PumaFPV/PMK/Documentation/FPC-Contact-layout.png

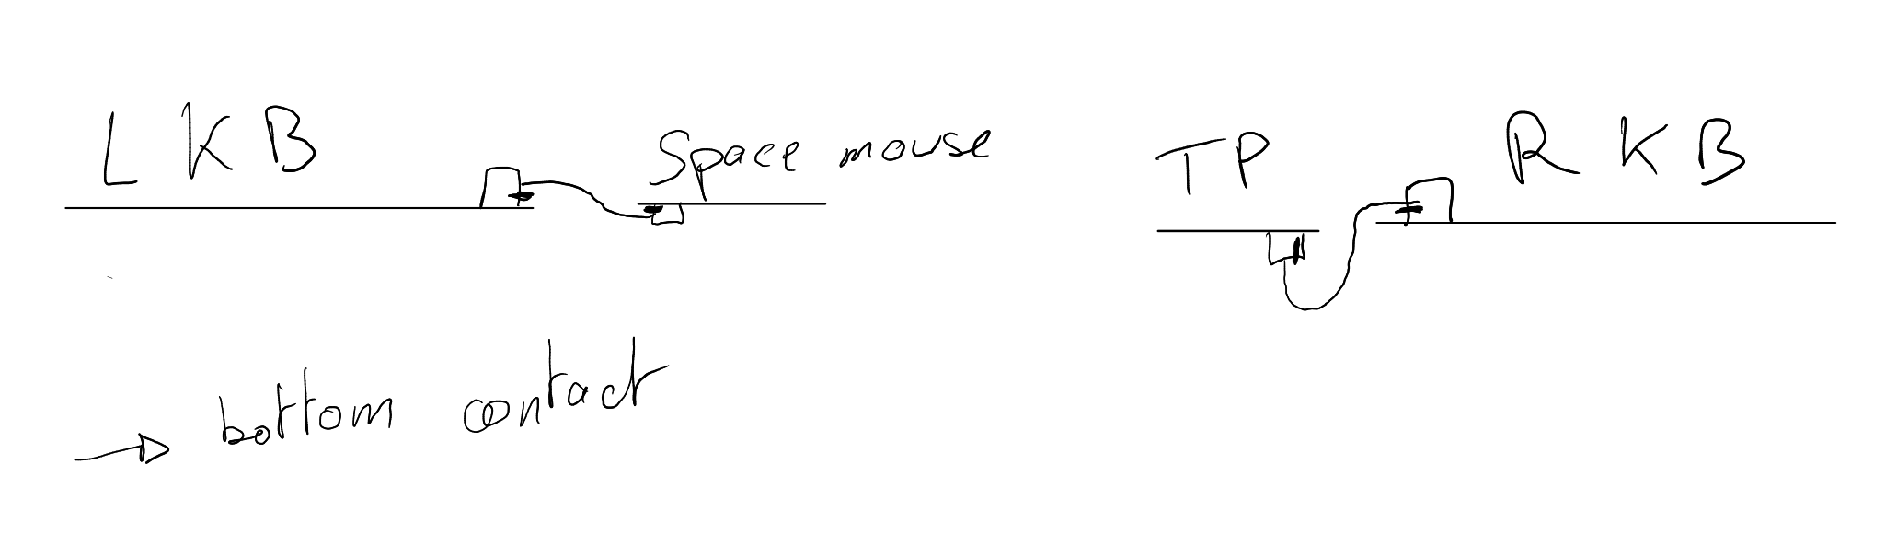
Documentation/FPC-Contact-layout.png
