PumaFPV/PMK/Documentation/Marketing/rightKB_nobg.png

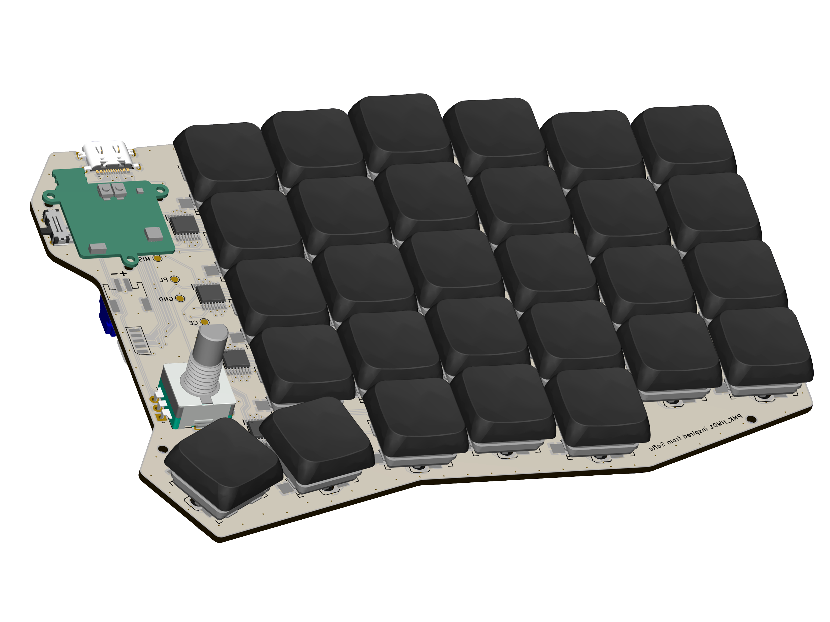
Documentation/Marketing/rightKB_nobg.png
