PumaFPV/PMK/Software/pmk_configurator/TopView.png

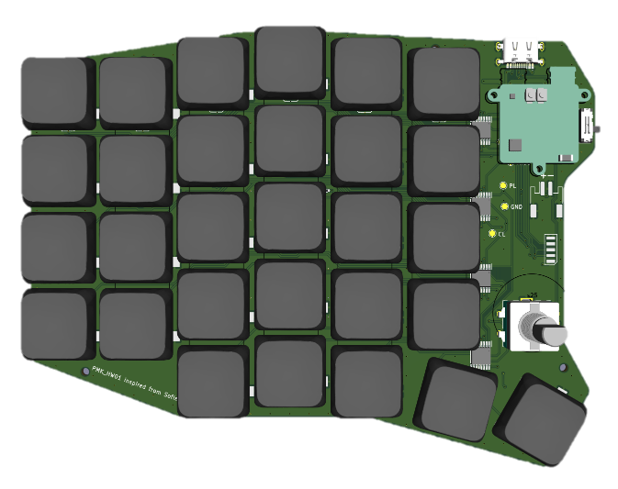
Software/pmk_configurator/TopView.png
