PumaFPV/PMK/Software/pmk_configurator/TopViewWithCasingNoBG.png

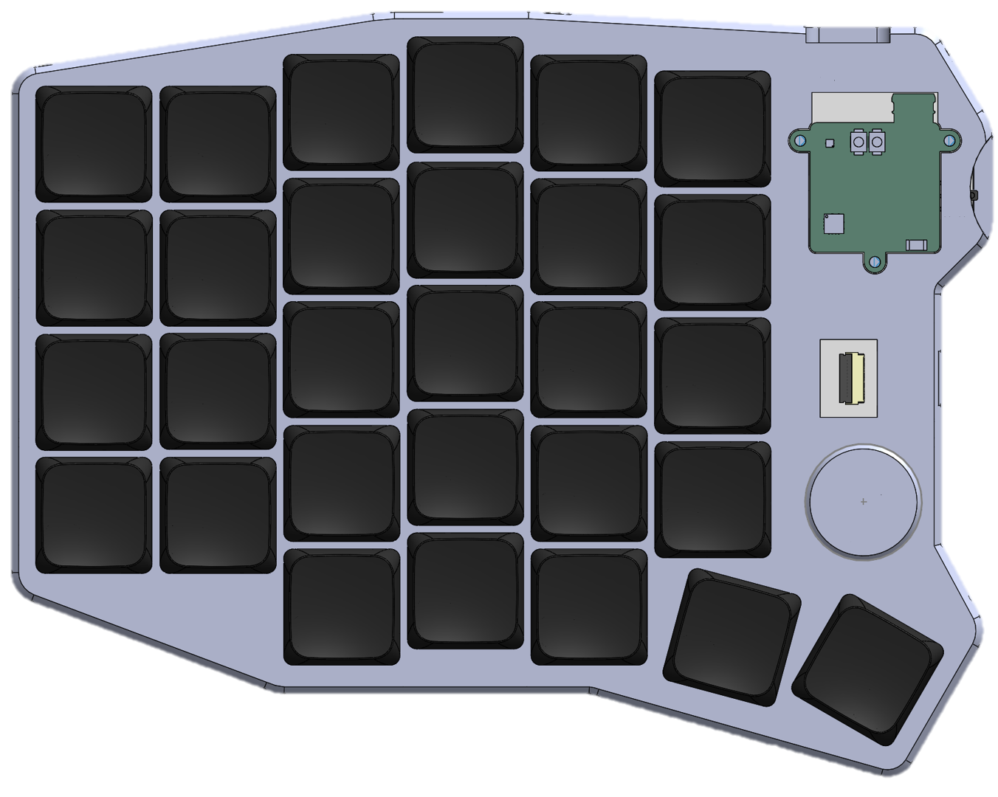
Software/pmk_configurator/TopViewWithCasingNoBG.png
