PumaFPV/PMK/Software/Ticket documentation/Debounce/key_debounce1.png

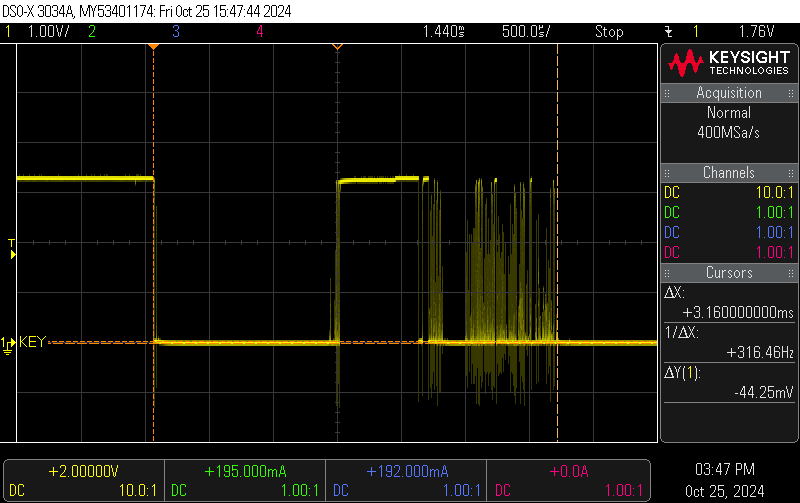
Software/Ticket documentation/Debounce/key_debounce1.png
