PumaFPV/PMK/Software/Ticket documentation/Debounce/key_debounce2.png

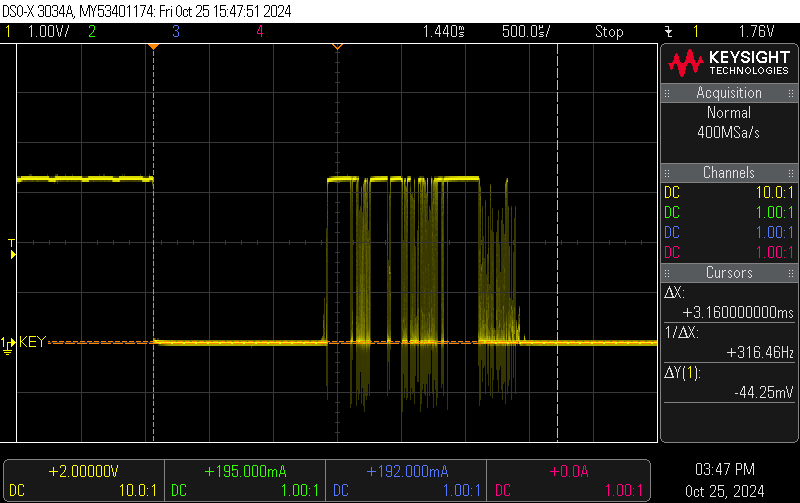
Software/Ticket documentation/Debounce/key_debounce2.png
