PumaFPV/PMK/Software/Ticket documentation/Debounce/key_debounce4.png

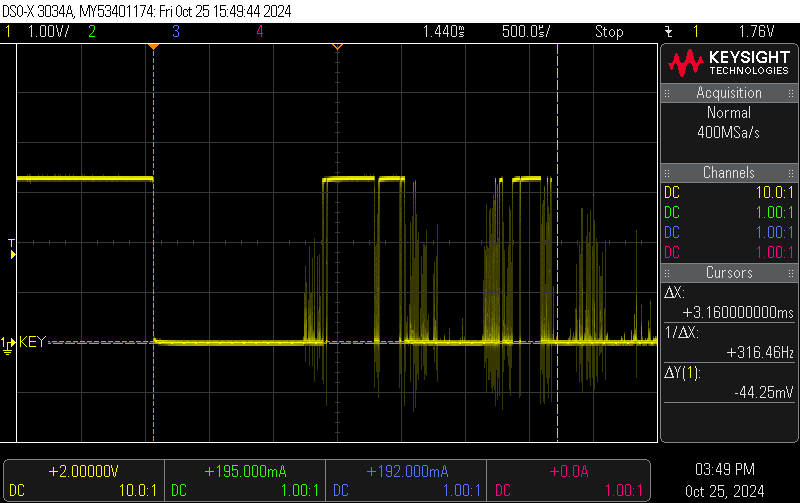
Software/Ticket documentation/Debounce/key_debounce4.png
