PumaFPV/PMK/Software/Ticket documentation/Debounce/key_debounce.png

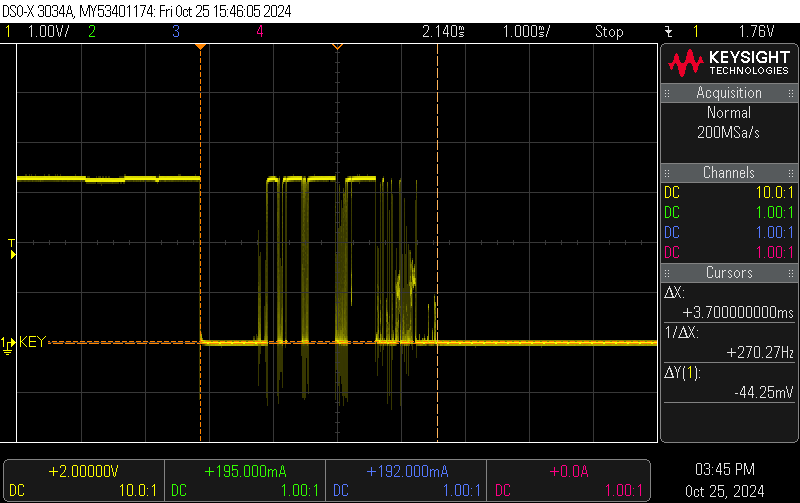
Software/Ticket documentation/Debounce/key_debounce.png
