PumaFPV/PMK/Software/Ticket documentation/Debounce/PU_KEY_AC2.png

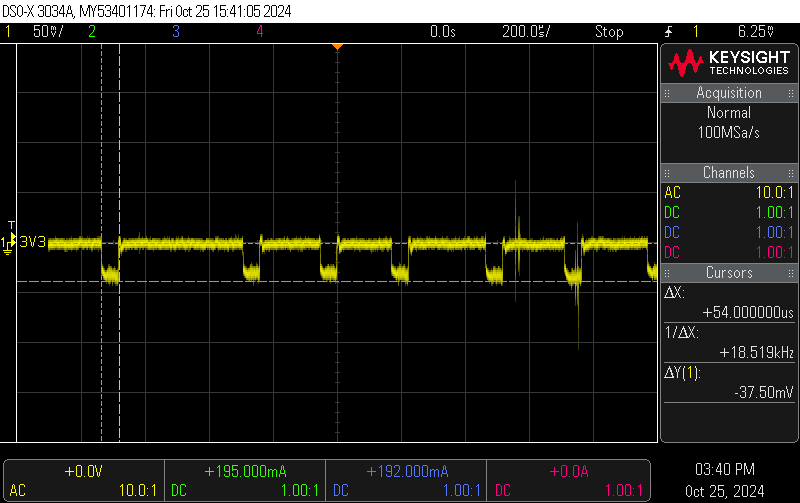
Software/Ticket documentation/Debounce/PU_KEY_AC2.png
