PumaFPV/PMK/Software/Ticket documentation/Debounce/PU_KEY_AC5.png

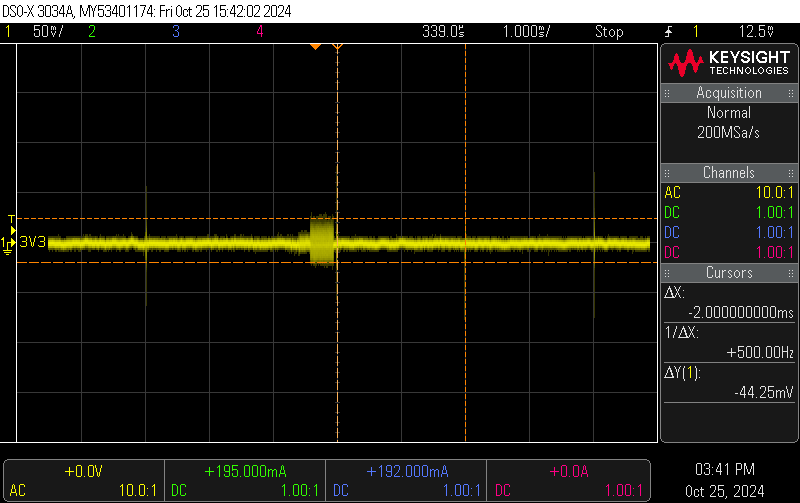
Software/Ticket documentation/Debounce/PU_KEY_AC5.png
