PumaFPV/PMK/Software/Ticket documentation/Debounce/PU_KEY_AC6.png

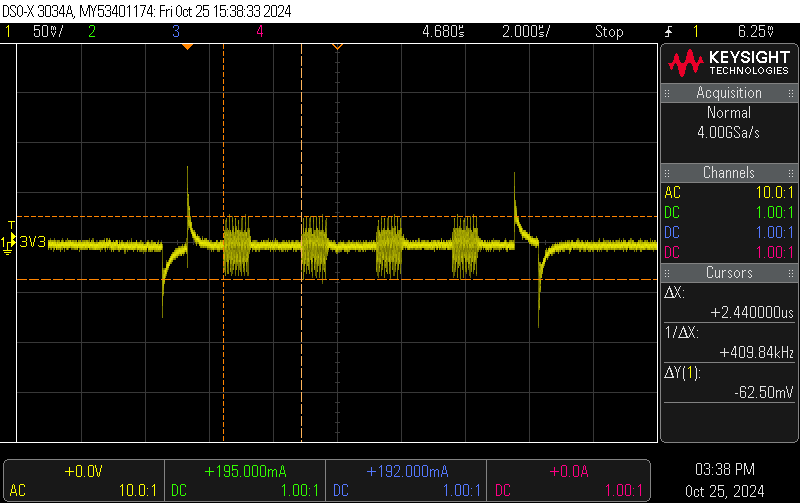
Software/Ticket documentation/Debounce/PU_KEY_AC6.png
