PumaFPV/PMK/Software/Ticket documentation/Debounce/PU_KEY_AC.png

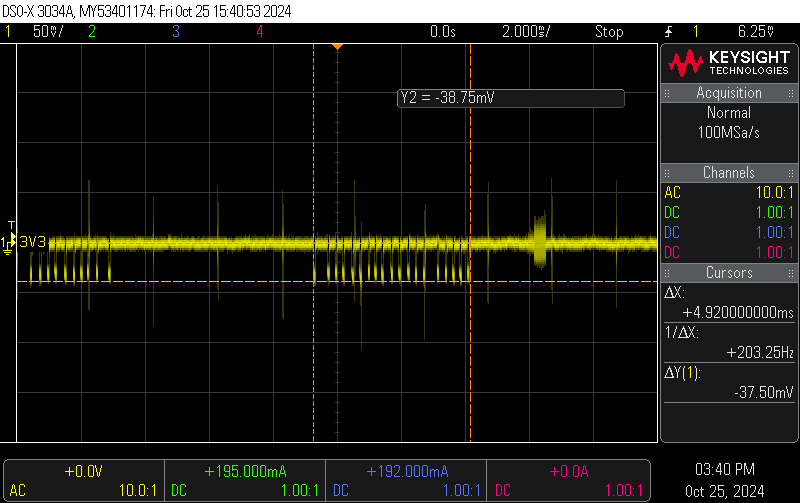
Software/Ticket documentation/Debounce/PU_KEY_AC.png
