PumaFPV/PMK/Mecha/Dongle/PMK_Dongle_00.step

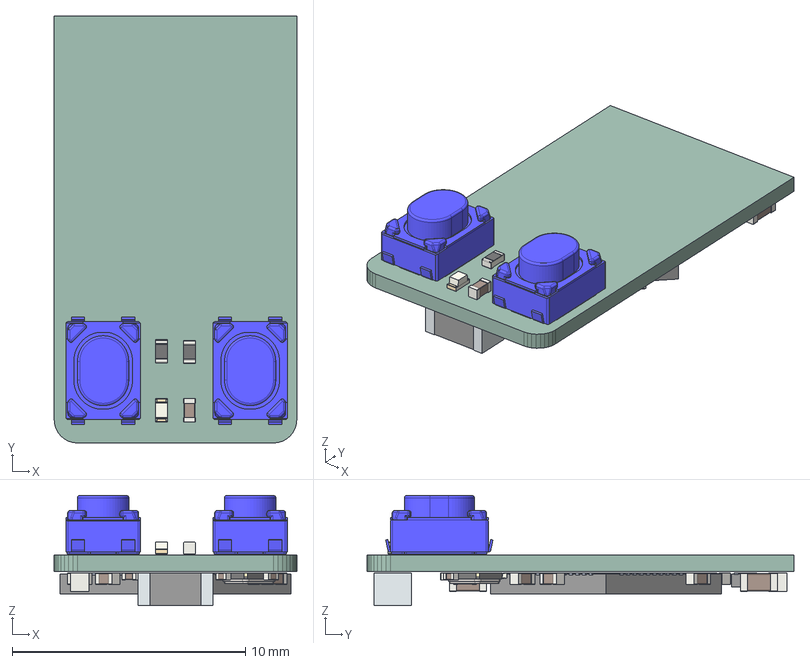
[picture p38: CAD file, 2024-03-06]
Mecha/Dongle/PMK_Dongle_00.step
10.4 x 18.3 x 4.72 mm
PMK_Dongle PCB
