PumaFPV/PMK/Mecha/Keyboard/KeyCap holder/holder^keycap holder.STL

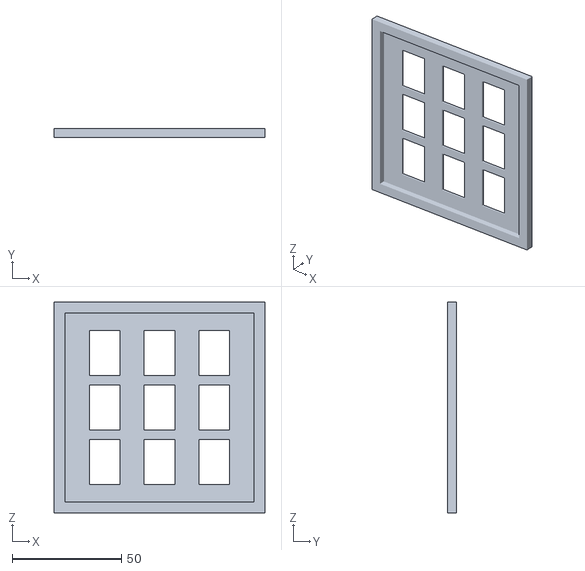
[picture p39: CAD file, 2023-05-14]
Mecha/Keyboard/KeyCap holder/holder^keycap holder.STL
96.7 x 4.00 x 96.7
