PumaFPV/PMK/Mecha/Keyboard/Keycap/MBK_Keycap_-_1.5u.SLDPRT

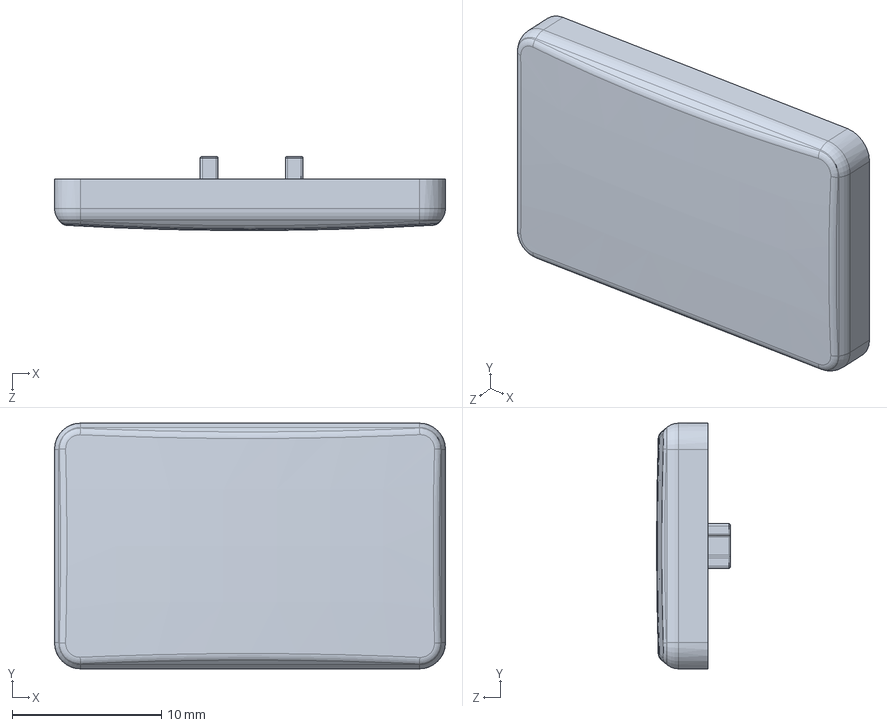
[picture p40: CAD file, 2023-08-28]
Mecha/Keyboard/Keycap/MBK_Keycap_-_1.5u.SLDPRT
26.2 x 16.5 x 4.95 mm
