PumaFPV/PMK/Mecha/Keyboard/PMK_00/PMK_Keyboard.step.STL

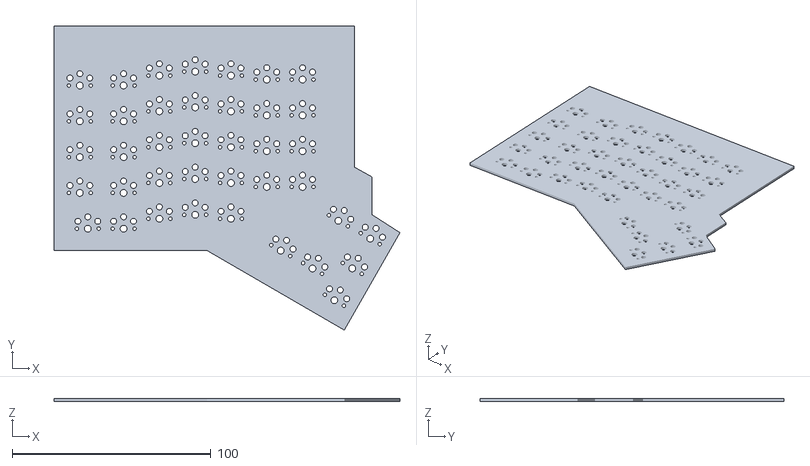
[picture p41: CAD file, 2023-01-25]
Mecha/Keyboard/PMK_00/PMK_Keyboard.step.STL
174.0 x 153.0 x 1.60
