PumaFPV/PMK/Mecha/Keyboard/PMK_01/UpperCasing.SLDPRT

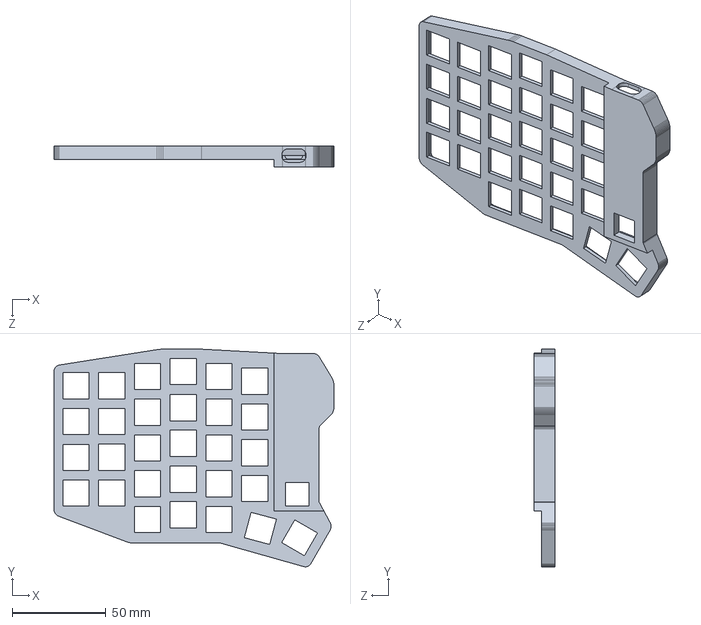
[picture p42: CAD file, 2024-06-07]
Mecha/Keyboard/PMK_01/UpperCasing.SLDPRT
149.2 x 116.0 x 11.0 mm
