PumaFPV/PMK/Mecha/Keyboard/PMK_02/export/right plate TO  BE MIRRORED.STL

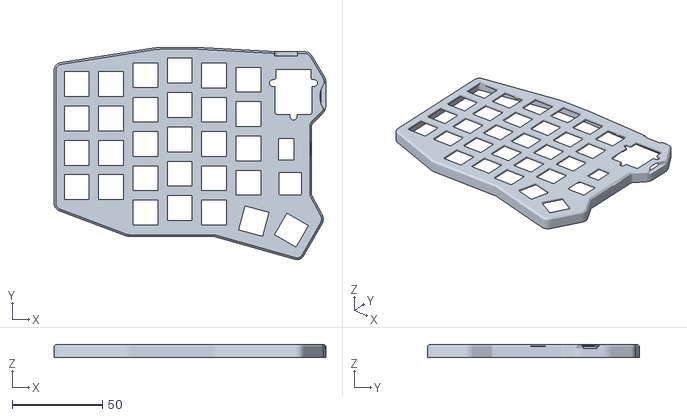
[picture p43: CAD file, 2024-07-18]
Mecha/Keyboard/PMK_02/export/right plate TO BE MIRRORED.STL
150.9 x 117.8 x 7.20
