PumaFPV/PMK/Mecha/Deej/Potar.SLDPRT

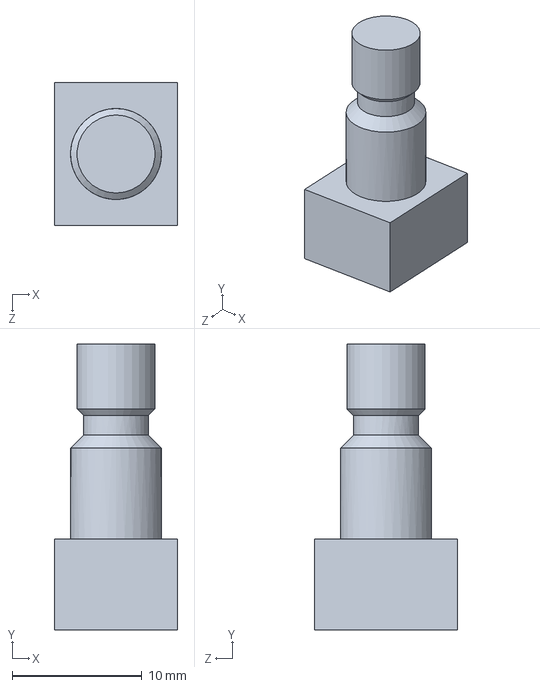
[picture p44: CAD file, 2023-12-10]
Mecha/Deej/Potar.SLDPRT
9.50 x 22.0 x 11.0 mm
