PumaFPV/PMK/Mecha/Keyboard/KeyCap holder/keycap matrice.SLDPRT

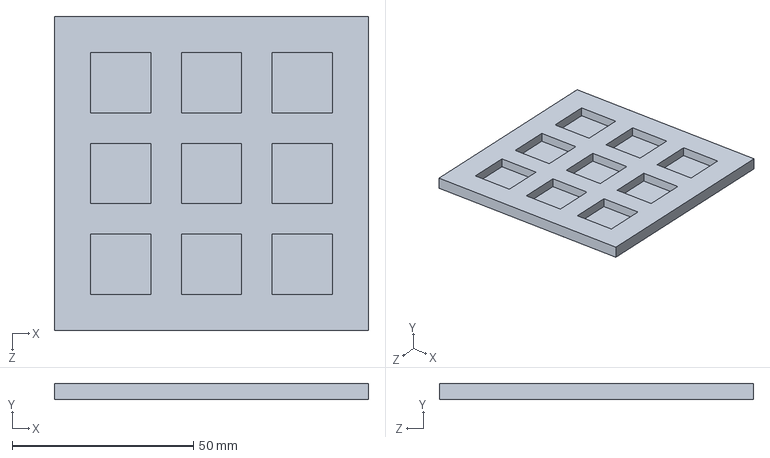
[picture p45: CAD file, 2023-05-14]
Mecha/Keyboard/KeyCap holder/keycap matrice.SLDPRT
86.7 x 4.50 x 86.7 mm
