PumaFPV/PMK/Mecha/Keyboard/Keycap/MBK_Keycap_-_2u.SLDPRT

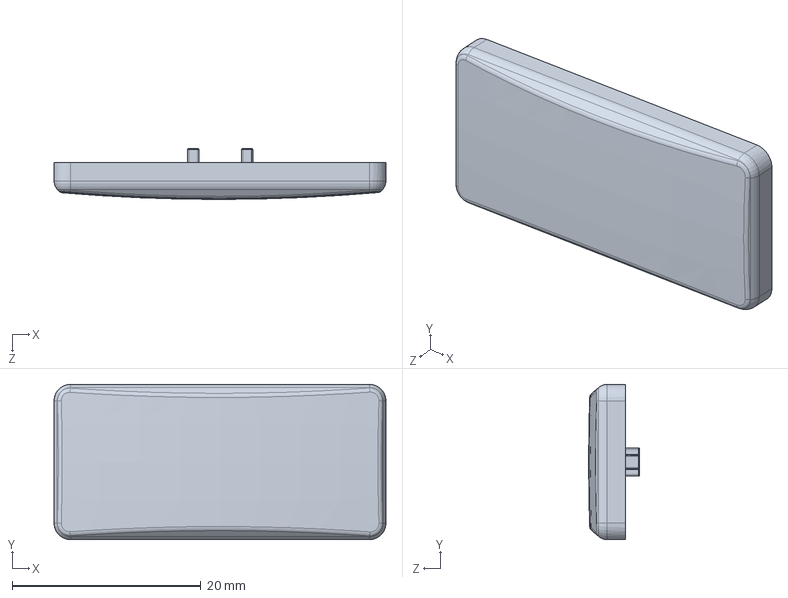
[picture p46: CAD file, 2023-08-28]
Mecha/Keyboard/Keycap/MBK_Keycap_-_2u.SLDPRT
35.2 x 16.5 x 5.39 mm
