PumaFPV/PMK/Mecha/Keyboard/PMK_01/keycap.SLDPRT

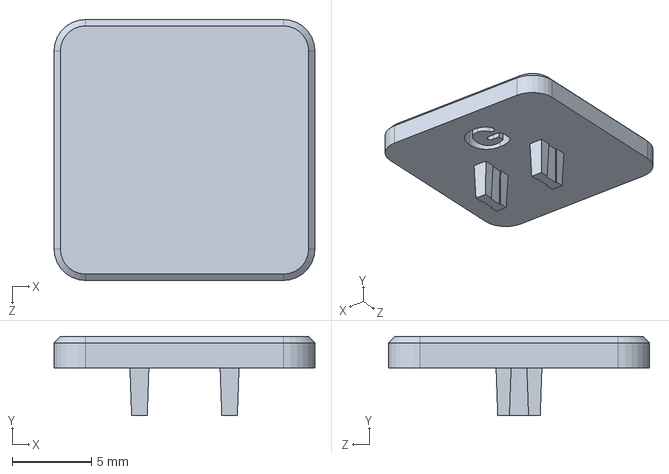
[picture p47: CAD file, 2024-04-26]
Mecha/Keyboard/PMK_01/keycap.SLDPRT
16.5 x 5.00 x 16.5 mm
