PumaFPV/PMK/Mecha/Keyboard/PMK_02/Bottom.SLDPRT

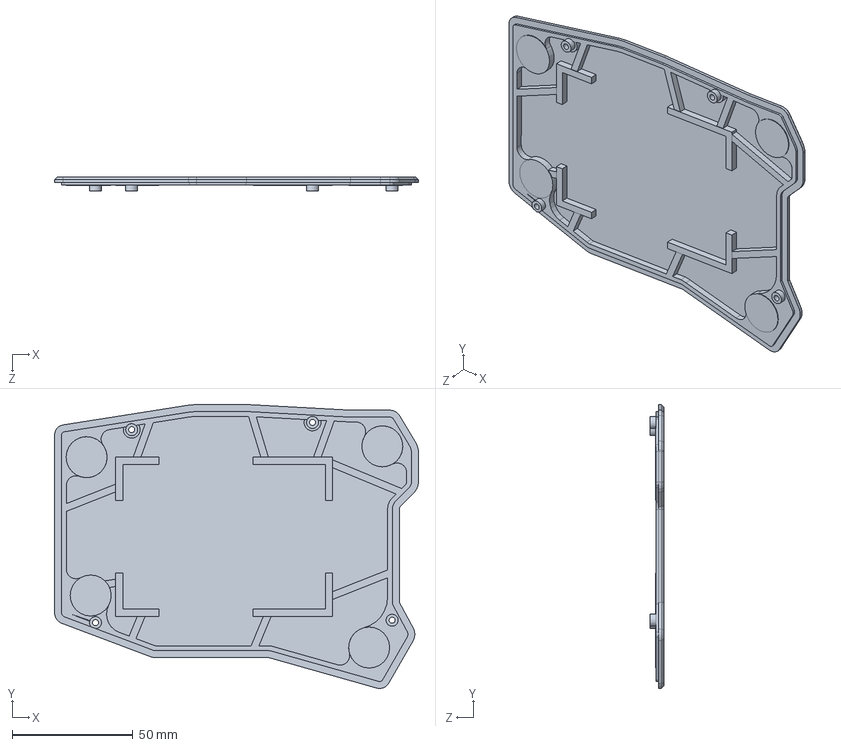
[picture p48: CAD file, 2024-07-18]
Mecha/Keyboard/PMK_02/Bottom.SLDPRT
150.9 x 117.8 x 5.70 mm
