PumaFPV/PMK/Mecha/Deej/Slider.SLDPRT

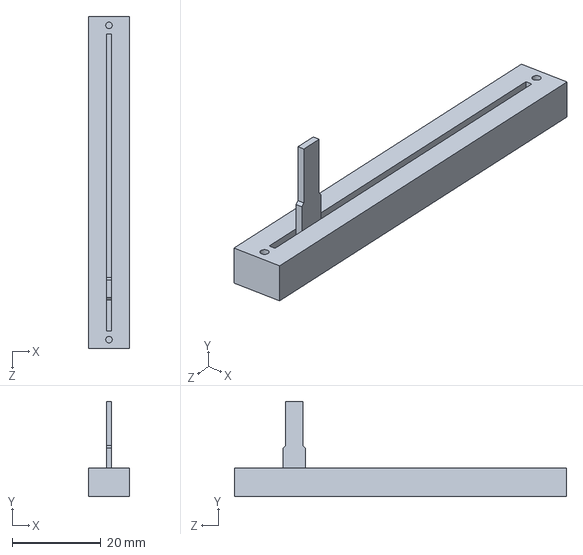
[picture p49: CAD file, 2023-12-10]
Mecha/Deej/Slider.SLDPRT
9.30 x 21.5 x 75.0 mm
