PumaFPV/PMK/Mecha/Dongle/Casing2.2mm.STL

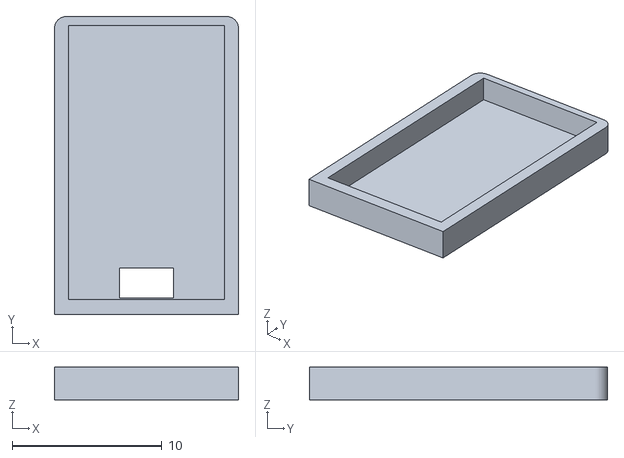
[picture p50: CAD file, 2023-04-30]
Mecha/Dongle/Casing2.2mm.STL
12.3 x 19.9 x 2.20
