PumaFPV/PMK/Mecha/Deej/Mute.SLDPRT

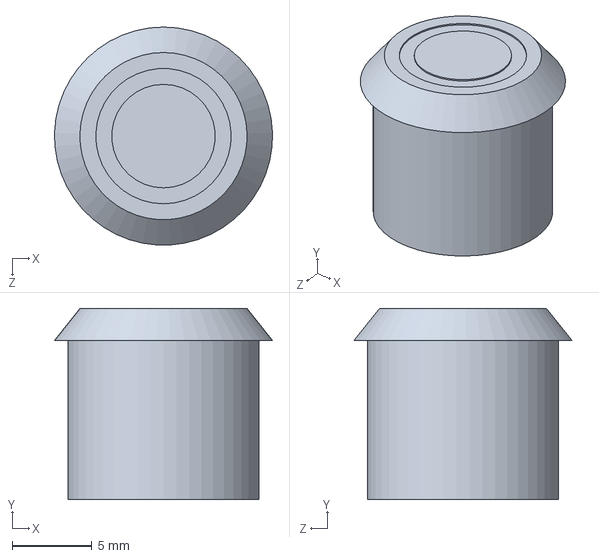
[picture p51: CAD file, 2023-12-10]
Mecha/Deej/Mute.SLDPRT
13.7 x 12.0 x 13.7 mm
