PumaFPV/PMK/Mecha/Deej/Bottom.SLDPRT

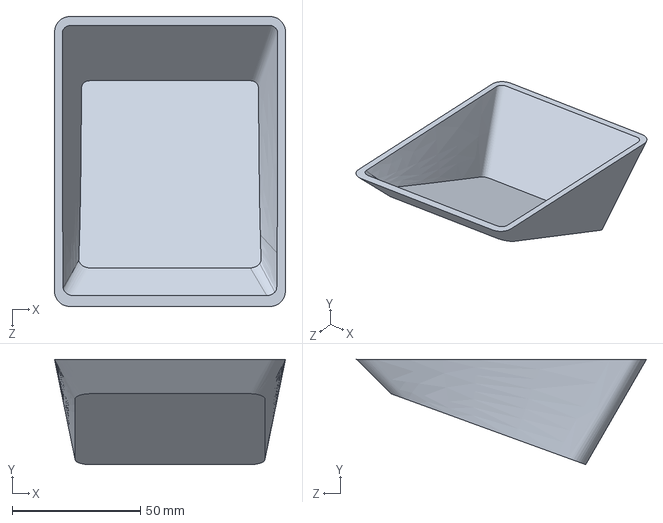
[picture p52: CAD file, 2023-12-10]
Mecha/Deej/Bottom.SLDPRT
90.0 x 41.0 x 113.0 mm
