PumaFPV/PMK/Mecha/Dongle/PMK_Dongle.step

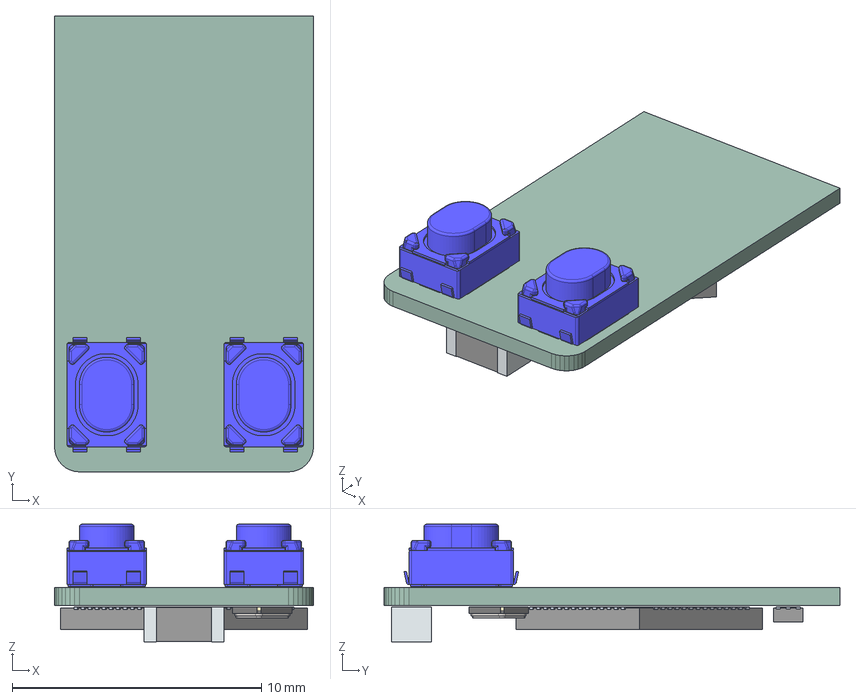
[picture p53: CAD file, 2023-04-29]
Mecha/Dongle/PMK_Dongle.step
10.4 x 18.3 x 4.72 mm
PCB
