PumaFPV/PMK/Mecha/Deej/Top_cover.SLDPRT

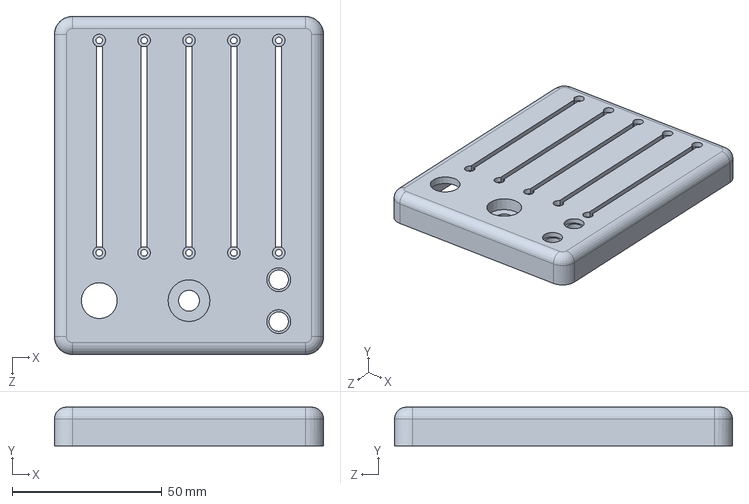
[picture p54: CAD file, 2023-12-10]
Mecha/Deej/Top_cover.SLDPRT
90.0 x 13.0 x 113.0 mm
