PumaFPV/PMK/Mecha/Deej/Top.SLDPRT

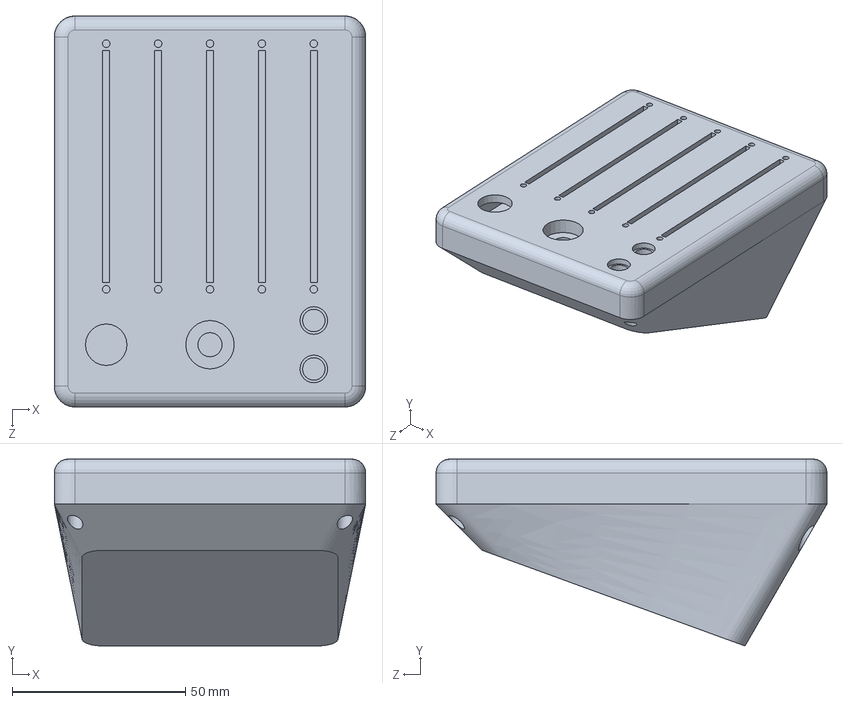
[picture p55: CAD file, 2023-12-10]
Mecha/Deej/Top.SLDPRT
90.0 x 54.0 x 113.0 mm
