PumaFPV/PMK/Mecha/Deej/Switch.SLDPRT

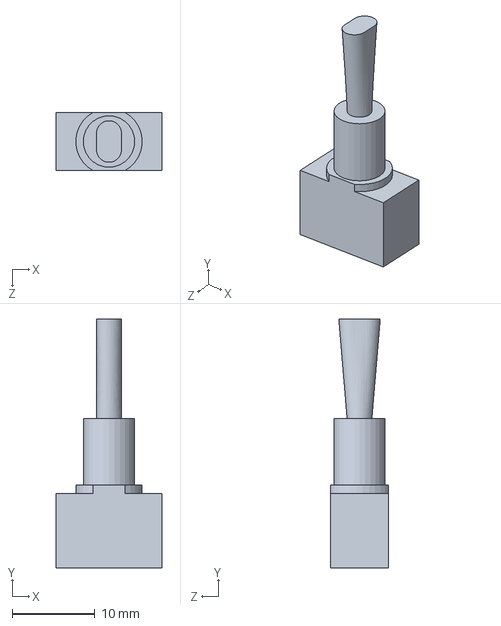
[picture p56: CAD file, 2023-12-10]
Mecha/Deej/Switch.SLDPRT
12.8 x 30.0 x 7.00 mm
