PumaFPV/PMK/Mecha/Deej/Slider top.SLDPRT

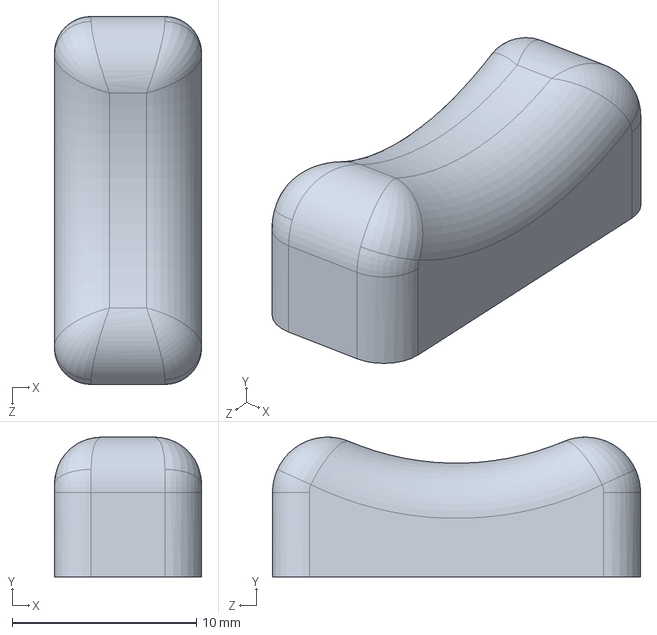
[picture p57: CAD file, 2023-12-10]
Mecha/Deej/Slider top.SLDPRT
8.00 x 7.60 x 20.0 mm
