PumaFPV/PMK/Hardware/PMK_Dongle/PMK_Dongle_HW01/PMK_Dongle_HW01.kicad_pcb

## KiCad design Hardware/PMK_Dongle/PMK_Dongle_HW01/PMK_Dongle_HW01.kicad_pcb (2025-06-30)

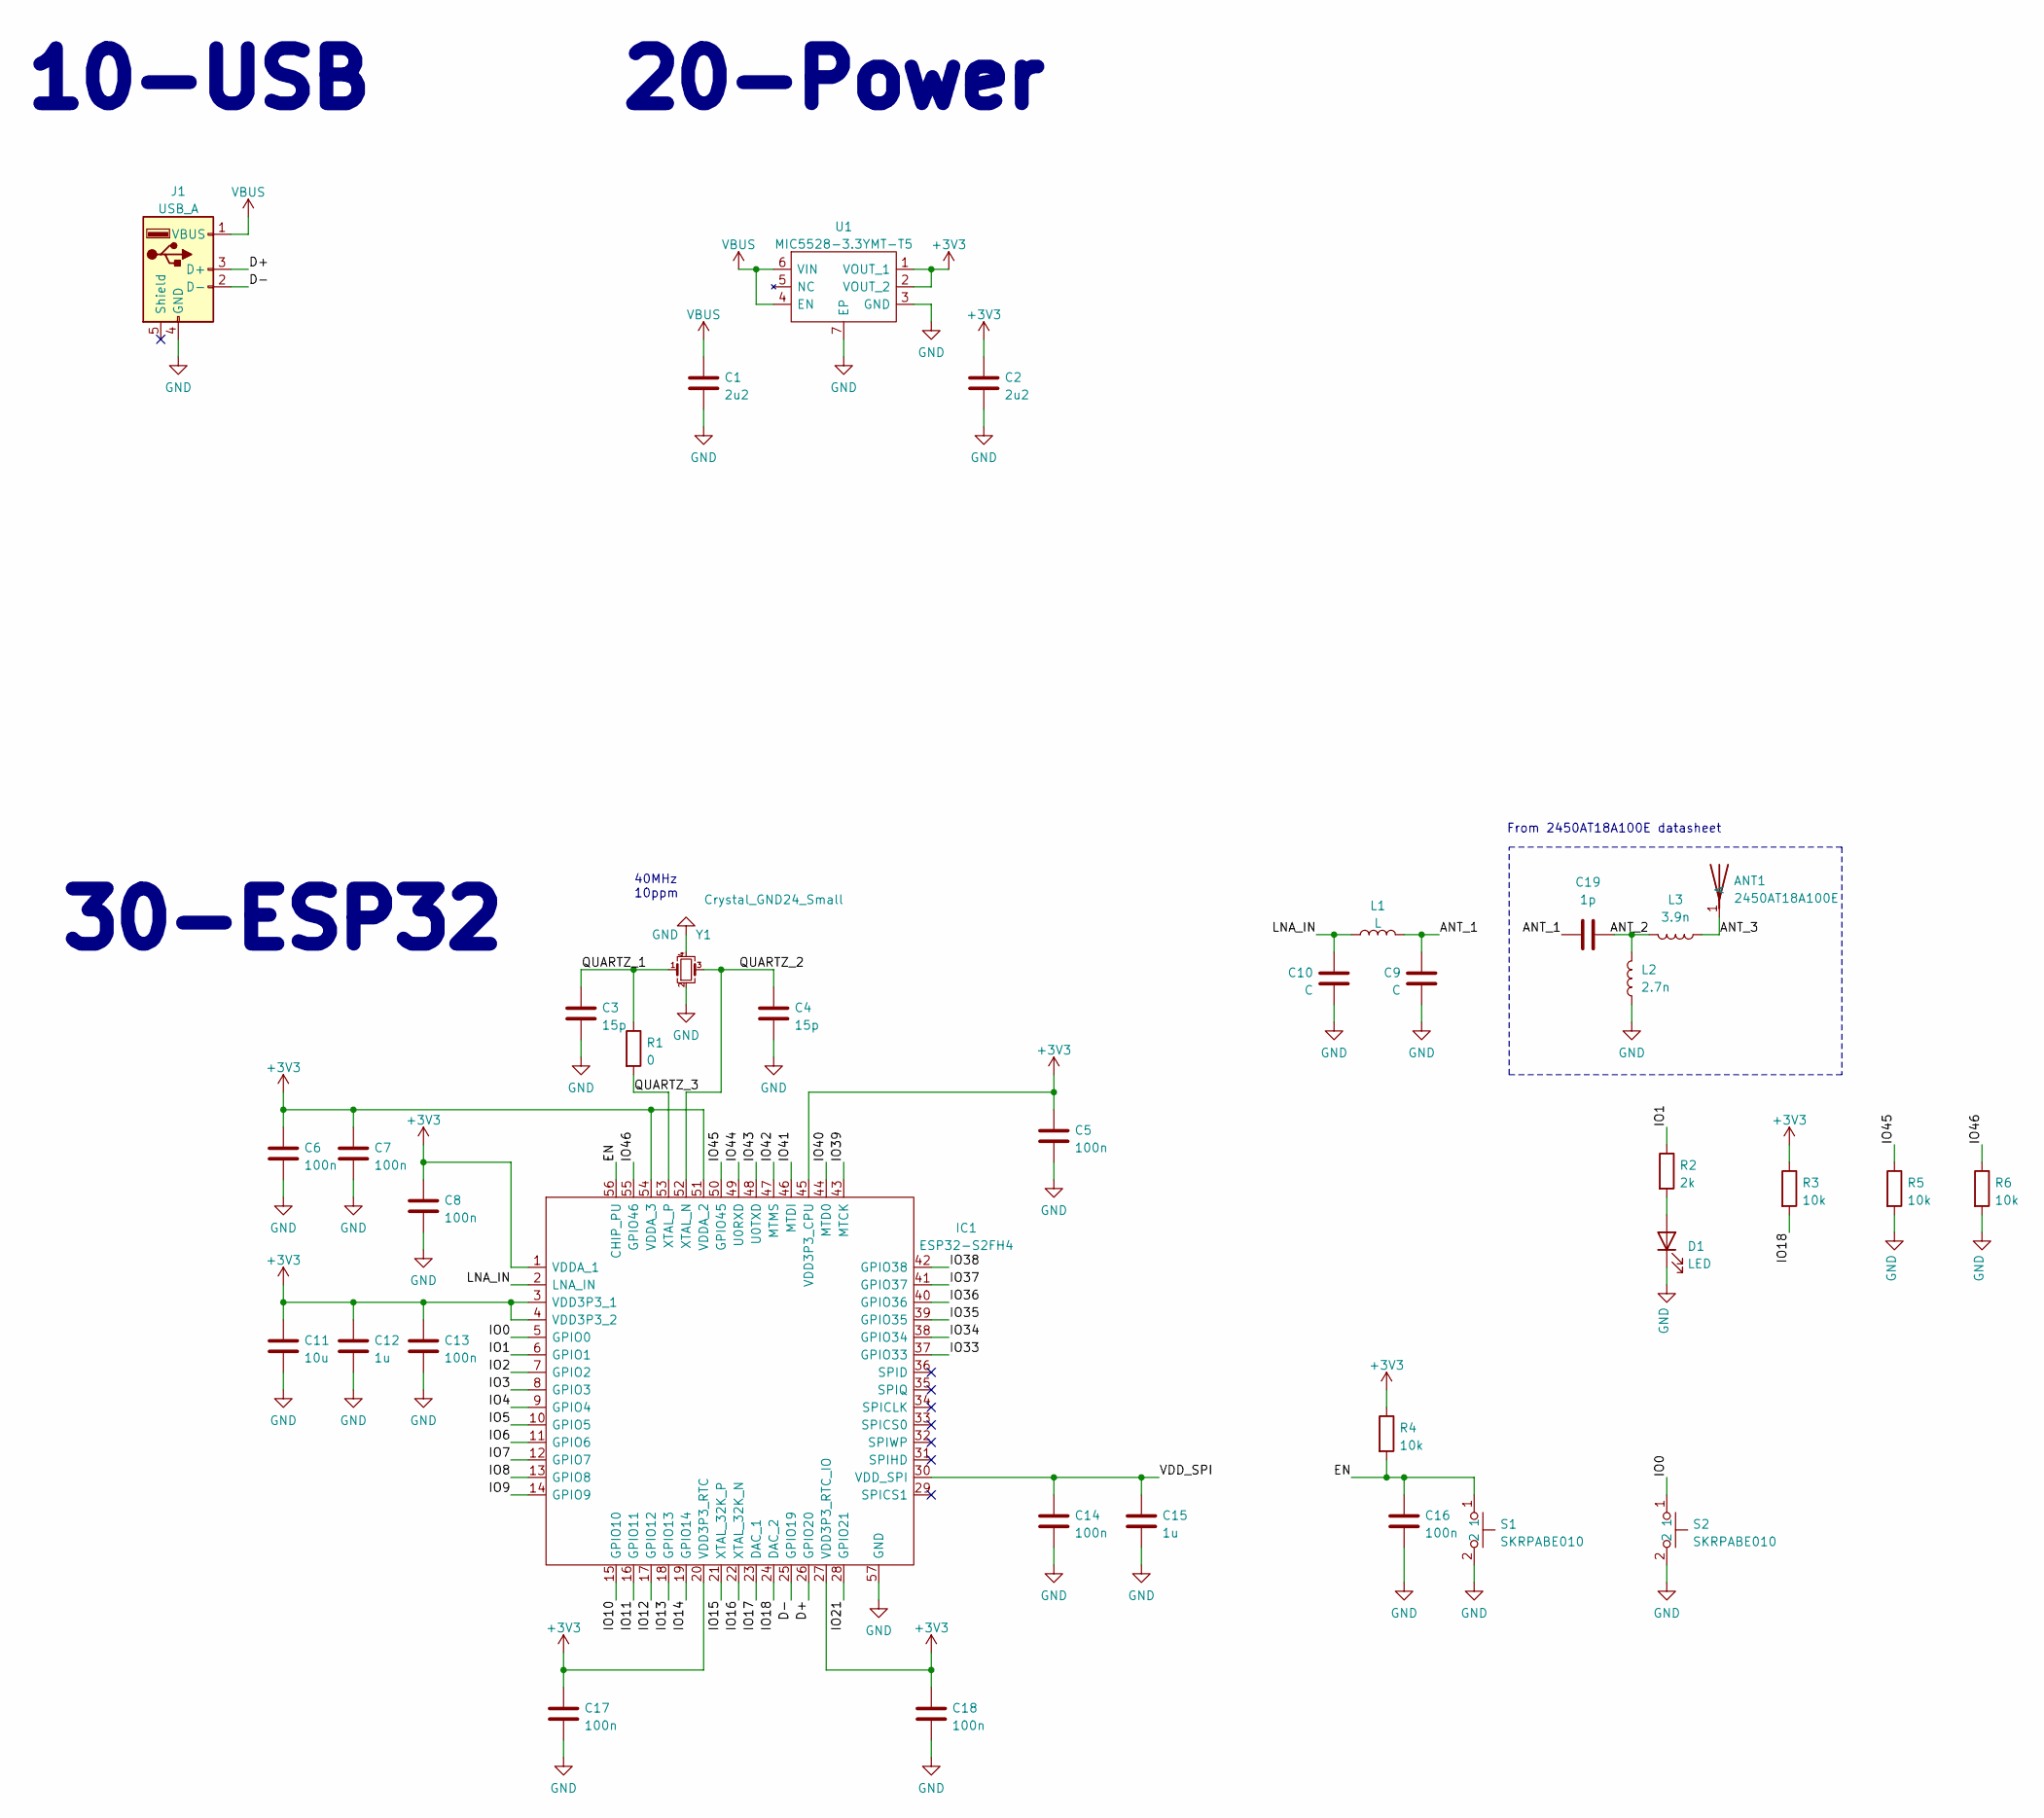
[picture p58: schematic PMK_Dongle_HW01.kicad_sch, PMK_Dongle]

Parts:
ANT1: 2450AT18A100E; ANTC3216X140N; Mouser Part Number 609-2450AT18A100E
C1, C2: 2u2; C_0603_1608Metric
C3, C4: 15p; C_0201_0603Metric
C5, C6, C7, C8, C13, C14, C16, C17, C18: 100n; C_0402_1005Metric
C9, C10: C; C_0201_0603Metric
C11: 10u; C_0603_1608Metric
C12, C15: 1u; C_0402_1005Metric
C19: 1p; C_0402_1005Metric
D1: LED; LED_0402_1005Metric
IC1: ESP32-S2FH4; QFN40P700X700X90-57N-D; Mouser Part Number 356-ESP32-S2FH4
J1: USB_A; USB_PCB
L1: L; L_0201_0603Metric
L2: 2.7n; L_0402_1005Metric
L3: 3.9n; L_0402_1005Metric
R1: 0; R_0201_0603Metric
R2: 2k; R_0402_1005Metric
R3, R4, R5, R6: 10k; R_0201_0603Metric
S1, S2: SKRPABE010; B3U-1000P; Mouser Part Number 688-SKRPAB
U1: MIC5528-3.3YMT-T5; SON40P120X120X60-7N-D; Mouser Part Number 998-MIC5528-3.3YMTT5
Y1: Crystal_GND24_Small; Crystal_SMD_2016-4Pin_2.0x1.6mm

Connections:
+3V3: C2.1, C5.1, C6.1, C7.1, C8.1, C11.1, C12.1, C13.1, C17.1, C18.1, IC1.1 (VDDA_1), IC1.3 (VDD3P3_1), IC1.4 (VDD3P3_2), IC1.20 (VDD3P3_RTC), IC1.27 (VDD3P3_RTC_IO), IC1.45 (VDD3P3_CPU), IC1.51 (VDDA_2), IC1.54 (VDDA_3), R3.1, R4.1, U1.1 (VOUT_1), U1.2 (VOUT_2)
/ANT_1: C9.1, C19.2, L1.1
/ANT_2: C19.1, L2.1, L3.1
/ANT_3: ANT1.1 (A), L3.2
/D+: IC1.26 (GPIO20), J1.3 (D+)
/D-: IC1.25 (GPIO19), J1.2 (D-)
/EN: C16.1, IC1.56 (CHIP_PU), R4.2, S1.1
/IO0: IC1.5 (GPIO0), S2.1
/IO1: IC1.6 (GPIO1), R2.1
/IO2: IC1.7 (GPIO2)
/IO3: IC1.8 (GPIO3)
/IO4: IC1.9 (GPIO4)
/IO5: IC1.10 (GPIO5)
/IO6: IC1.11 (GPIO6)
/IO7: IC1.12 (GPIO7)
/IO8: IC1.13 (GPIO8)
/IO9: IC1.14 (GPIO9)
/IO10: IC1.15 (GPIO10)
/IO11: IC1.16 (GPIO11)
/IO12: IC1.17 (GPIO12)
/IO13: IC1.18 (GPIO13)
/IO14: IC1.19 (GPIO14)
/IO15: IC1.21 (XTAL_32K_P)
/IO16: IC1.22 (XTAL_32K_N)
/IO17: IC1.23 (DAC_1)
/IO18: IC1.24 (DAC_2), R3.2
/IO21: IC1.28 (GPIO21)
/IO33: IC1.37 (GPIO33)
/IO34: IC1.38 (GPIO34)
/IO35: IC1.39 (GPIO35)
/IO36: IC1.40 (GPIO36)
/IO37: IC1.41 (GPIO37)
/IO38: IC1.42 (GPIO38)
/IO39: IC1.43 (MTCK)
/IO40: IC1.44 (MTD0)
/IO41: IC1.46 (MTDI)
/IO42: IC1.47 (MTMS)
/IO43: IC1.48 (U0TXD)
/IO44: IC1.49 (U0RXD)
/IO45: IC1.50 (GPIO45), R5.1
/IO46: IC1.55 (GPIO46), R6.1
/LNA_IN: C10.1, IC1.2 (LNA_IN), L1.2
/QUARTZ_1: C3.1, R1.1, Y1.1
/QUARTZ_2: C4.1, IC1.52 (XTAL_N), Y1.3
/QUARTZ_3: IC1.53 (XTAL_P), R1.2
/VDD_SPI: C14.1, C15.1, IC1.30 (VDD_SPI)
GND: C1.2, C2.2, C3.2, C4.2, C5.2, C6.2, C7.2, C8.2, C9.2, C10.2, C11.2, C12.2, C13.2, C14.2, C15.2, C16.2, C17.2, C18.2, D1.1 (K), IC1.57 (GND), J1.4 (GND), L2.2, R5.2, R6.2, S1.2, S2.2, U1.3 (GND), U1.7 (EP), Y1.2, Y1.4
unnamed: D1.2 (A), R2.2
VBUS: C1.1, J1.1 (VBUS), U1.4 (EN), U1.6 (VIN)

Notes on the sheet:
From 2450AT18A100E datasheet
10-USB
30-ESP32
40MHz 10ppm
20-Power

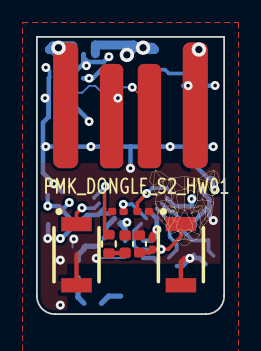
[picture p59: board PMK_Dongle_HW01.kicad_pcb from above]

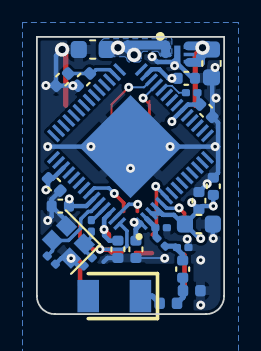
[picture p60: board PMK_Dongle_HW01.kicad_pcb from below]

Board: 4 copper layers, 10.4 x 15.4 mm, 36 parts (27 on the bottom side), 20 nets.
