PumaFPV/PMK/Hardware/PMK_SpaceMouse/PMK_SpaceMouse_01/PMK_SpaceMouse_01.kicad_pcb

## KiCad design Hardware/PMK_SpaceMouse/PMK_SpaceMouse_01/PMK_SpaceMouse_01.kicad_pcb (2025-06-24)

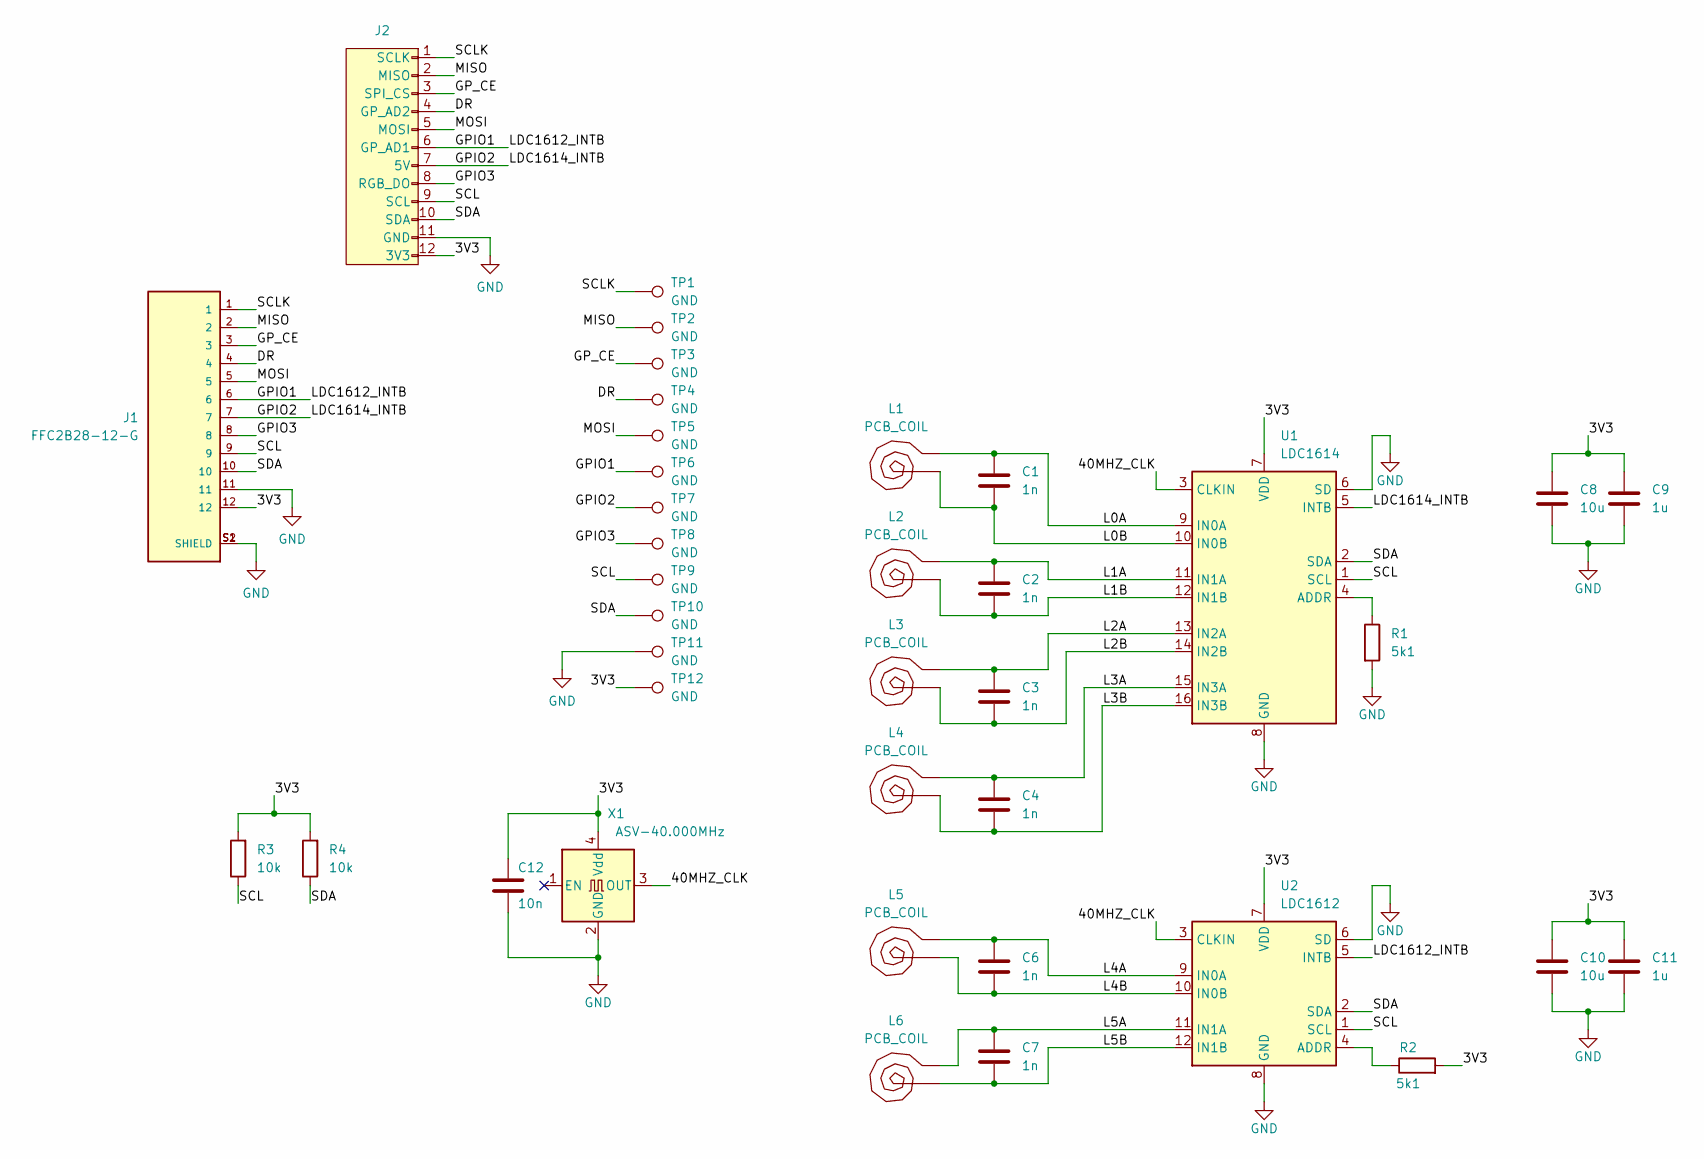
[picture p61: schematic PMK_SpaceMouse_01.kicad_sch, PMK_SpaceMouse]

Parts:
C1, C2, C3, C4, C6, C7: 1n; C_0402_1005Metric
C8, C10: 10u; C_0402_1005Metric
C9, C11: 1u; C_0402_1005Metric
C12: 10n; C_0402_1005Metric
J1: FFC2B28-12-G; GCT_FFC2B28-12-G; PARTREV A; DigiKey_Part_Number 2073-FFC2B28-12-GTR-ND
J2: vik-module-connector; vik-module-connector-horizontal
L1, L2, L3, L4, L5, L6: PCB_COIL; COIL_PCB
R1, R2: 5k1; R_0402_1005Metric
R3, R4: 10k; R_0402_1005Metric
TP1, TP2, TP3, TP4, TP5, TP6, TP7, TP8, TP9, TP10, TP11, TP12: GND; TestPoint_Pad_D1.5mm
U1: LDC1614; WQFN-16-1EP_4x4mm_P0.5mm_EP2.6x2.6mm
U2: LDC1612; WSON-12-1EP_4x4mm_P0.5mm_EP2.6x3mm
X1: ASV-40.000MHz; Oscillator_SMD_Abracon_ASV-4Pin_7.0x5.1mm

Connections:
/3V3: C8.1, C9.1, C10.1, C11.1, C12.1, J1.12, J2.12 (3V3), R2.2, R3.2, R4.2, TP12.1, U1.7 (VDD), U2.7 (VDD), X1.4 (Vdd)
/40MHZ_CLK: U1.3 (CLKIN), U2.3 (CLKIN), X1.3 (OUT)
/DR: J1.4, J2.4 (GP_AD2), TP4.1
/GPIO1: J1.6, J2.6 (GP_AD1), TP6.1, U2.5 (INTB)
/GPIO2: J1.7, J2.7 (5V), TP7.1, U1.5 (INTB)
/GPIO3: J1.8, J2.8 (RGB_DO), TP8.1
/GP_CE: J1.3, J2.3 (SPI_CS), TP3.1
/L0A: C1.1, L1.1, U1.9 (IN0A)
/L0B: C1.2, L1.2, U1.10 (IN0B)
/L1A: C2.1, L2.1, U1.11 (IN1A)
/L1B: C2.2, L2.2, U1.12 (IN1B)
/L2A: C3.1, L3.1, U1.13 (IN2A)
/L2B: C3.2, L3.2, U1.14 (IN2B)
/L3A: C4.1, L4.1, U1.15 (IN3A)
/L3B: C4.2, L4.2, U1.16 (IN3B)
/L4A: C6.1, L5.1, U2.9 (IN0A)
/L4B: C6.2, L5.2, U2.10 (IN0B)
/L5A: C7.1, L6.1, U2.11 (IN1A)
/L5B: C7.2, L6.2, U2.12 (IN1B)
/MISO: J1.2, J2.2 (MISO), TP2.1
/MOSI: J1.5, J2.5 (MOSI), TP5.1
/SCL: J1.9, J2.9 (SCL), R3.1, TP9.1, U1.1 (SCL), U2.1 (SCL)
/SCLK: J1.1, J2.1 (SCLK), TP1.1
/SDA: J1.10, J2.10 (SDA), R4.1, TP10.1, U1.2 (SDA), U2.2 (SDA)
GND: C8.2, C9.2, C10.2, C11.2, C12.2, J1.11, J1.S1 (SHIELD), J1.S2 (SHIELD), J2.11 (GND), R1.2, TP11.1, U1.6 (SD), U1.8 (GND), U1.17 (GND), U2.6 (SD), U2.8 (GND), U2.13 (GND), X1.2 (GND)
unnamed: R1.1, U1.4 (ADDR)
unnamed: R2.1, U2.4 (ADDR)

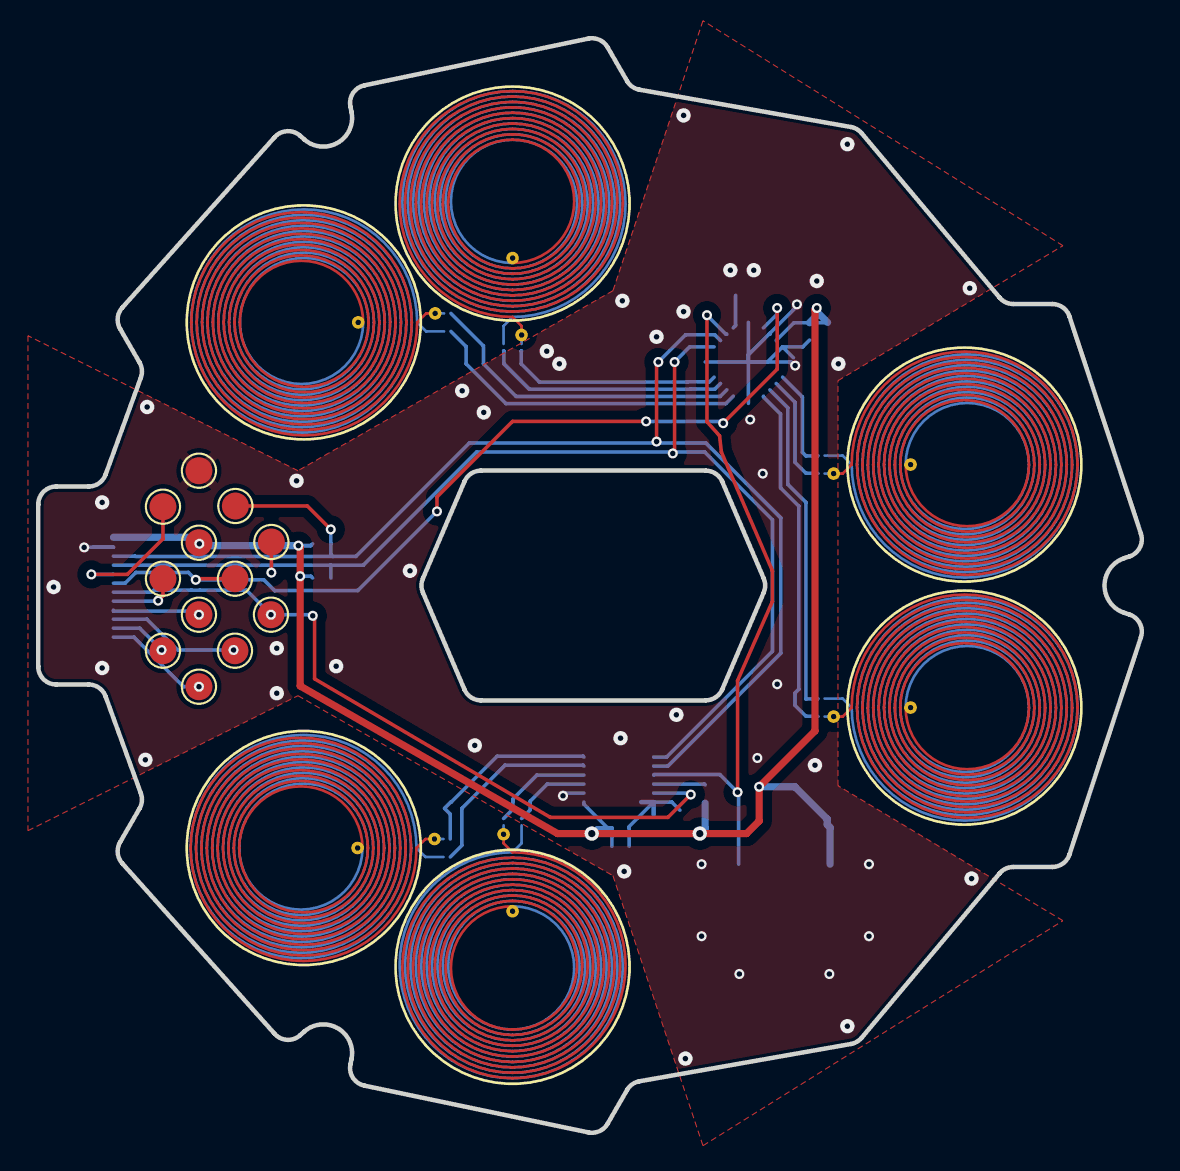
[picture p62: board PMK_SpaceMouse_01.kicad_pcb from above]

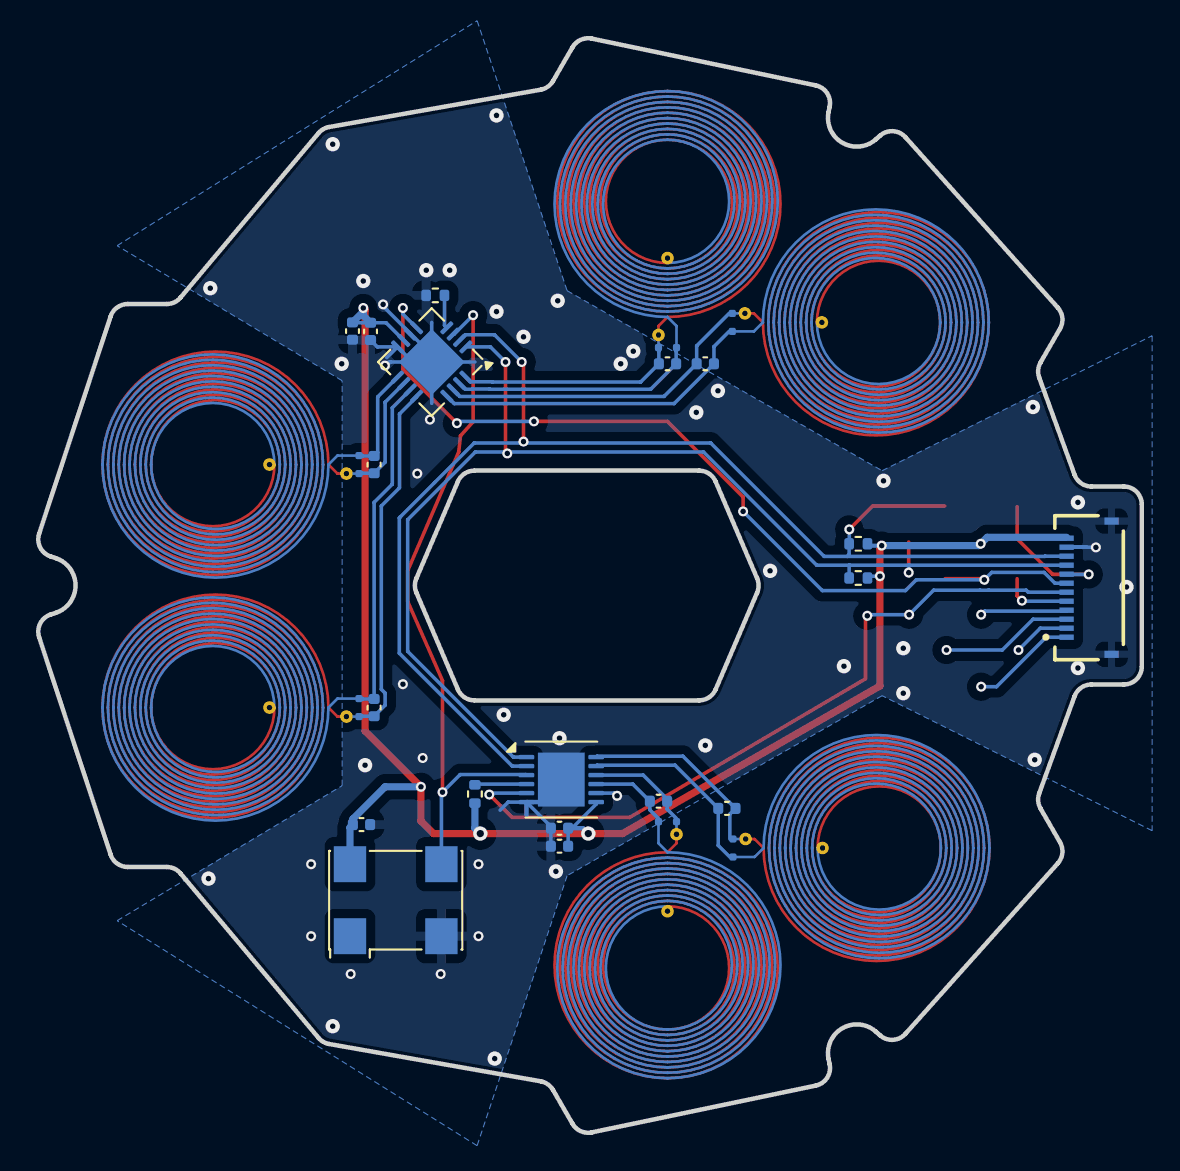
[picture p63: board PMK_SpaceMouse_01.kicad_pcb from below]

Board: 2 copper layers, 61.3 x 60.8 mm, 37 parts (25 on the bottom side), 27 nets.
