PumaFPV/PMK/Hardware/PMK_Keyboard/PMK_Keyboard_HW03/PMK_Keyboard_HW03.kicad_pcb

## KiCad design Hardware/PMK_Keyboard/PMK_Keyboard_HW03/PMK_Keyboard_HW03.kicad_pcb (2024-11-25)

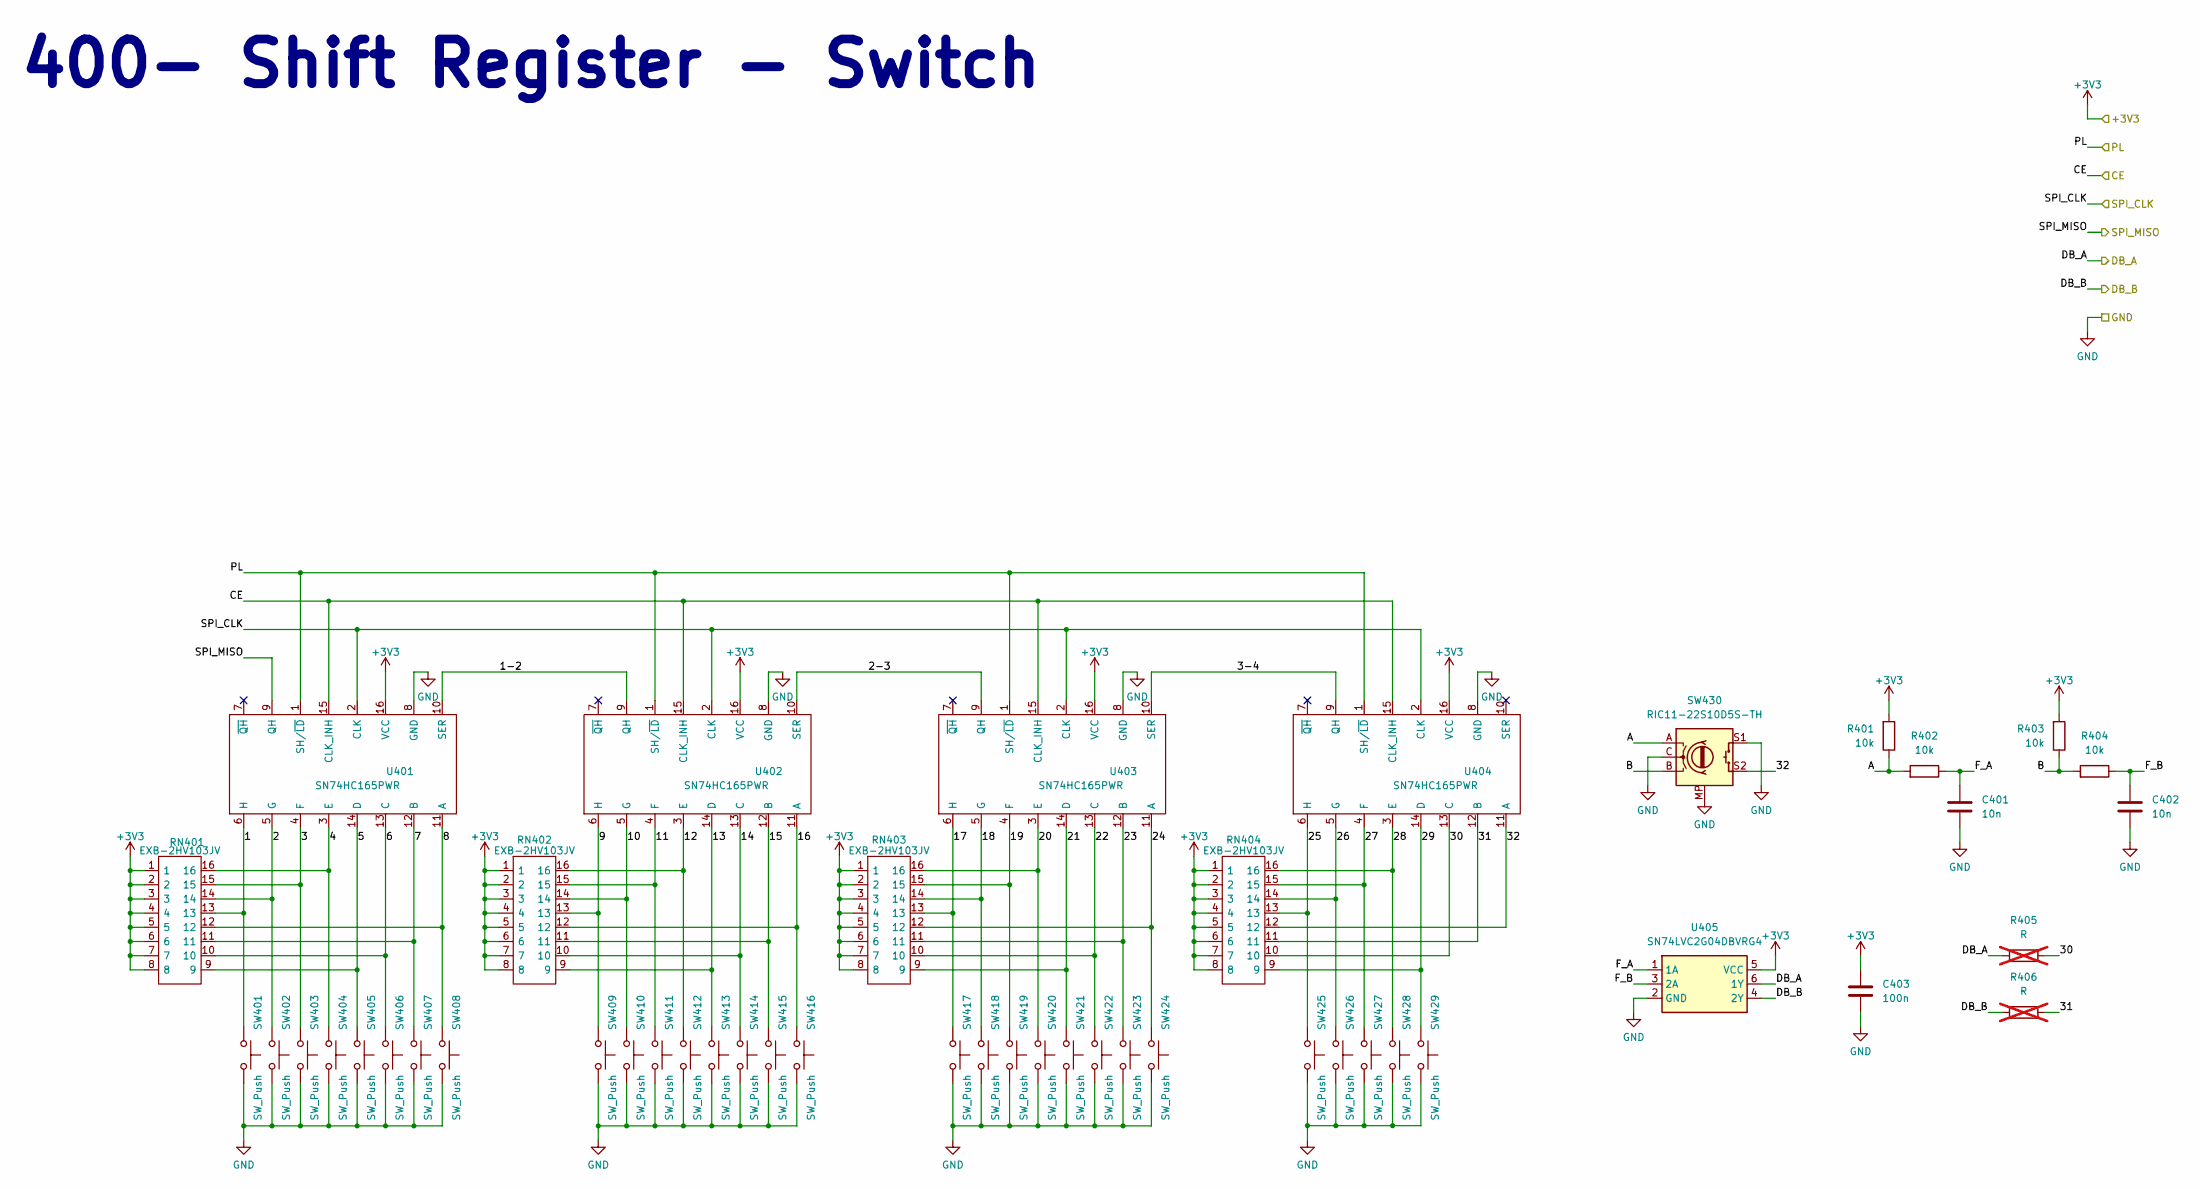
[picture p64: schematic ShiftRegisterSwitch.kicad_sch, PMK_Keyboard]

Parts:
C401, C402: 10n; C_0402_1005Metric
C403: 100n; C_0402_1005Metric
R401, R402, R403, R404: 10k; R_0201_0603Metric
R405, R406: R; R_0402_1005Metric; not fitted
RN401, RN402, RN403, RN404: EXB-2HV103JV; EXB2HV_1; Mouser Part Number 667-EXB-2HV103JV
SW401, SW402, SW403, SW404, SW405, SW406, SW407, SW408, SW409, SW410, SW411, SW412, SW413, SW414, SW415, SW416, SW417, SW418, SW419, SW420, SW421, SW422, SW423, SW424, SW425, SW426, SW427, SW428, SW429: SW_Push; Kailh_socket_PG1350_reversible_V1V2
SW430: RIC11-22S10D5S-TH
U401, U402, U403, U404: SN74HC165PWR; SOP65P640X120-16N; Mouser Part Number 595-SN74HC165PWR
U405: SN74LVC2G04DBVRG4; SOP95P280X145-6N; Mouser Part Number 595-74LVC2G04DBVRG4

Connections:
+3V3: C403.1, R401.2, R403.2, RN401.1, RN401.2, RN401.3, RN401.4, RN401.5, RN401.6, RN401.7, RN401.8, RN402.1, RN402.2, RN402.3, RN402.4, RN402.5, RN402.6, RN402.7, RN402.8, RN403.1, RN403.2, RN403.3, RN403.4, RN403.5, RN403.6, RN403.7, RN403.8, RN404.1, RN404.2, RN404.3, RN404.4, RN404.5, RN404.6, RN404.7, RN404.8, U401.16 (VCC), U402.16 (VCC), U403.16 (VCC), U404.16 (VCC), U405.5 (VCC); also elsewhere on the board
/200- PSoM/DB_A: R405.1, U405.6 (1Y); also elsewhere on the board
/200- PSoM/DB_B: R406.1, U405.4 (2Y); also elsewhere on the board
/200- PSoM/PL: U401.1 (SH/~LD), U402.1 (SH/~LD), U403.1 (SH/~LD), U404.1 (SH/~LD); also elsewhere on the board
/200- PSoM/SPI_CLK: U401.2 (CLK), U402.2 (CLK), U403.2 (CLK), U404.2 (CLK); also elsewhere on the board
/200- PSoM/SPI_MISO: U401.9 (QH); also elsewhere on the board
/200- PSoM/SR_CE: U401.15 (CLK_INH), U402.15 (CLK_INH), U403.15 (CLK_INH), U404.15 (CLK_INH); also elsewhere on the board
/400- Shift Register - Switch/1: RN401.13, SW401.1, U401.6 (H)
/400- Shift Register - Switch/1-2: U401.10 (SER), U402.9 (QH)
/400- Shift Register - Switch/2: RN401.14, SW402.1, U401.5 (G)
/400- Shift Register - Switch/2-3: U402.10 (SER), U403.9 (QH)
/400- Shift Register - Switch/3: RN401.15, SW403.1, U401.4 (F)
/400- Shift Register - Switch/3-4: U403.10 (SER), U404.9 (QH)
/400- Shift Register - Switch/4: RN401.16, SW404.1, U401.3 (E)
/400- Shift Register - Switch/5: RN401.9, SW405.1, U401.14 (D)
/400- Shift Register - Switch/6: RN401.10, SW406.1, U401.13 (C)
/400- Shift Register - Switch/7: RN401.11, SW407.1, U401.12 (B)
/400- Shift Register - Switch/8: RN401.12, SW408.1, U401.11 (A)
/400- Shift Register - Switch/9: RN402.13, SW409.1, U402.6 (H)
/400- Shift Register - Switch/10: RN402.14, SW410.1, U402.5 (G)
/400- Shift Register - Switch/11: RN402.15, SW411.1, U402.4 (F)
/400- Shift Register - Switch/12: RN402.16, SW412.1, U402.3 (E)
/400- Shift Register - Switch/13: RN402.9, SW413.1, U402.14 (D)
/400- Shift Register - Switch/14: RN402.10, SW414.1, U402.13 (C)
/400- Shift Register - Switch/15: RN402.11, SW415.1, U402.12 (B)
/400- Shift Register - Switch/16: RN402.12, SW416.1, U402.11 (A)
/400- Shift Register - Switch/17: RN403.13, SW417.1, U403.6 (H)
/400- Shift Register - Switch/18: RN403.14, SW418.1, U403.5 (G)
/400- Shift Register - Switch/19: RN403.15, SW419.1, U403.4 (F)
/400- Shift Register - Switch/20: RN403.16, SW420.1, U403.3 (E)
/400- Shift Register - Switch/21: RN403.9, SW421.1, U403.14 (D)
/400- Shift Register - Switch/22: RN403.10, SW422.1, U403.13 (C)
/400- Shift Register - Switch/23: RN403.11, SW423.1, U403.12 (B)
/400- Shift Register - Switch/24: RN403.12, SW424.1, U403.11 (A)
/400- Shift Register - Switch/25: RN404.13, SW425.1, U404.6 (H)
/400- Shift Register - Switch/26: RN404.14, SW426.1, U404.5 (G)
/400- Shift Register - Switch/27: RN404.15, SW427.1, U404.4 (F)
/400- Shift Register - Switch/28: RN404.16, SW428.1, U404.3 (E)
/400- Shift Register - Switch/29: RN404.9, SW429.1, U404.14 (D)
/400- Shift Register - Switch/30: R405.2, RN404.10, U404.13 (C)
/400- Shift Register - Switch/31: R406.2, RN404.11, U404.12 (B)
/400- Shift Register - Switch/32: RN404.12, SW430.S2, U404.11 (A)
/400- Shift Register - Switch/A: R401.1, R402.2, SW430.A
/400- Shift Register - Switch/B: R403.1, R404.2, SW430.B
/400- Shift Register - Switch/F_A: C401.1, R402.1, U405.1 (1A)
/400- Shift Register - Switch/F_B: C402.1, R404.1, U405.3 (2A)
GND: C401.2, C402.2, C403.2, SW401.2, SW402.2, SW403.2, SW404.2, SW405.2, SW406.2, SW407.2, SW408.2, SW409.2, SW410.2, SW411.2, SW412.2, SW413.2, SW414.2, SW415.2, SW416.2, SW417.2, SW418.2, SW419.2, SW420.2, SW421.2, SW422.2, SW423.2, SW424.2, SW425.2, SW426.2, SW427.2, SW428.2, SW429.2, SW430.C, SW430.MP, SW430.S1, U401.8 (GND), U402.8 (GND), U403.8 (GND), U404.8 (GND), U405.2 (GND); also elsewhere on the board

Notes on the sheet:
400- Shift Register - Switch

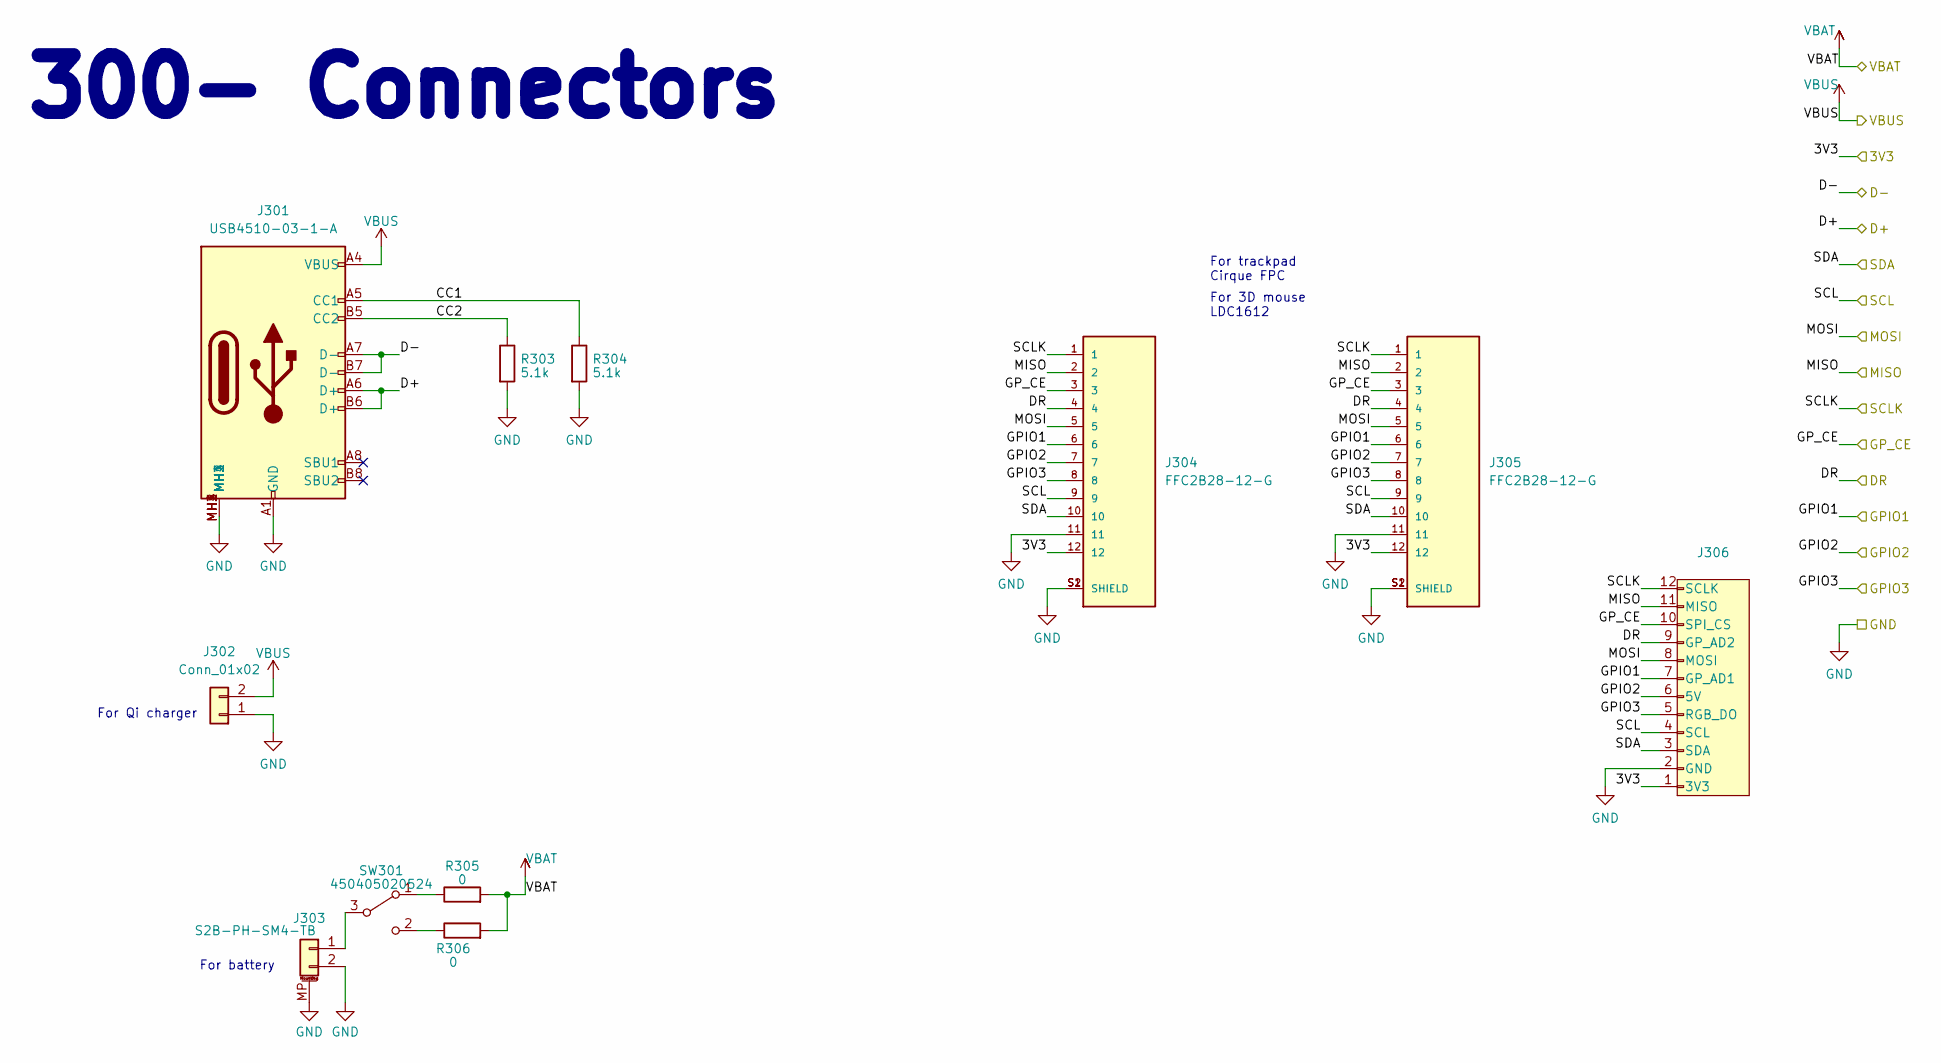
[picture p65: schematic Connectors.kicad_sch, PMK_Keyboard]

Parts:
J301: USB4510-03-1-A; USB4510031A; Mouser Part Number 640-USB4510031A
J302: Conn_01x02; PinHeader_1x02_P2.54mm_Vertical
J303: S2B-PH-SM4-TB; JST_PH_S2B-PH-SM4-TB_1x02-1MP_P2.00mm_Horizontal_DUALSIDE
J304, J305: FFC2B28-12-G; GCT_FFC2B28-12-G; PARTREV A; DigiKey_Part_Number 2073-FFC2B28-12-GTR-ND
J306: vik-keyboard-connector-horizontal
R303, R304: 5.1k; R_0402_1005Metric
R305, R306: 0; R_0402_1005Metric
SW301: 450405020524; 450405020524_DUALSIDE

Connections:
+3V3: J304.12, J305.12, J306.1 (3V3); also elsewhere on the board
/200- PSoM/D+: J301.A6 (D+), J301.B6 (D+); also elsewhere on the board
/200- PSoM/D-: J301.A7 (D-), J301.B7 (D-); also elsewhere on the board
/200- PSoM/DR: J304.4, J305.4, J306.9 (GP_AD2); also elsewhere on the board
/200- PSoM/GPIO1: J304.6, J305.6, J306.7 (GP_AD1); also elsewhere on the board
/200- PSoM/GPIO2: J304.7, J305.7, J306.6 (5V); also elsewhere on the board
/200- PSoM/GPIO3: J304.8, J305.8, J306.5 (RGB_DO); also elsewhere on the board
/200- PSoM/GP_CE: J304.3, J305.3, J306.10 (SPI_CS); also elsewhere on the board
/200- PSoM/SCL: J304.9, J305.9, J306.4 (SCL); also elsewhere on the board
/200- PSoM/SDA: J304.10, J305.10, J306.3 (SDA); also elsewhere on the board
/200- PSoM/SPI_CLK: J304.1, J305.1, J306.12 (SCLK); also elsewhere on the board
/200- PSoM/SPI_MISO: J304.2, J305.2, J306.11 (MISO); also elsewhere on the board
/200- PSoM/SPI_MOSI: J304.5, J305.5, J306.8 (MOSI); also elsewhere on the board
/300- Connectors/CC1: J301.A5 (CC1), R304.1
/300- Connectors/CC2: J301.B5 (CC2), R303.1
/VBAT: R305.2, R306.2; also elsewhere on the board
GND: J301.A1 (GND), J301.A12 (GND), J301.B1 (GND), J301.B12 (GND), J301.MH1, J301.MH2, J301.MH3, J301.MH4, J302.1, J303.2, J303.MP (MountPin), J304.11, J304.S1 (SHIELD), J304.S2 (SHIELD), J305.11, J305.S1 (SHIELD), J305.S2 (SHIELD), J306.2 (GND), R303.2, R304.2; also elsewhere on the board
unnamed: J303.1, SW301.3 (B)
unnamed: R305.1, SW301.1 (A)
unnamed: R306.1, SW301.2 (C)
VBUS: J301.A4 (VBUS), J301.A9 (VBUS), J301.B4 (VBUS), J301.B9 (VBUS), J302.2; also elsewhere on the board

Notes on the sheet:
300- Connectors
For battery
For trackpad Cirque FPC
For Qi charger
For 3D mouse LDC1612
