PumaFPV/PMK/Hardware/PMK_Keyboard/PMK_Keyboard_HW03/PMK_Keyboard_HW03.kicad_pcb

## KiCad design Hardware/PMK_Keyboard/PMK_Keyboard_HW03/PMK_Keyboard_HW03.kicad_pcb (continued)

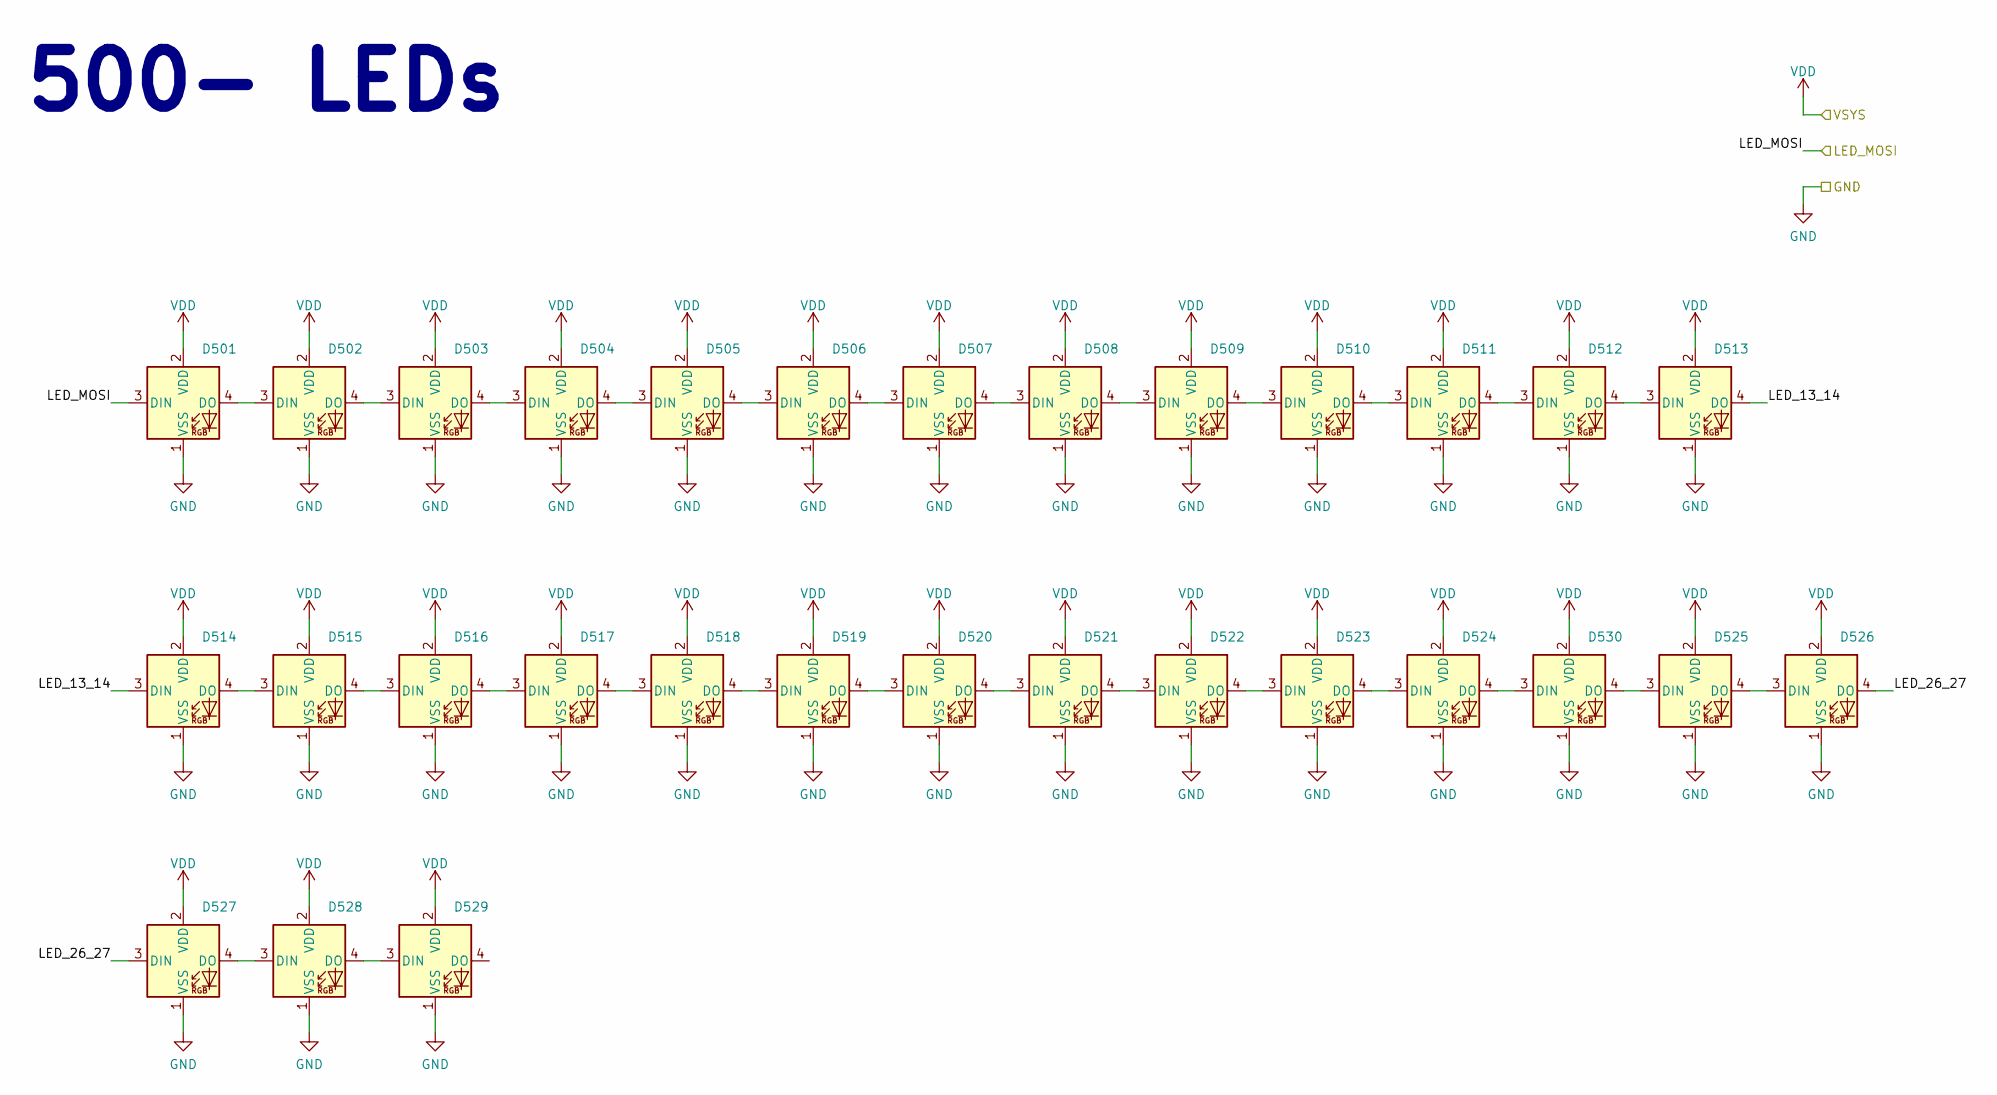
[picture p66: schematic LEDs.kicad_sch, PMK_Keyboard]

Parts:
D501, D502, D503, D504, D505, D506, D507, D508, D509, D510, D511, D512, D513, D514, D515, D516, D517, D518, D519, D520, D521, D522, D523, D524, D525, D526, D527, D528, D529, D530: YF923_2020_WS2812_LED; YF923_2020_WS2812_LED_DUALSIDE

Connections:
/200- PSoM/LED_MOSI: D501.3 (DIN); also elsewhere on the board
/500- LEDs/LED_13_14: D513.4 (DO), D514.3 (DIN)
/500- LEDs/LED_26_27: D526.4 (DO), D527.3 (DIN)
GND: D501.1 (VSS), D502.1 (VSS), D503.1 (VSS), D504.1 (VSS), D505.1 (VSS), D506.1 (VSS), D507.1 (VSS), D508.1 (VSS), D509.1 (VSS), D510.1 (VSS), D511.1 (VSS), D512.1 (VSS), D513.1 (VSS), D514.1 (VSS), D515.1 (VSS), D516.1 (VSS), D517.1 (VSS), D518.1 (VSS), D519.1 (VSS), D520.1 (VSS), D521.1 (VSS), D522.1 (VSS), D523.1 (VSS), D524.1 (VSS), D525.1 (VSS), D526.1 (VSS), D527.1 (VSS), D528.1 (VSS), D529.1 (VSS), D530.1 (VSS); also elsewhere on the board
unnamed: D501.4 (DO), D502.3 (DIN)
unnamed: D502.4 (DO), D503.3 (DIN)
unnamed: D503.4 (DO), D504.3 (DIN)
unnamed: D504.4 (DO), D505.3 (DIN)
unnamed: D505.4 (DO), D506.3 (DIN)
unnamed: D506.4 (DO), D507.3 (DIN)
unnamed: D507.4 (DO), D508.3 (DIN)
unnamed: D508.4 (DO), D509.3 (DIN)
unnamed: D509.4 (DO), D510.3 (DIN)
unnamed: D510.4 (DO), D511.3 (DIN)
unnamed: D511.4 (DO), D512.3 (DIN)
unnamed: D512.4 (DO), D513.3 (DIN)
unnamed: D514.4 (DO), D515.3 (DIN)
unnamed: D515.4 (DO), D516.3 (DIN)
unnamed: D516.4 (DO), D517.3 (DIN)
unnamed: D517.4 (DO), D518.3 (DIN)
unnamed: D518.4 (DO), D519.3 (DIN)
unnamed: D519.4 (DO), D520.3 (DIN)
unnamed: D520.4 (DO), D521.3 (DIN)
unnamed: D521.4 (DO), D522.3 (DIN)
unnamed: D522.4 (DO), D523.3 (DIN)
unnamed: D523.4 (DO), D524.3 (DIN)
unnamed: D524.4 (DO), D530.3 (DIN)
unnamed: D525.3 (DIN), D530.4 (DO)
unnamed: D525.4 (DO), D526.3 (DIN)
unnamed: D527.4 (DO), D528.3 (DIN)
unnamed: D528.4 (DO), D529.3 (DIN)
VDD: D501.2 (VDD), D502.2 (VDD), D503.2 (VDD), D504.2 (VDD), D505.2 (VDD), D506.2 (VDD), D507.2 (VDD), D508.2 (VDD), D509.2 (VDD), D510.2 (VDD), D511.2 (VDD), D512.2 (VDD), D513.2 (VDD), D514.2 (VDD), D515.2 (VDD), D516.2 (VDD), D517.2 (VDD), D518.2 (VDD), D519.2 (VDD), D520.2 (VDD), D521.2 (VDD), D522.2 (VDD), D523.2 (VDD), D524.2 (VDD), D525.2 (VDD), D526.2 (VDD), D527.2 (VDD), D528.2 (VDD), D529.2 (VDD), D530.2 (VDD); also elsewhere on the board

Notes on the sheet:
500- LEDs

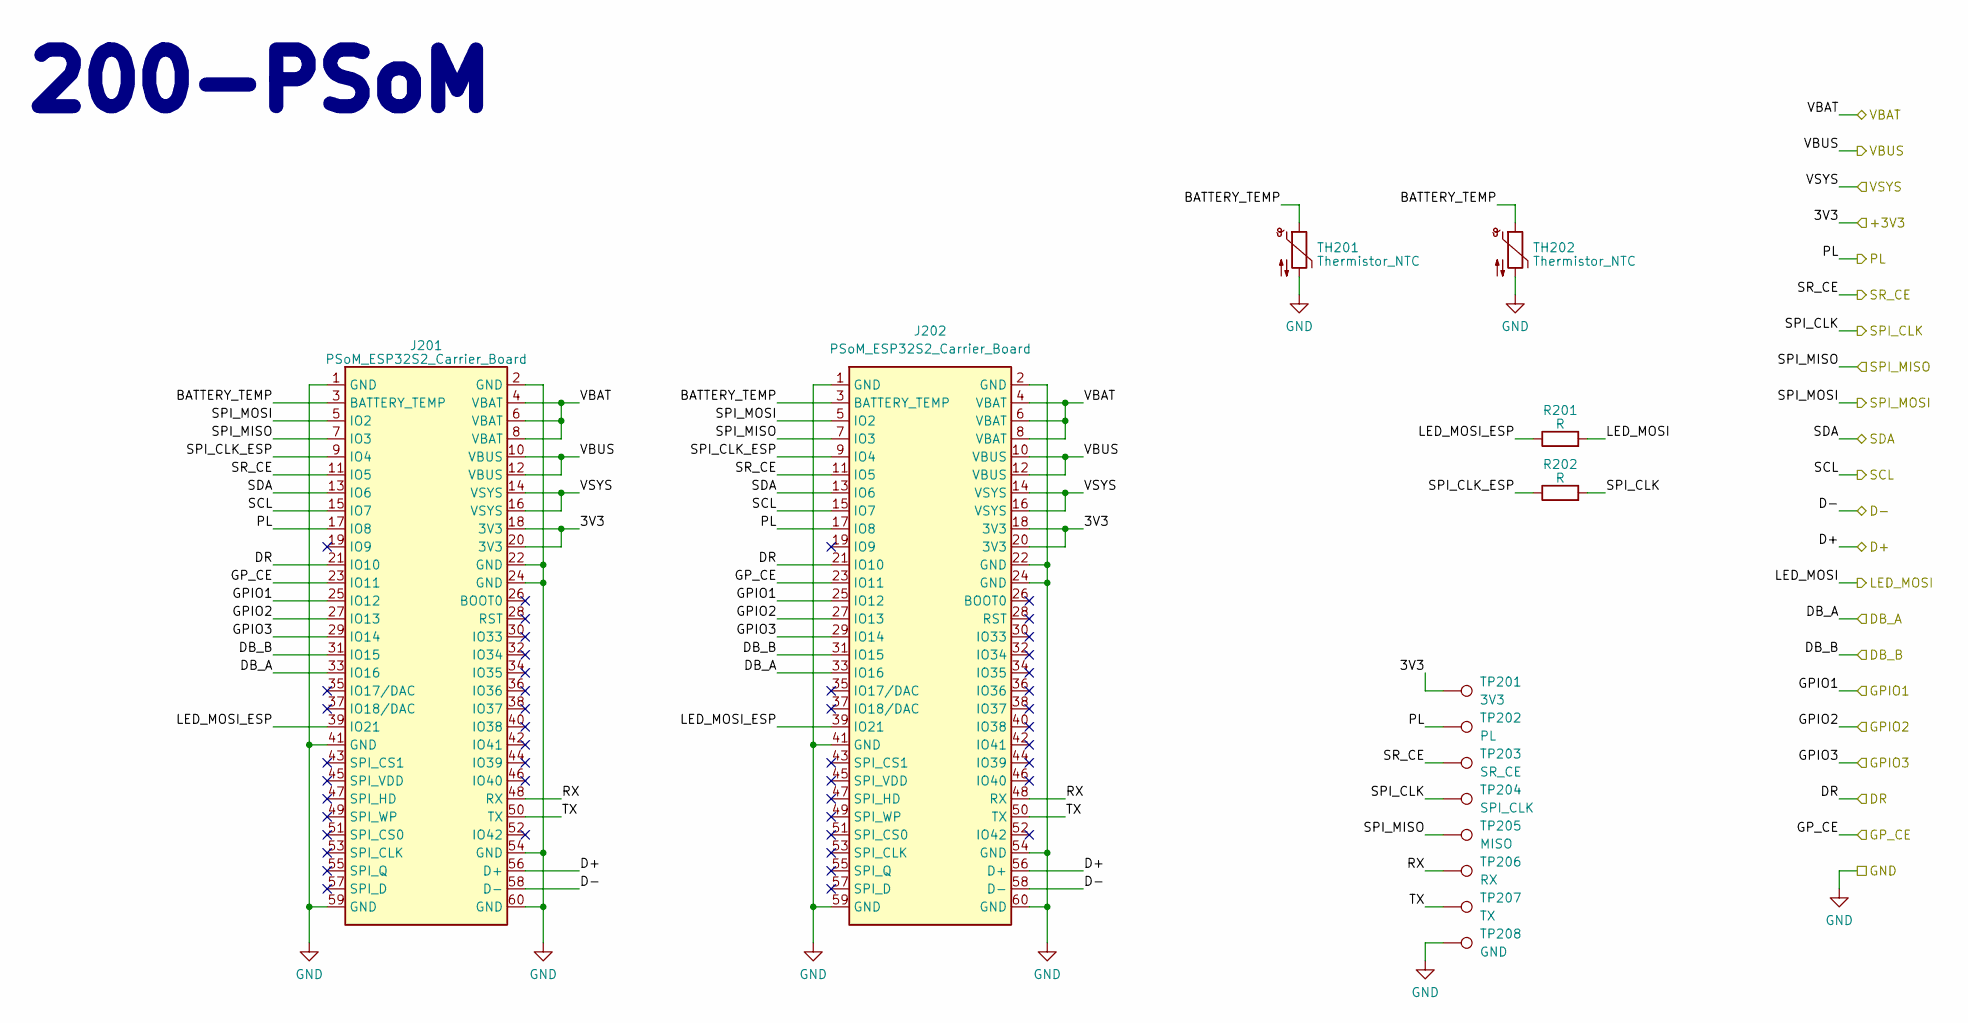
[picture p67: schematic PSoM.kicad_sch, PMK_Keyboard]

Parts:
J201, J202: PSoM_ESP32S2_Carrier_Board; PSoM_ESP32S2_00
R201, R202: R; R_0402_1005Metric
TH201, TH202: Thermistor_NTC; R_0402_1005Metric
TP201: 3V3; TestPoint_Pad_D1.5mm
TP202: PL; TestPoint_Pad_D1.5mm
TP203: SR_CE; TestPoint_Pad_D1.5mm
TP204: SPI_CLK; TestPoint_Pad_D1.5mm
TP205: MISO; TestPoint_Pad_D1.5mm
TP206: RX; TestPoint_Pad_D1.5mm
TP207: TX; TestPoint_Pad_D1.5mm
TP208: GND; TestPoint_Pad_D1.5mm

Connections:
+3V3: J201.18 (3V3), J201.20 (3V3), J202.18 (3V3), J202.20 (3V3), TP201.1; also elsewhere on the board
/200- PSoM/BATTERY_TEMP: J201.3 (BATTERY_TEMP), J202.3 (BATTERY_TEMP), TH201.1, TH202.1
/200- PSoM/D+: J201.56 (D+), J202.56 (D+); also elsewhere on the board
/200- PSoM/D-: J201.58 (D-), J202.58 (D-); also elsewhere on the board
/200- PSoM/DB_A: J201.33 (IO16), J202.33 (IO16); also elsewhere on the board
/200- PSoM/DB_B: J201.31 (IO15), J202.31 (IO15); also elsewhere on the board
/200- PSoM/DR: J201.21 (IO10), J202.21 (IO10); also elsewhere on the board
/200- PSoM/GPIO1: J201.25 (IO12), J202.25 (IO12); also elsewhere on the board
/200- PSoM/GPIO2: J201.27 (IO13), J202.27 (IO13); also elsewhere on the board
/200- PSoM/GPIO3: J201.29 (IO14), J202.29 (IO14); also elsewhere on the board
/200- PSoM/GP_CE: J201.23 (IO11), J202.23 (IO11); also elsewhere on the board
/200- PSoM/LED_MOSI: R201.2; also elsewhere on the board
/200- PSoM/LED_MOSI_ESP: J201.39 (IO21), J202.39 (IO21), R201.1
/200- PSoM/PL: J201.17 (IO8), J202.17 (IO8), TP202.1; also elsewhere on the board
/200- PSoM/RX: J201.48 (RX), J202.48 (RX), TP206.1
/200- PSoM/SCL: J201.15 (IO7), J202.15 (IO7); also elsewhere on the board
/200- PSoM/SDA: J201.13 (IO6), J202.13 (IO6); also elsewhere on the board
/200- PSoM/SPI_CLK: R202.2, TP204.1; also elsewhere on the board
/200- PSoM/SPI_CLK_ESP: J201.9 (IO4), J202.9 (IO4), R202.1
/200- PSoM/SPI_MISO: J201.7 (IO3), J202.7 (IO3), TP205.1; also elsewhere on the board
/200- PSoM/SPI_MOSI: J201.5 (IO2), J202.5 (IO2); also elsewhere on the board
/200- PSoM/SR_CE: J201.11 (IO5), J202.11 (IO5), TP203.1; also elsewhere on the board
/200- PSoM/TX: J201.50 (TX), J202.50 (TX), TP207.1
/VBAT: J201.4 (VBAT), J201.6 (VBAT), J201.8 (VBAT), J202.4 (VBAT), J202.6 (VBAT), J202.8 (VBAT); also elsewhere on the board
GND: J201.1 (GND), J201.2 (GND), J201.22 (GND), J201.24 (GND), J201.41 (GND), J201.54 (GND), J201.59 (GND), J201.60 (GND), J202.1 (GND), J202.2 (GND), J202.22 (GND), J202.24 (GND), J202.41 (GND), J202.54 (GND), J202.59 (GND), J202.60 (GND), TH201.2, TH202.2, TP208.1; also elsewhere on the board
VBUS: J201.10 (VBUS), J201.12 (VBUS), J202.10 (VBUS), J202.12 (VBUS); also elsewhere on the board
VDD: J201.14 (VSYS), J201.16 (VSYS), J202.14 (VSYS), J202.16 (VSYS); also elsewhere on the board

Notes on the sheet:
200-PSoM

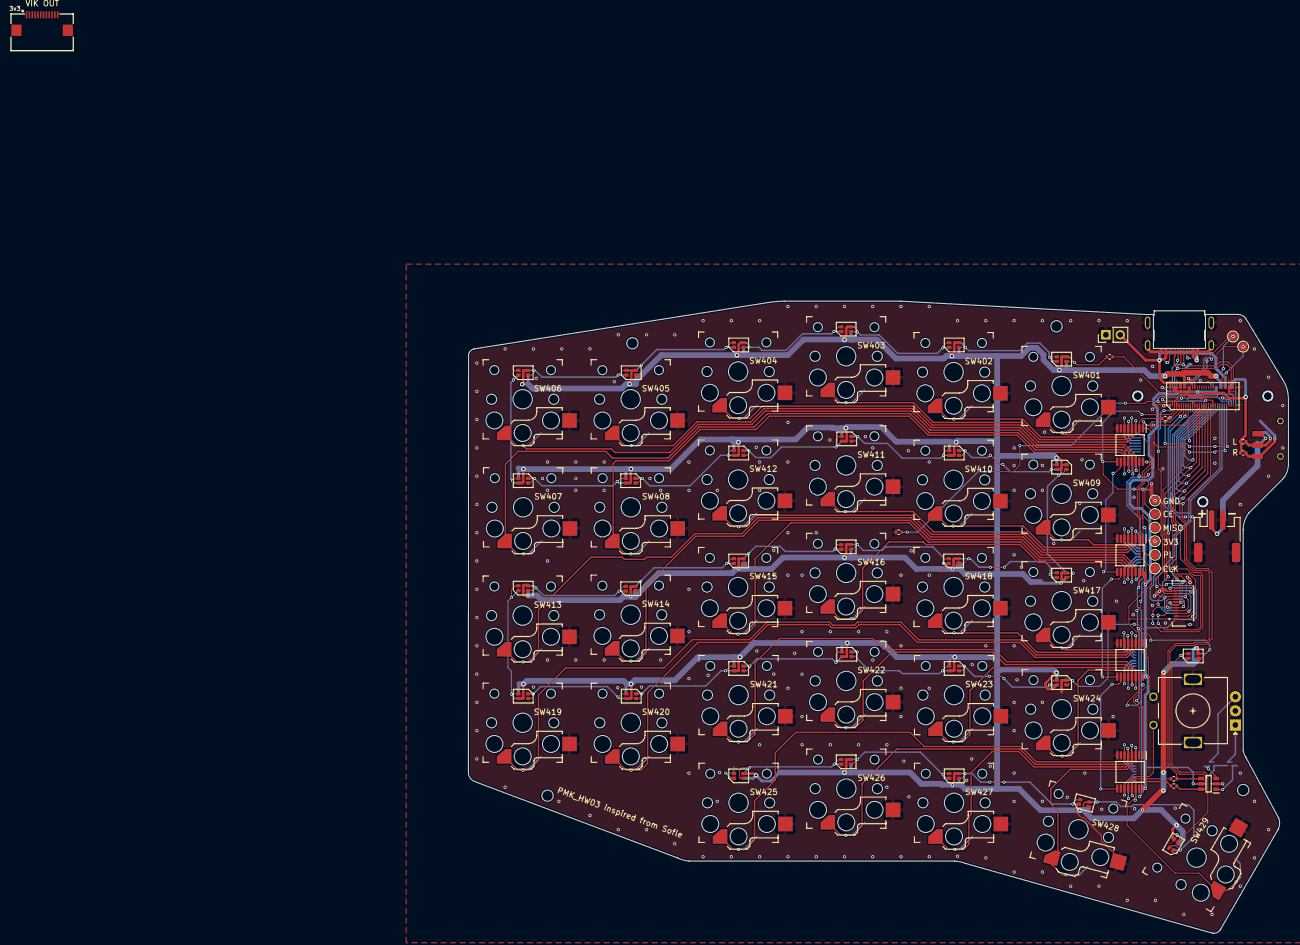
[picture p68: board PMK_Keyboard_HW03.kicad_pcb from above]

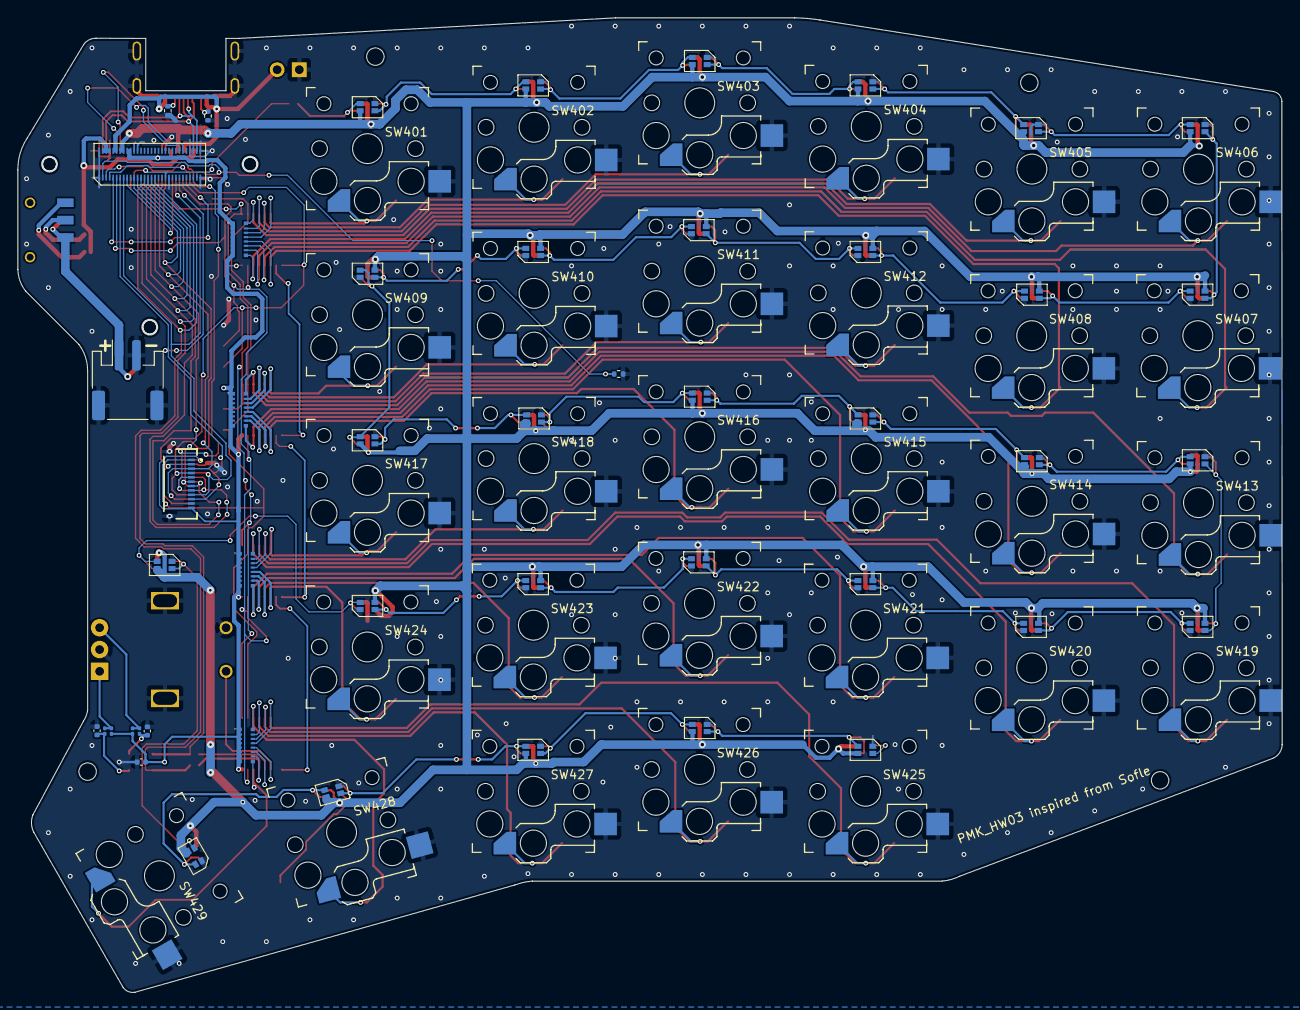
[picture p69: board PMK_Keyboard_HW03.kicad_pcb from below]

Board: 2 copper layers, 145.0 x 111.8 mm, 103 parts (17 on the bottom side), 100 nets.
