PumaFPV/PMK/Hardware/PMK_Dongle/PMK_Dongle_C_nRF_HW00/PMK_Dongle_C_nRF_HW00.kicad_pcb

## KiCad design Hardware/PMK_Dongle/PMK_Dongle_C_nRF_HW00/PMK_Dongle_C_nRF_HW00.kicad_pcb (2024-08-20)

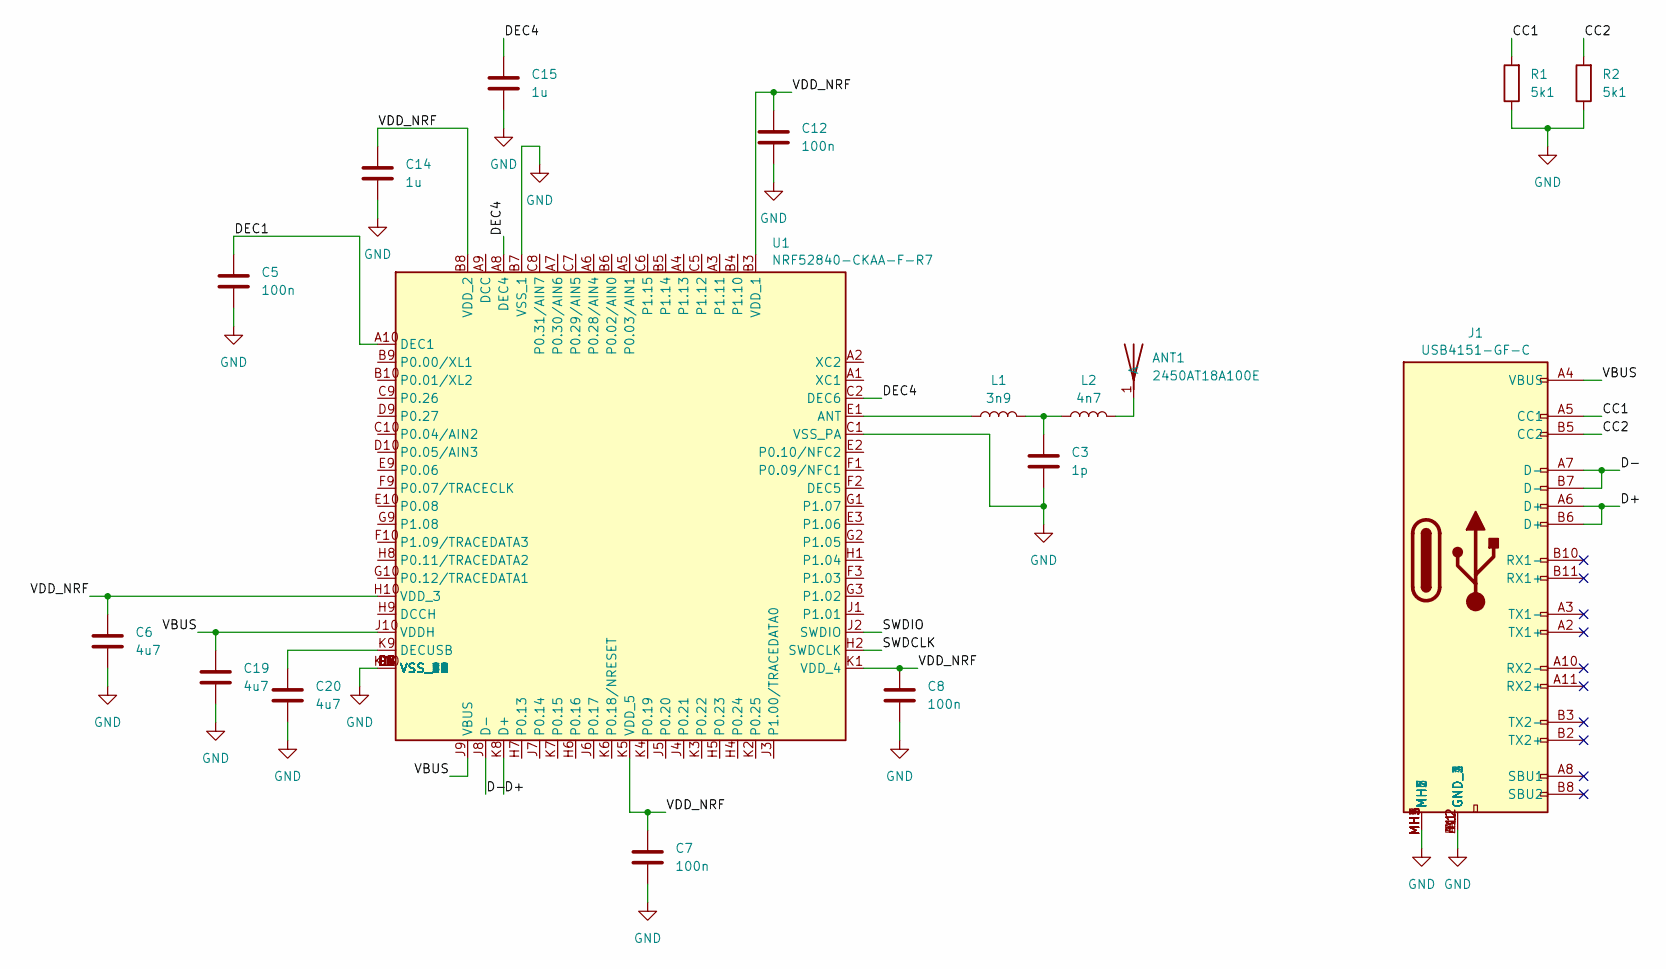
[picture p70: schematic PMK_Dongle_C_nRF_HW00.kicad_sch]

Parts:
ANT1: 2450AT18A100E; ANTC3216X140N; Mouser Part Number 609-2450AT18A100E
C3: 1p; C_0201_0603Metric
C5, C7, C8, C12: 100n; C_0201_0603Metric
C6, C19, C20: 4u7; C_0603_1608Metric
C14, C15: 1u; C_0402_1005Metric
J1: USB4151-GF-C; USB4151GFC; Mouser Part Number 640-USB4151-GF-C
L1: 3n9; L_0201_0603Metric
L2: 4n7; L_0201_0603Metric
R1, R2: 5k1; R_0201_0603Metric
U1: NRF52840-CKAA-F-R7; Mouser Part Number 949-NRF52840CKAAF-R7

Connections:
/CC1: J1.A5 (CC1), R1.2
/CC2: J1.B5 (CC2), R2.2
/D+: J1.A6 (D+), J1.B6 (D+), U1.K8 (D+)
/D-: J1.A7 (D-), J1.B7 (D-), U1.J8 (D-)
/DEC1: C5.1, U1.A10 (DEC1)
/DEC4: C15.1, U1.A8 (DEC4), U1.C2 (DEC6)
/SWDCLK: U1.H2 (SWDCLK)
/SWDIO: U1.J2 (SWDIO)
/VBUS: C19.1, J1.A4 (VBUS), J1.A9 (VBUS), J1.B4 (VBUS), J1.B9 (VBUS), U1.J9 (VBUS), U1.J10 (VDDH)
/VDD_NRF: C6.1, C7.1, C8.1, C12.1, C14.1, U1.B3 (VDD_1), U1.B8 (VDD_2), U1.H10 (VDD_3), U1.K1 (VDD_4), U1.K5 (VDD_5)
GND: C3.2, C5.2, C6.2, C7.2, C8.2, C12.2, C14.2, C15.2, C19.2, C20.2, J1.A1 (GND_1), J1.A12 (GND_2), J1.B1 (GND_3), J1.B12 (GND_4), J1.MH1, J1.MH2 (MH7), J1.MH3 (MH2), J1.MH4 (MH6), J1.MH5, R1.1, R2.1, U1.B7 (VSS_1), U1.C1 (VSS_PA), U1.C4 (VSS_2), U1.D3 (VSS_3), U1.D4 (VSS_4), U1.D5 (VSS_5), U1.D6 (VSS_6), U1.D7 (VSS_7), U1.D8 (VSS_8), U1.E4 (VSS_9), U1.E5 (VSS_10), U1.E6 (VSS_11), U1.E7 (VSS_12), U1.E8 (VSS_13), U1.F4 (VSS_14), U1.F5 (VSS_15), U1.F6 (VSS_16), U1.F7 (VSS_17), U1.F8 (VSS_18), U1.G4 (VSS_19), U1.G5 (VSS_20), U1.G6 (VSS_21), U1.G7 (VSS_22), U1.G8 (VSS_23), U1.K10 (VSS_24)
unnamed: ANT1.1 (A), L2.2
unnamed: C3.1, L1.2, L2.1
unnamed: L1.1, U1.E1 (ANT)
unnamed: C20.1, U1.K9 (DECUSB)

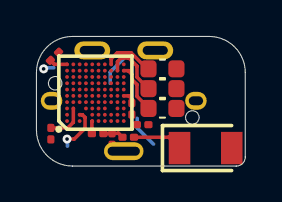
[picture p71: board PMK_Dongle_C_nRF_HW00.kicad_pcb from above]

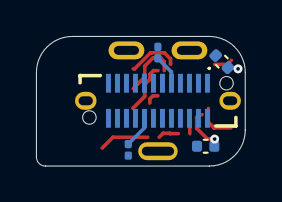
[picture p72: board PMK_Dongle_C_nRF_HW00.kicad_pcb from below]

Board: 6 copper layers, 11.6 x 7.2 mm, 17 parts (5 on the bottom side), 13 nets.
