PumaFPV/PMK/Hardware/PMK_Dongle/PMK_Dongle_S3_HW00/PMK_Dongle_S3_HW00.kicad_pcb

## KiCad design Hardware/PMK_Dongle/PMK_Dongle_S3_HW00/PMK_Dongle_S3_HW00.kicad_pcb (2024-08-18)

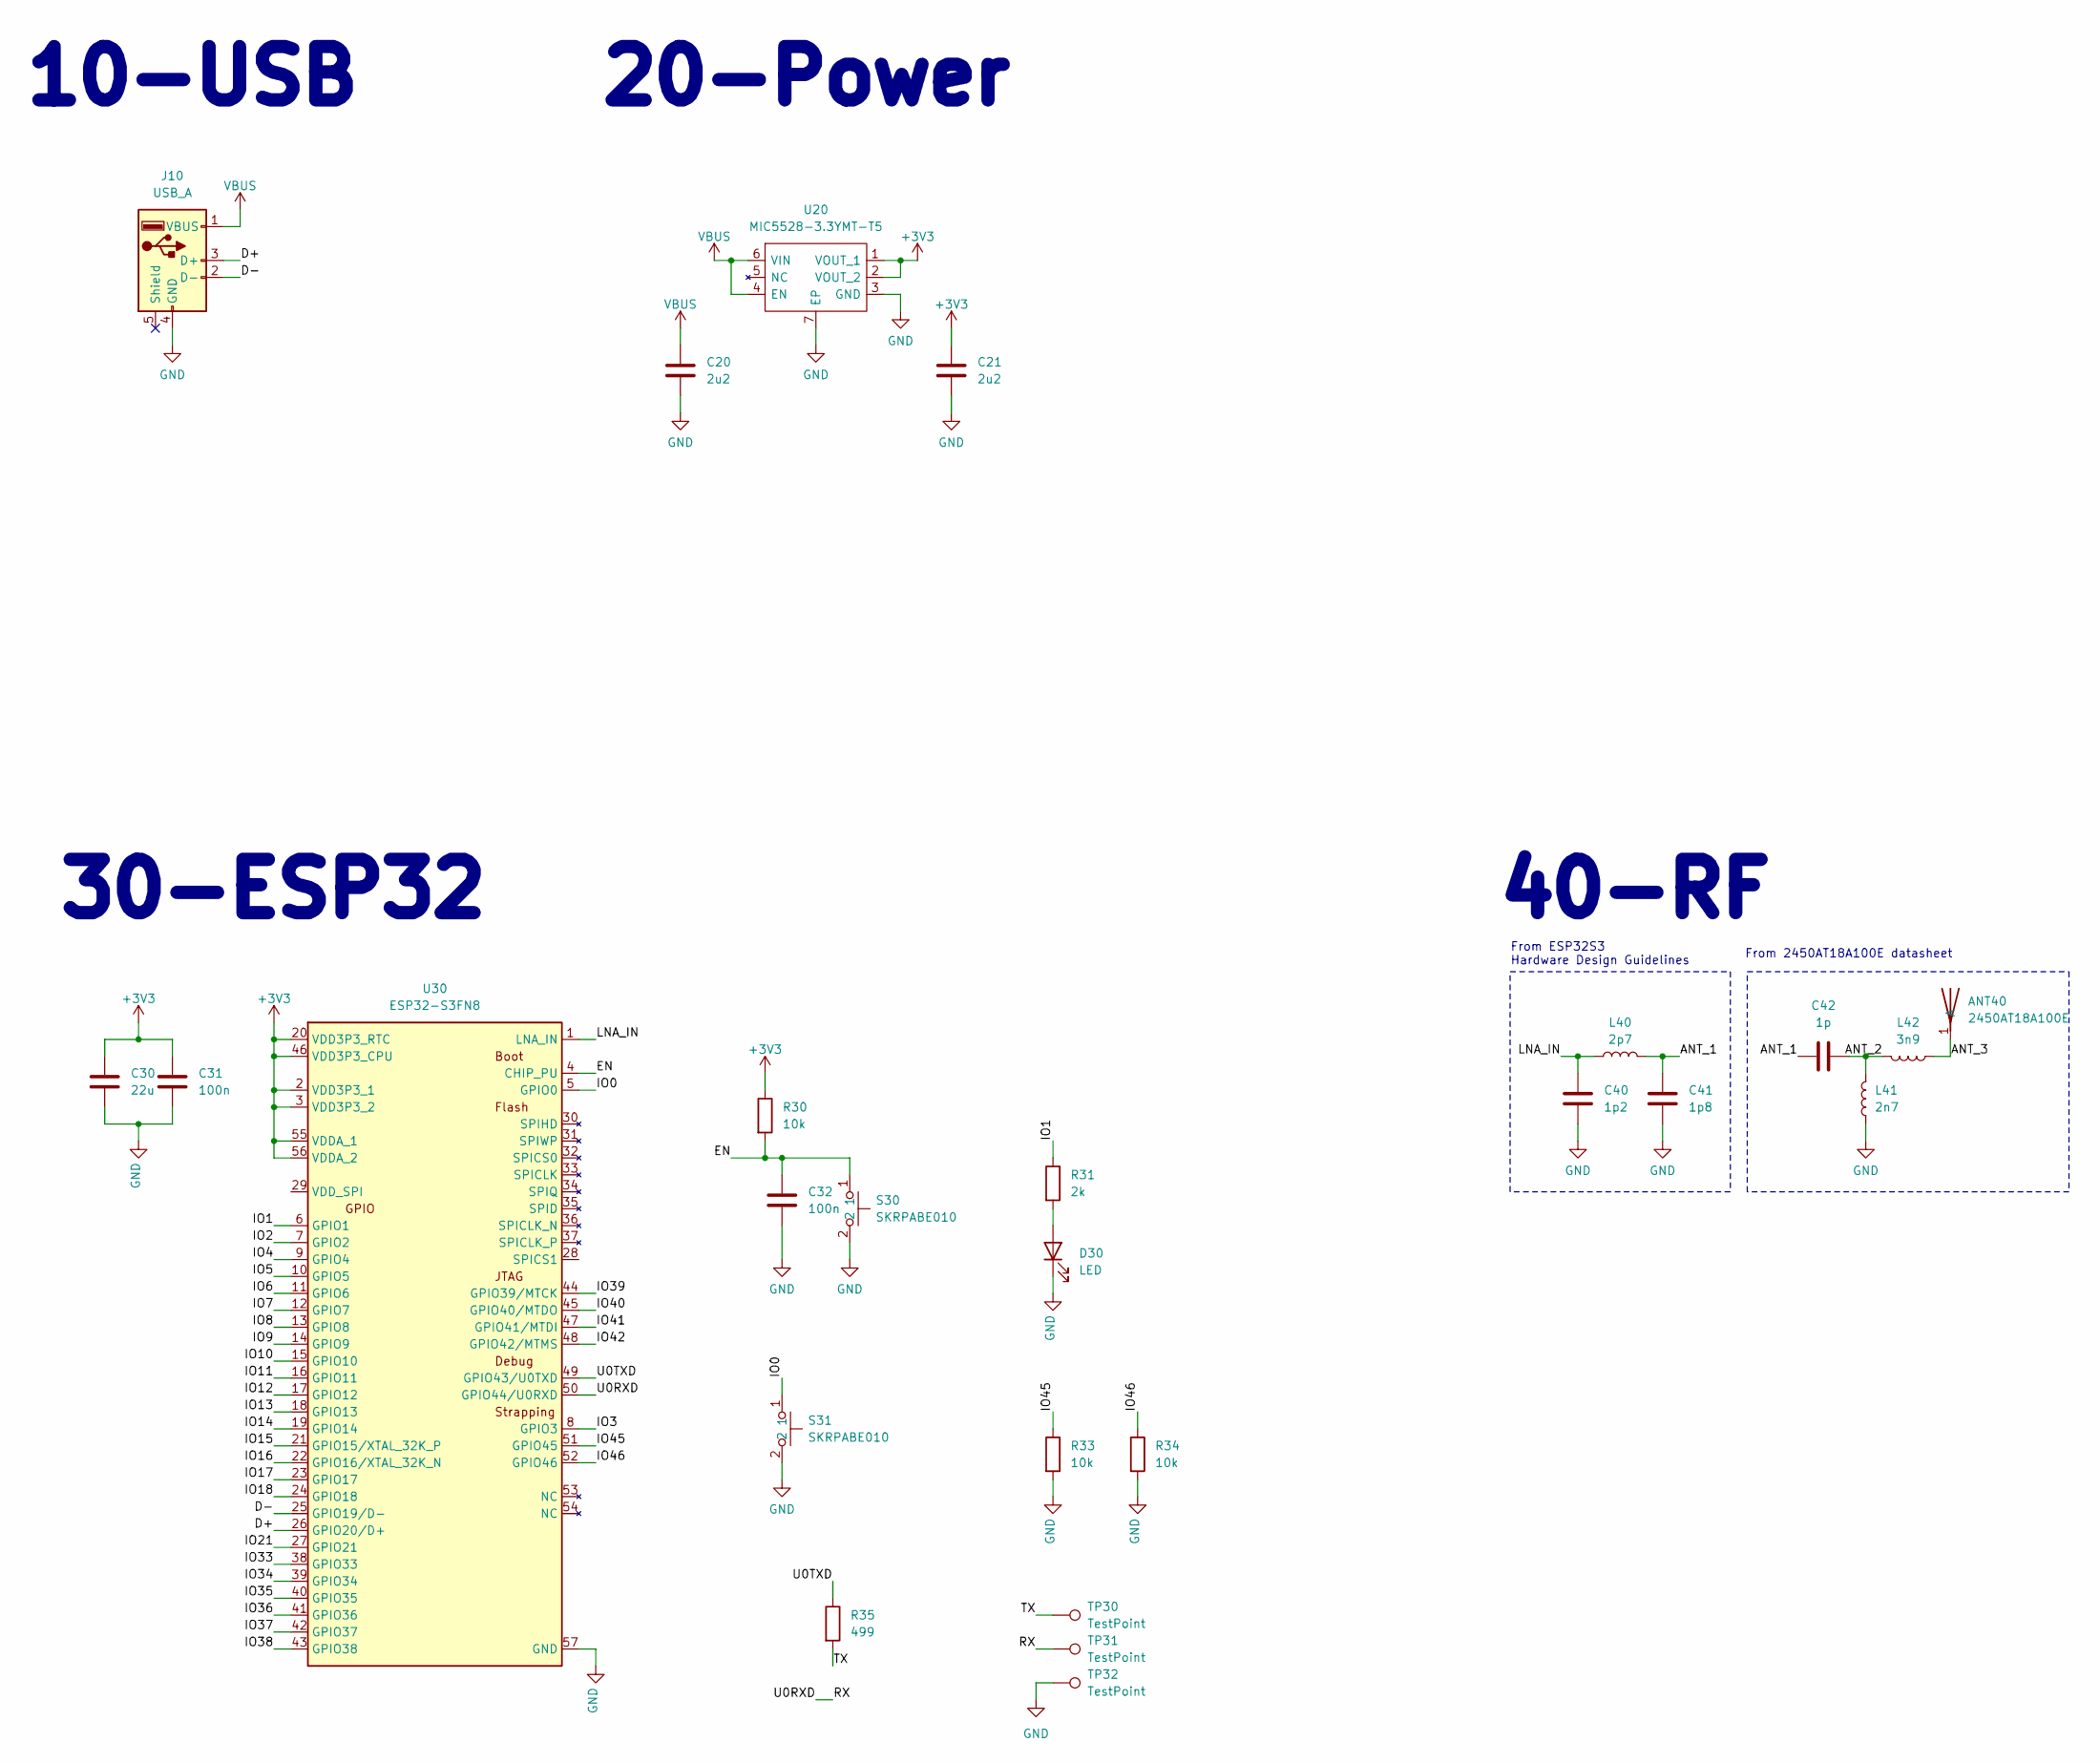
[picture p73: schematic PMK_Dongle_S3_HW00.kicad_sch, PMK_Dongle]

Parts:
ANT40: 2450AT18A100E; ANTC3216X140N; Mouser Part Number 609-2450AT18A100E
C20, C21: 2u2; C_0603_1608Metric
C30: 22u; C_0603_1608Metric
C31: 100n; C_0201_0603Metric
C32: 100n; C_0402_1005Metric
C40: 1p2; C_0201_0603Metric
C41: 1p8; C_0201_0603Metric
C42: 1p; C_0402_1005Metric
D30: LED; LED_0402_1005Metric
J10: USB_A; USB_PCB
L40: 2p7; L_0201_0603Metric
L41: 2n7; L_0402_1005Metric
L42: 3n9; L_0402_1005Metric
R30, R33, R34: 10k; R_0201_0603Metric
R31: 2k; R_0402_1005Metric
R35: 499; R_0402_1005Metric
S30, S31: SKRPABE010; B3U-1000P; Mouser Part Number 688-SKRPAB
TP30, TP31, TP32: TestPoint; TestPoint_0.8mm
U20: MIC5528-3.3YMT-T5; SON40P120X120X60-7N-D; Mouser Part Number 998-MIC5528-3.3YMTT5
U30: ESP32-S3FN8; ESP32-S3-PICO-1-N8R2; Mouser Part Number 356-ESP32-S3FN8

Connections:
+3V3: C21.1, C30.1, C31.1, R30.1, U20.1 (VOUT_1), U20.2 (VOUT_2), U30.2 (VDD3P3_1), U30.3 (VDD3P3_2), U30.20 (VDD3P3_RTC), U30.46 (VDD3P3_CPU), U30.55 (VDDA_1), U30.56 (VDDA_2)
/ANT_1: C41.1, C42.2, L40.1
/ANT_2: C42.1, L41.1, L42.1
/ANT_3: ANT40.1 (A), L42.2
/D+: J10.3 (D+), U30.26 (GPIO20/D+)
/D-: J10.2 (D-), U30.25 (GPIO19/D-)
/EN: C32.1, R30.2, S30.1, U30.4 (CHIP_PU)
/IO0: S31.1, U30.5 (GPIO0)
/IO1: R31.1, U30.6 (GPIO1)
/IO2: U30.7 (GPIO2)
/IO3: U30.8 (GPIO3)
/IO4: U30.9 (GPIO4)
/IO5: U30.10 (GPIO5)
/IO6: U30.11 (GPIO6)
/IO7: U30.12 (GPIO7)
/IO8: U30.13 (GPIO8)
/IO9: U30.14 (GPIO9)
/IO10: U30.15 (GPIO10)
/IO11: U30.16 (GPIO11)
/IO12: U30.17 (GPIO12)
/IO13: U30.18 (GPIO13)
/IO14: U30.19 (GPIO14)
/IO15: U30.21 (GPIO15/XTAL_32K_P)
/IO16: U30.22 (GPIO16/XTAL_32K_N)
/IO17: U30.23 (GPIO17)
/IO18: U30.24 (GPIO18)
/IO21: U30.27 (GPIO21)
/IO33: U30.38 (GPIO33)
/IO34: U30.39 (GPIO34)
/IO35: U30.40 (GPIO35)
/IO36: U30.41 (GPIO36)
/IO37: U30.42 (GPIO37)
/IO38: U30.43 (GPIO38)
/IO39: U30.44 (GPIO39/MTCK)
/IO40: U30.45 (GPIO40/MTDO)
/IO41: U30.47 (GPIO41/MTDI)
/IO42: U30.48 (GPIO42/MTMS)
/IO45: R33.1, U30.51 (GPIO45)
/IO46: R34.1, U30.52 (GPIO46)
/LNA_IN: C40.1, L40.2, U30.1 (LNA_IN)
/RX: TP31.1, U30.50 (GPIO44/U0RXD)
/TX: R35.2, TP30.1
/U0TXD: R35.1, U30.49 (GPIO43/U0TXD)
GND: C20.2, C21.2, C30.2, C31.2, C32.2, C40.2, C41.2, D30.1 (K), J10.4 (GND), L41.2, R33.2, R34.2, S30.2, S31.2, TP32.1, U20.3 (GND), U20.7 (EP), U30.57 (GND)
unnamed: D30.2 (A), R31.2
VBUS: C20.1, J10.1 (VBUS), U20.4 (EN), U20.6 (VIN)

Notes on the sheet:
From 2450AT18A100E datasheet
40-RF
10-USB
30-ESP32
From ESP32S3 Hardware Design Guidelines
20-Power

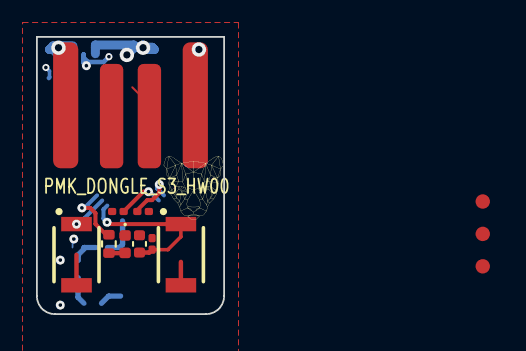
[picture p74: board PMK_Dongle_S3_HW00.kicad_pcb from above]

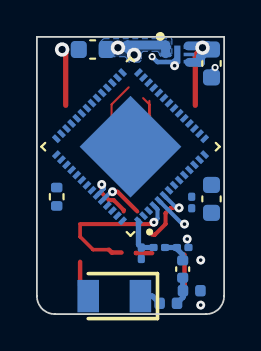
[picture p75: board PMK_Dongle_S3_HW00.kicad_pcb from below]

Board: 4 copper layers, 10.4 x 15.4 mm, 26 parts (14 on the bottom side), 18 nets.
