PumaFPV/PMK/Hardware/PMK_Keyboard/PMK_Keyboard_HW01/PMK_Keyboard_HW01.kicad_pcb

## KiCad design Hardware/PMK_Keyboard/PMK_Keyboard_HW01/PMK_Keyboard_HW01.kicad_pcb (2024-02-12)

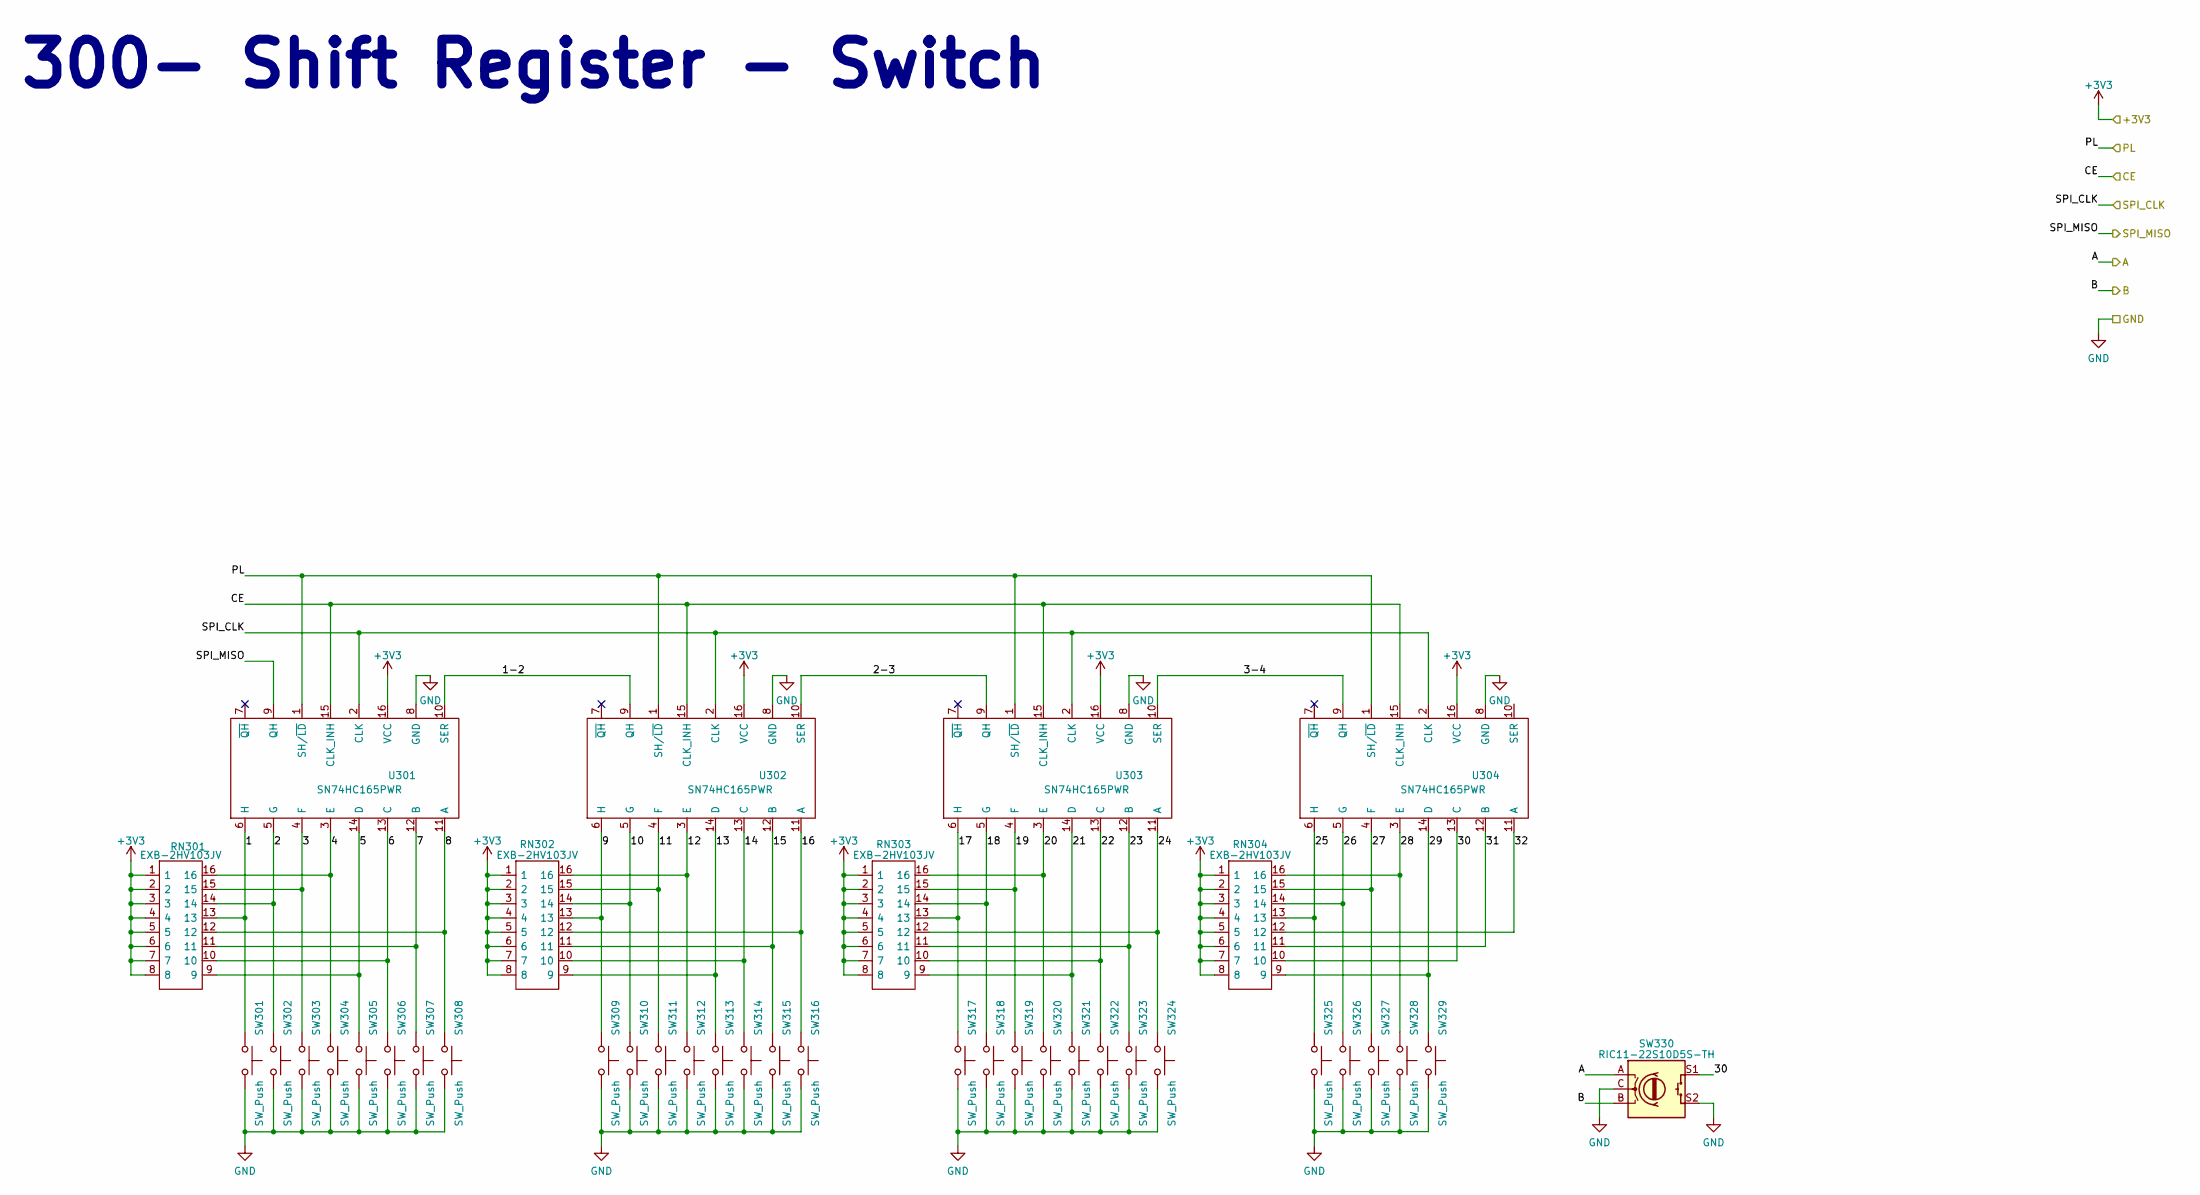
[picture p76: schematic ShiftRegisterSwitch.kicad_sch, PMK_Keyboard]

Parts:
RN301, RN302, RN303, RN304: EXB-2HV103JV; EXB2HV_1; Mouser Part Number 667-EXB-2HV103JV
SW301, SW302, SW303, SW304, SW305, SW306, SW307, SW308, SW309, SW310, SW311, SW312, SW313, SW314, SW315, SW316, SW317, SW318, SW319, SW320, SW321, SW322, SW323, SW324, SW325, SW326, SW327, SW328, SW329: SW_Push; Kailh_socket_PG1350_reversible
SW330: RIC11-22S10D5S-TH
U301, U302, U303, U304: SN74HC165PWR; SOP65P640X120-16N; Mouser Part Number 595-SN74HC165PWR

Connections:
+3V3: RN301.1, RN301.2, RN301.3, RN301.4, RN301.5, RN301.6, RN301.7, RN301.8, RN302.1, RN302.2, RN302.3, RN302.4, RN302.5, RN302.6, RN302.7, RN302.8, RN303.1, RN303.2, RN303.3, RN303.4, RN303.5, RN303.6, RN303.7, RN303.8, RN304.1, RN304.2, RN304.3, RN304.4, RN304.5, RN304.6, RN304.7, RN304.8, U301.16 (VCC), U302.16 (VCC), U303.16 (VCC), U304.16 (VCC); also elsewhere on the board
/100- PSoM/A: SW330.A; also elsewhere on the board
/100- PSoM/B: SW330.B; also elsewhere on the board
/100- PSoM/PL: U301.1 (SH/~LD), U302.1 (SH/~LD), U303.1 (SH/~LD), U304.1 (SH/~LD); also elsewhere on the board
/100- PSoM/SPI_CLK: U301.2 (CLK), U302.2 (CLK), U303.2 (CLK), U304.2 (CLK); also elsewhere on the board
/100- PSoM/SPI_MISO: U301.9 (QH); also elsewhere on the board
/100- PSoM/SR_CE: U301.15 (CLK_INH), U302.15 (CLK_INH), U303.15 (CLK_INH), U304.15 (CLK_INH); also elsewhere on the board
/300- Shift Register - Switch/1: RN301.13, SW301.1, U301.6 (H)
/300- Shift Register - Switch/1-2: U301.10 (SER), U302.9 (QH)
/300- Shift Register - Switch/2: RN301.14, SW302.1, U301.5 (G)
/300- Shift Register - Switch/2-3: U302.10 (SER), U303.9 (QH)
/300- Shift Register - Switch/3: RN301.15, SW303.1, U301.4 (F)
/300- Shift Register - Switch/3-4: U303.10 (SER), U304.9 (QH)
/300- Shift Register - Switch/4: RN301.16, SW304.1, U301.3 (E)
/300- Shift Register - Switch/5: RN301.9, SW305.1, U301.14 (D)
/300- Shift Register - Switch/6: RN301.10, SW306.1, U301.13 (C)
/300- Shift Register - Switch/7: RN301.11, SW307.1, U301.12 (B)
/300- Shift Register - Switch/8: RN301.12, SW308.1, U301.11 (A)
/300- Shift Register - Switch/9: RN302.13, SW309.1, U302.6 (H)
/300- Shift Register - Switch/10: RN302.14, SW310.1, U302.5 (G)
/300- Shift Register - Switch/11: RN302.15, SW311.1, U302.4 (F)
/300- Shift Register - Switch/12: RN302.16, SW312.1, U302.3 (E)
/300- Shift Register - Switch/13: RN302.9, SW313.1, U302.14 (D)
/300- Shift Register - Switch/14: RN302.10, SW314.1, U302.13 (C)
/300- Shift Register - Switch/15: RN302.11, SW315.1, U302.12 (B)
/300- Shift Register - Switch/16: RN302.12, SW316.1, U302.11 (A)
/300- Shift Register - Switch/17: RN303.13, SW317.1, U303.6 (H)
/300- Shift Register - Switch/18: RN303.14, SW318.1, U303.5 (G)
/300- Shift Register - Switch/19: RN303.15, SW319.1, U303.4 (F)
/300- Shift Register - Switch/20: RN303.16, SW320.1, U303.3 (E)
/300- Shift Register - Switch/21: RN303.9, SW321.1, U303.14 (D)
/300- Shift Register - Switch/22: RN303.10, SW322.1, U303.13 (C)
/300- Shift Register - Switch/23: RN303.11, SW323.1, U303.12 (B)
/300- Shift Register - Switch/24: RN303.12, SW324.1, U303.11 (A)
/300- Shift Register - Switch/25: RN304.13, SW325.1, U304.6 (H)
/300- Shift Register - Switch/26: RN304.14, SW326.1, U304.5 (G)
/300- Shift Register - Switch/27: RN304.15, SW327.1, U304.4 (F)
/300- Shift Register - Switch/28: RN304.16, SW328.1, U304.3 (E)
/300- Shift Register - Switch/29: RN304.9, SW329.1, U304.14 (D)
/300- Shift Register - Switch/30: RN304.10, SW330.S1, U304.13 (C)
/300- Shift Register - Switch/31: RN304.11, U304.12 (B)
/300- Shift Register - Switch/32: RN304.12, U304.11 (A)
GND: SW301.2, SW302.2, SW303.2, SW304.2, SW305.2, SW306.2, SW307.2, SW308.2, SW309.2, SW310.2, SW311.2, SW312.2, SW313.2, SW314.2, SW315.2, SW316.2, SW317.2, SW318.2, SW319.2, SW320.2, SW321.2, SW322.2, SW323.2, SW324.2, SW325.2, SW326.2, SW327.2, SW328.2, SW329.2, SW330.C, SW330.S2, U301.8 (GND), U302.8 (GND), U303.8 (GND), U304.8 (GND); also elsewhere on the board

Notes on the sheet:
300- Shift Register - Switch

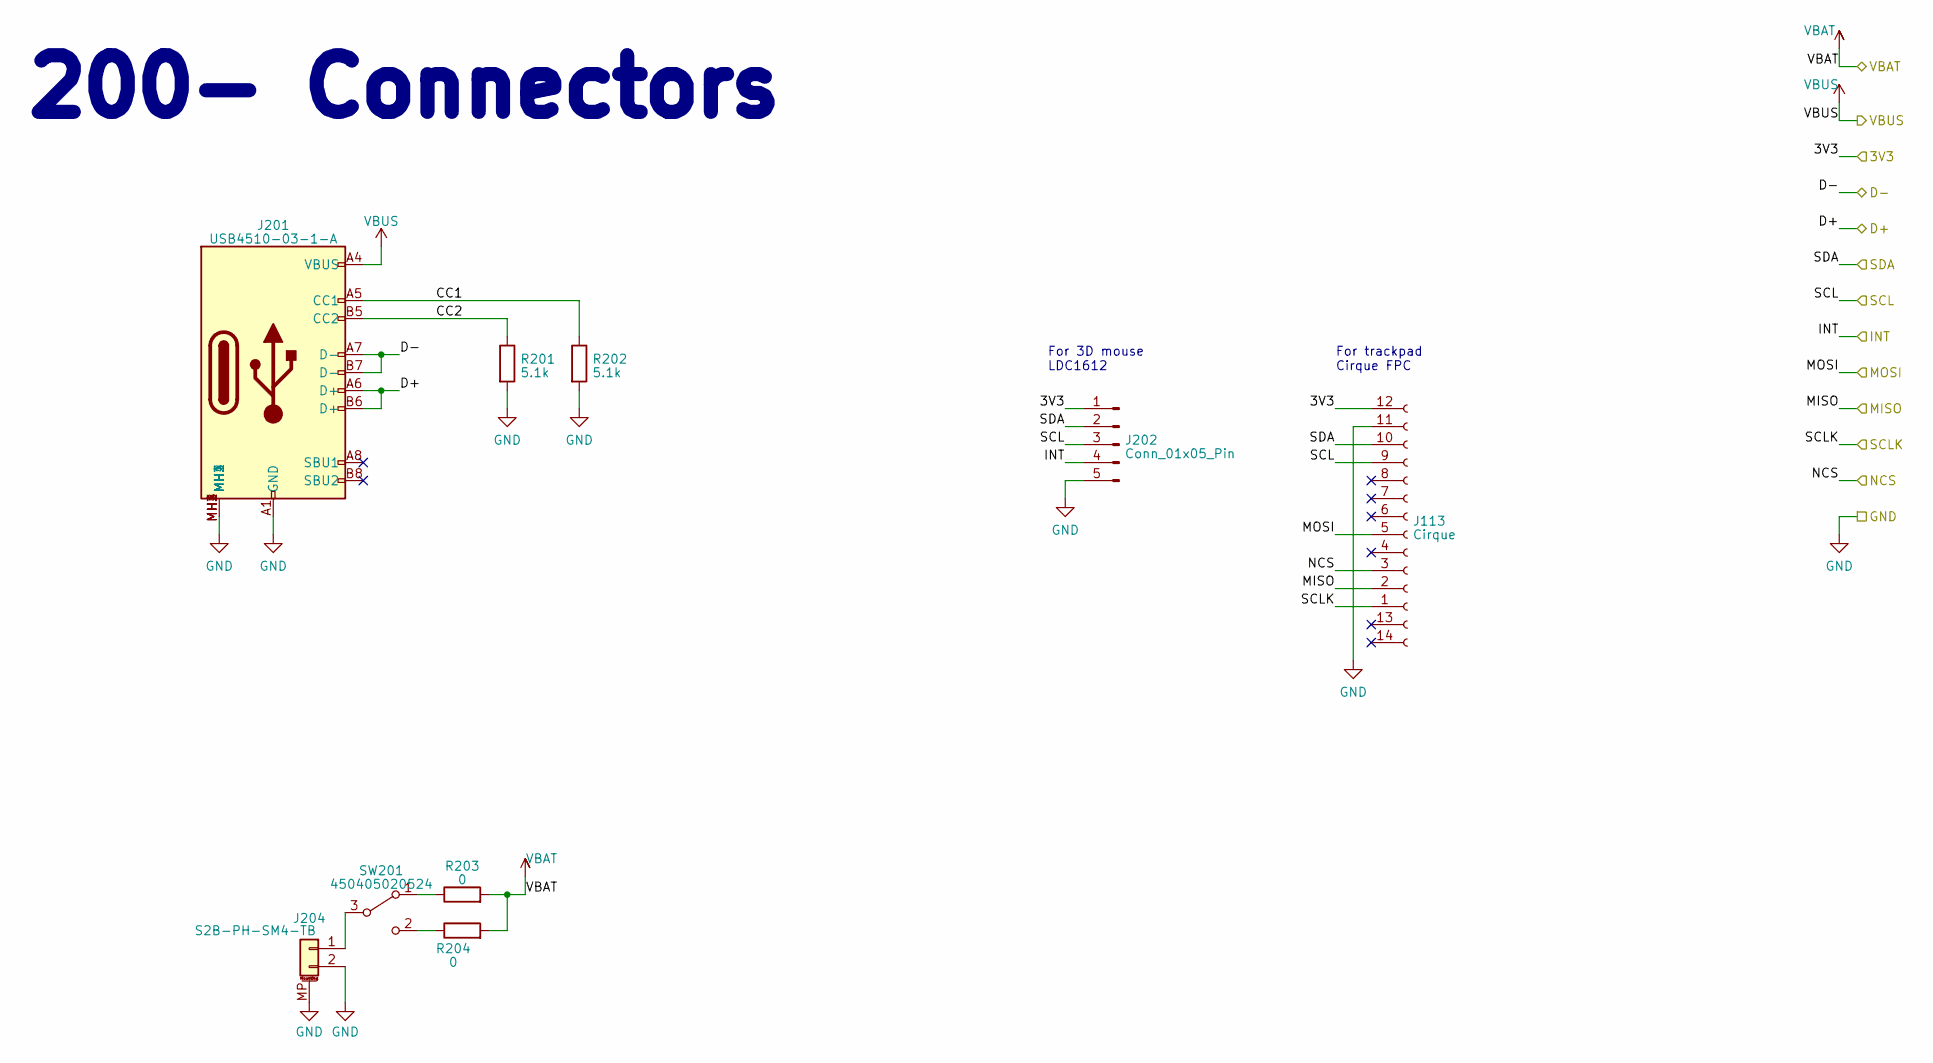
[picture p77: schematic Connectors.kicad_sch, PMK_Keyboard]

Parts:
J113: Cirque; Cirque trackpad
J201: USB4510-03-1-A; USB4510031A; Mouser Part Number 640-USB4510031A
J202: Conn_01x05_Pin; SMD_CONN_01x5_1.5mm
J204: S2B-PH-SM4-TB; JST_PH_S2B-PH-SM4-TB_1x02-1MP_P2.00mm_Horizontal_DUALSIDE
R201, R202: 5.1k; R_0201_0603Metric
R203, R204: 0; R_0201_0603Metric
SW201: 450405020524; 450405020524_DUALSIDE

Connections:
+3V3: J202.1; also elsewhere on the board
/100- PSoM/D+: J201.A6 (D+), J201.B6 (D+); also elsewhere on the board
/100- PSoM/D-: J201.A7 (D-), J201.B7 (D-); also elsewhere on the board
/100- PSoM/INT: J202.4; also elsewhere on the board
/100- PSoM/SCL: J202.3; also elsewhere on the board
/100- PSoM/SDA: J202.2; also elsewhere on the board
/200- Connectors/CC1: J201.A5 (CC1), R202.1
/200- Connectors/CC2: J201.B5 (CC2), R201.1
/VBAT: R203.2, R204.2; also elsewhere on the board
GND: J201.A1 (GND), J201.A12 (GND), J201.B1 (GND), J201.B12 (GND), J201.MH1, J201.MH2, J201.MH3, J201.MH4, J202.5, J204.2, J204.MP (MountPin), R201.2, R202.2; also elsewhere on the board
unnamed: J204.1, SW201.3 (B)
unnamed: R203.1, SW201.1 (A)
unnamed: R204.1, SW201.2 (C)
VBUS: J201.A4 (VBUS), J201.A9 (VBUS), J201.B4 (VBUS), J201.B9 (VBUS); also elsewhere on the board

Notes on the sheet:
200- Connectors
For trackpad Cirque FPC
For 3D mouse LDC1612

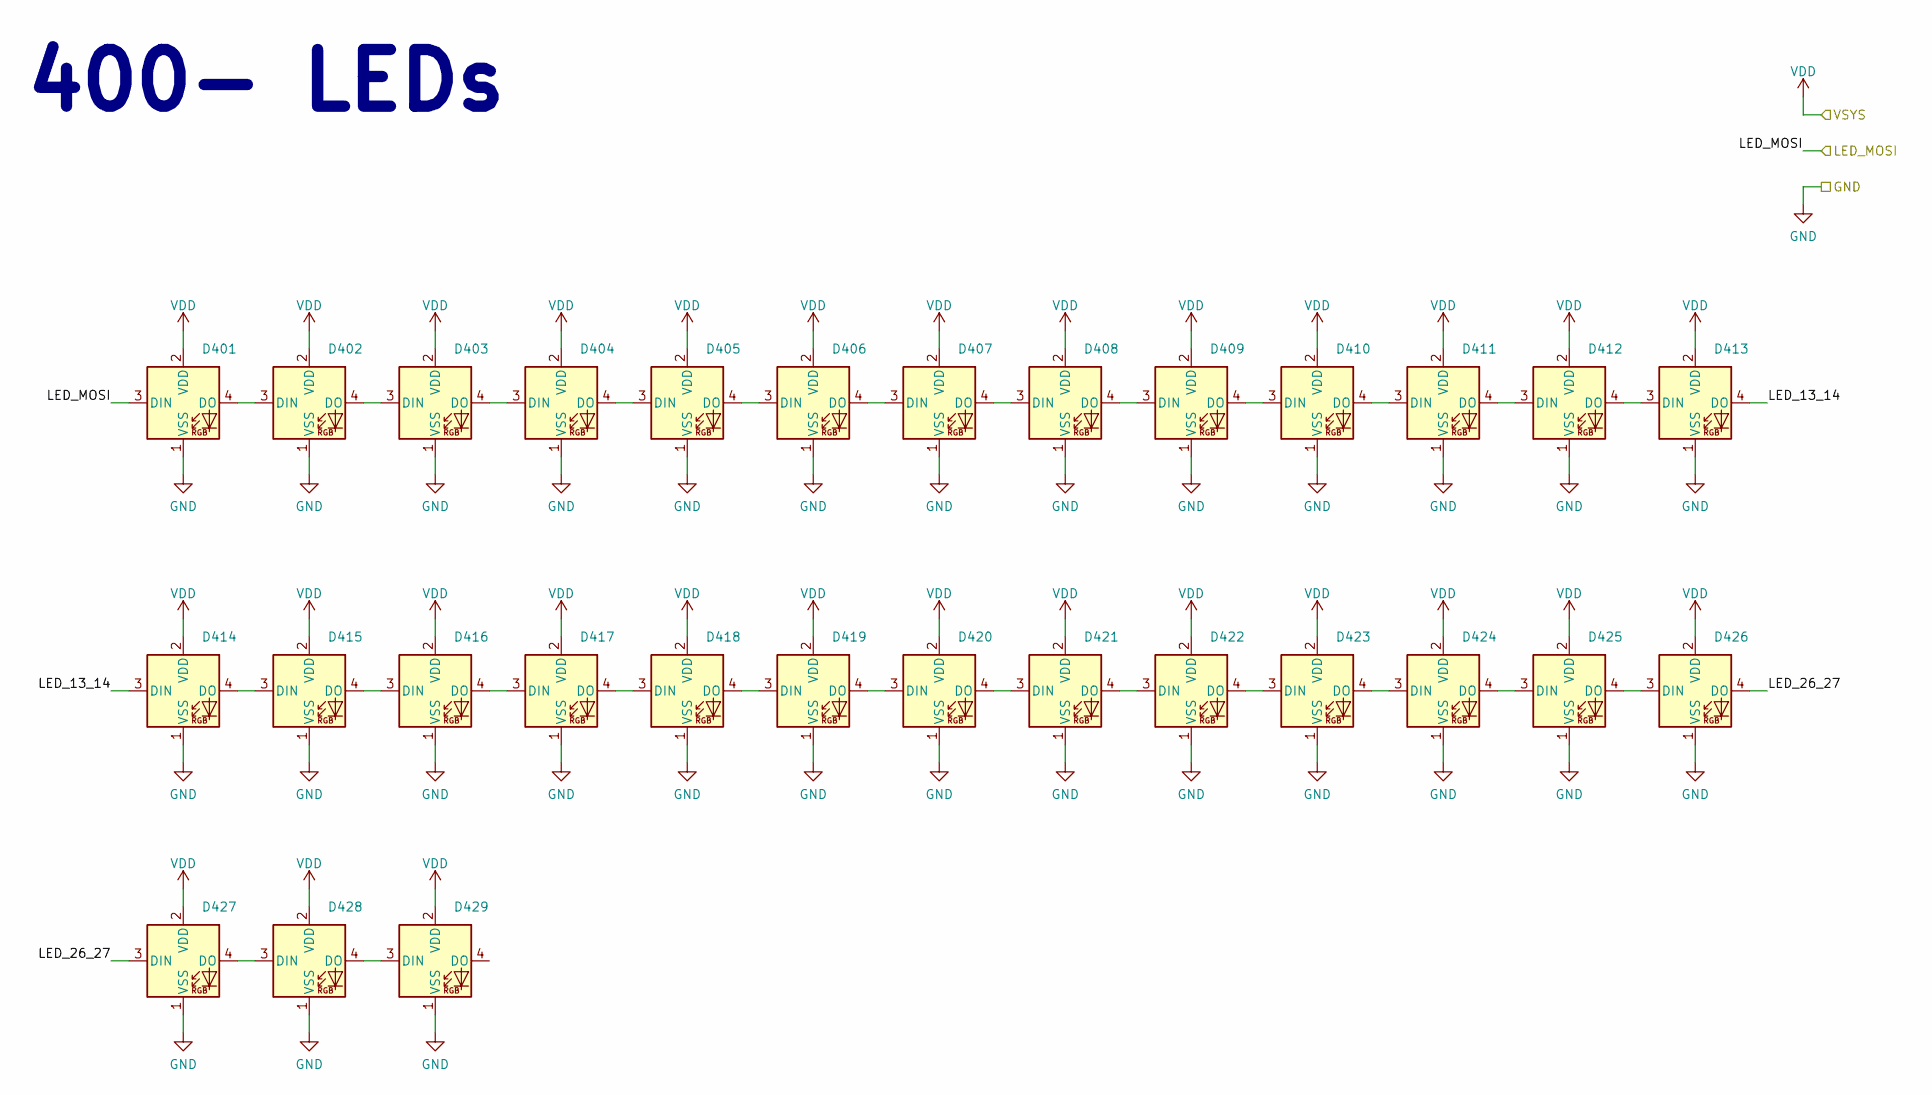
[picture p78: schematic LEDs.kicad_sch, PMK_Keyboard]

Parts:
D401, D402, D403, D404, D405, D406, D407, D408, D409, D410, D411, D412, D413, D414, D415, D416, D417, D418, D419, D420, D421, D422, D423, D424, D425, D426, D427, D428, D429: YF923_2020_WS2812_LED; YF923_2020_WS2812_LED_DUALSIDE

Connections:
/100- PSoM/LED_MOSI: D401.3 (DIN); also elsewhere on the board
/400- LEDs/LED_13_14: D413.4 (DO), D414.3 (DIN)
/400- LEDs/LED_26_27: D426.4 (DO), D427.3 (DIN)
GND: D401.1 (VSS), D402.1 (VSS), D403.1 (VSS), D404.1 (VSS), D405.1 (VSS), D406.1 (VSS), D407.1 (VSS), D408.1 (VSS), D409.1 (VSS), D410.1 (VSS), D411.1 (VSS), D412.1 (VSS), D413.1 (VSS), D414.1 (VSS), D415.1 (VSS), D416.1 (VSS), D417.1 (VSS), D418.1 (VSS), D419.1 (VSS), D420.1 (VSS), D421.1 (VSS), D422.1 (VSS), D423.1 (VSS), D424.1 (VSS), D425.1 (VSS), D426.1 (VSS), D427.1 (VSS), D428.1 (VSS), D429.1 (VSS); also elsewhere on the board
unnamed: D401.4 (DO), D402.3 (DIN)
unnamed: D402.4 (DO), D403.3 (DIN)
unnamed: D403.4 (DO), D404.3 (DIN)
unnamed: D404.4 (DO), D405.3 (DIN)
unnamed: D405.4 (DO), D406.3 (DIN)
unnamed: D406.4 (DO), D407.3 (DIN)
unnamed: D407.4 (DO), D408.3 (DIN)
unnamed: D408.4 (DO), D409.3 (DIN)
unnamed: D409.4 (DO), D410.3 (DIN)
unnamed: D410.4 (DO), D411.3 (DIN)
unnamed: D411.4 (DO), D412.3 (DIN)
unnamed: D412.4 (DO), D413.3 (DIN)
unnamed: D414.4 (DO), D415.3 (DIN)
unnamed: D415.4 (DO), D416.3 (DIN)
unnamed: D416.4 (DO), D417.3 (DIN)
unnamed: D417.4 (DO), D418.3 (DIN)
unnamed: D418.4 (DO), D419.3 (DIN)
unnamed: D419.4 (DO), D420.3 (DIN)
unnamed: D420.4 (DO), D421.3 (DIN)
unnamed: D421.4 (DO), D422.3 (DIN)
unnamed: D422.4 (DO), D423.3 (DIN)
unnamed: D423.4 (DO), D424.3 (DIN)
unnamed: D424.4 (DO), D425.3 (DIN)
unnamed: D425.4 (DO), D426.3 (DIN)
unnamed: D427.4 (DO), D428.3 (DIN)
unnamed: D428.4 (DO), D429.3 (DIN)
VDD: D401.2 (VDD), D402.2 (VDD), D403.2 (VDD), D404.2 (VDD), D405.2 (VDD), D406.2 (VDD), D407.2 (VDD), D408.2 (VDD), D409.2 (VDD), D410.2 (VDD), D411.2 (VDD), D412.2 (VDD), D413.2 (VDD), D414.2 (VDD), D415.2 (VDD), D416.2 (VDD), D417.2 (VDD), D418.2 (VDD), D419.2 (VDD), D420.2 (VDD), D421.2 (VDD), D422.2 (VDD), D423.2 (VDD), D424.2 (VDD), D425.2 (VDD), D426.2 (VDD), D427.2 (VDD), D428.2 (VDD), D429.2 (VDD); also elsewhere on the board

Notes on the sheet:
400- LEDs

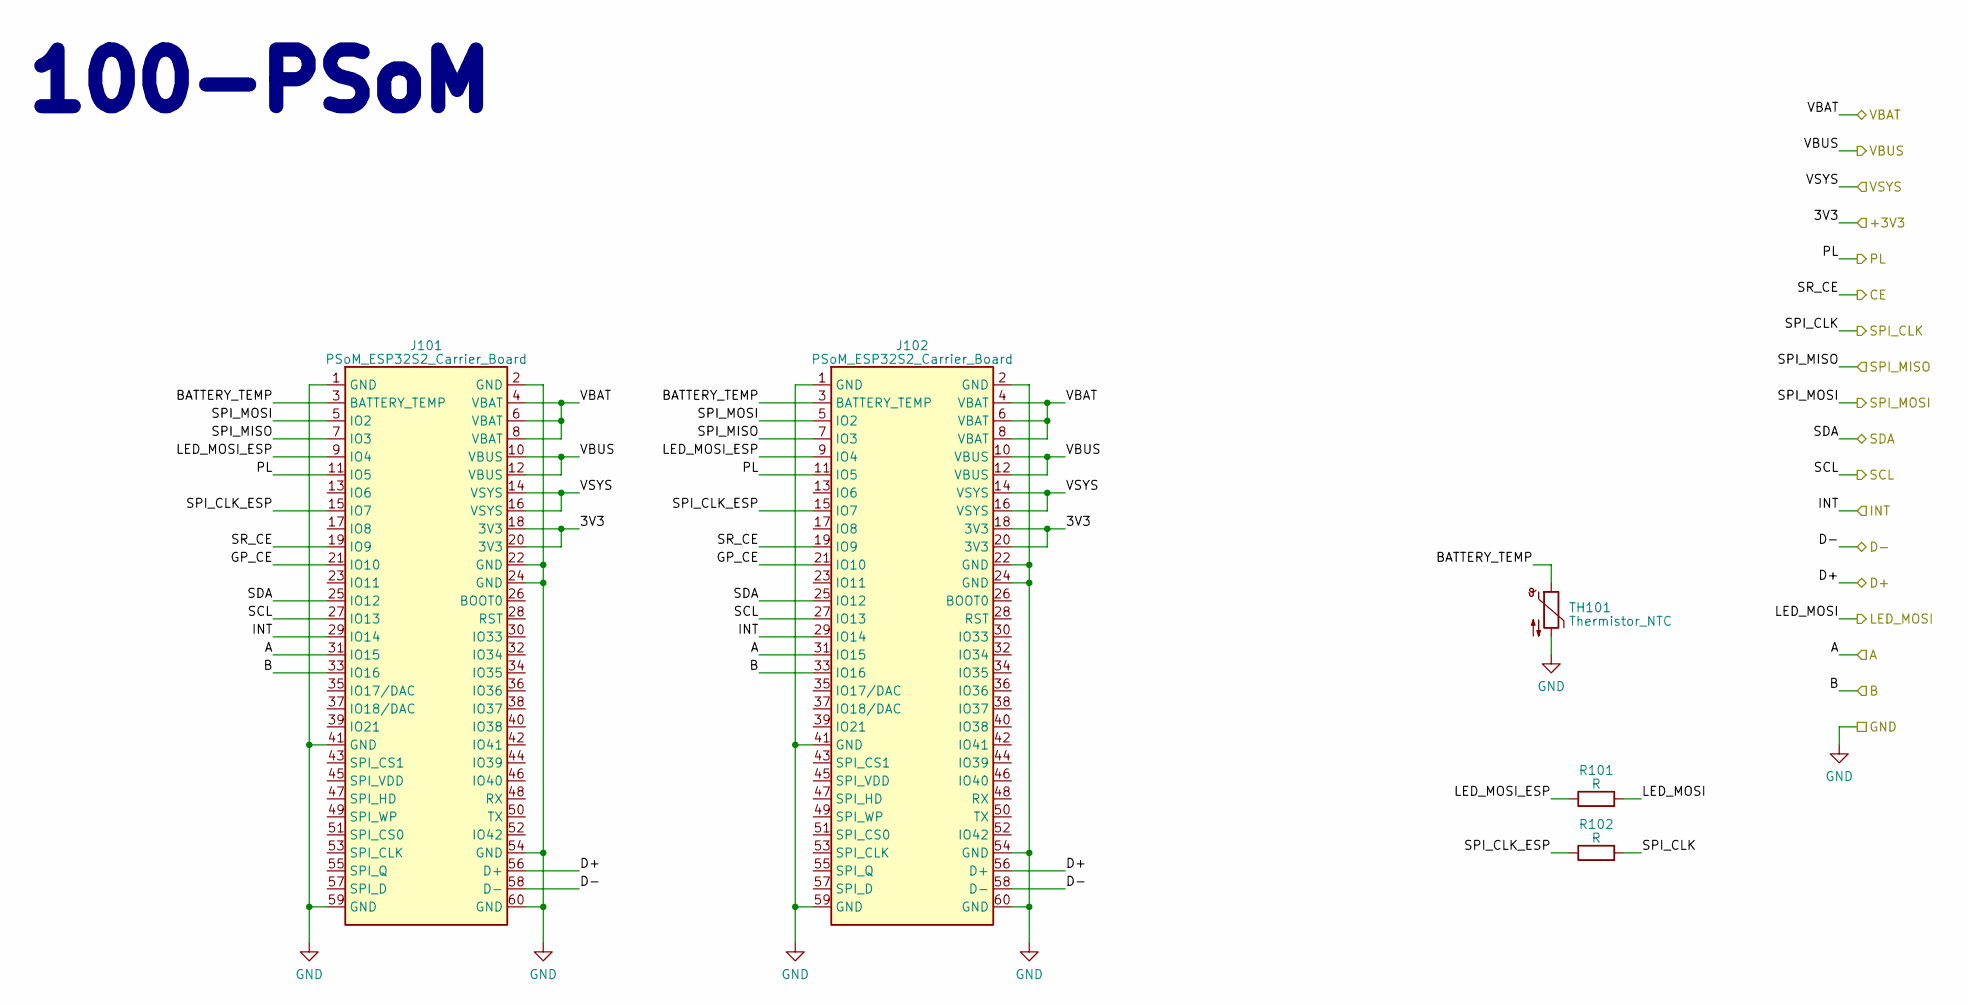
[picture p79: schematic PSoM.kicad_sch, PMK_Keyboard]

Parts:
J101, J102: PSoM_ESP32S2_Carrier_Board; PSoM_ESP32S2_00
R101, R102: R; R_0402_1005Metric
TH101: Thermistor_NTC; R_0402_1005Metric

Connections:
+3V3: J101.18 (3V3), J101.20 (3V3), J102.18 (3V3), J102.20 (3V3); also elsewhere on the board
/100- PSoM/A: J101.31 (IO15), J102.31 (IO15); also elsewhere on the board
/100- PSoM/B: J101.33 (IO16), J102.33 (IO16); also elsewhere on the board
/100- PSoM/BATTERY_TEMP: J101.3 (BATTERY_TEMP), J102.3 (BATTERY_TEMP), TH101.1
/100- PSoM/D+: J101.56 (D+), J102.56 (D+); also elsewhere on the board
/100- PSoM/D-: J101.58 (D-), J102.58 (D-); also elsewhere on the board
/100- PSoM/GP_CE: J101.21 (IO10), J102.21 (IO10)
/100- PSoM/INT: J101.29 (IO14), J102.29 (IO14); also elsewhere on the board
/100- PSoM/LED_MOSI: R101.2; also elsewhere on the board
/100- PSoM/LED_MOSI_ESP: J101.9 (IO4), J102.9 (IO4), R101.1
/100- PSoM/PL: J101.11 (IO5), J102.11 (IO5); also elsewhere on the board
/100- PSoM/SCL: J101.27 (IO13), J102.27 (IO13); also elsewhere on the board
/100- PSoM/SDA: J101.25 (IO12), J102.25 (IO12); also elsewhere on the board
/100- PSoM/SPI_CLK: R102.2; also elsewhere on the board
/100- PSoM/SPI_CLK_ESP: J101.15 (IO7), J102.15 (IO7), R102.1
/100- PSoM/SPI_MISO: J101.7 (IO3), J102.7 (IO3); also elsewhere on the board
/100- PSoM/SPI_MOSI: J101.5 (IO2), J102.5 (IO2); also elsewhere on the board
/100- PSoM/SR_CE: J101.19 (IO9), J102.19 (IO9); also elsewhere on the board
/VBAT: J101.4 (VBAT), J101.6 (VBAT), J101.8 (VBAT), J102.4 (VBAT), J102.6 (VBAT), J102.8 (VBAT); also elsewhere on the board
GND: J101.1 (GND), J101.2 (GND), J101.22 (GND), J101.24 (GND), J101.41 (GND), J101.54 (GND), J101.59 (GND), J101.60 (GND), J102.1 (GND), J102.2 (GND), J102.22 (GND), J102.24 (GND), J102.41 (GND), J102.54 (GND), J102.59 (GND), J102.60 (GND), TH101.2; also elsewhere on the board
VBUS: J101.10 (VBUS), J101.12 (VBUS), J102.10 (VBUS), J102.12 (VBUS); also elsewhere on the board
VDD: J101.14 (VSYS), J101.16 (VSYS), J102.14 (VSYS), J102.16 (VSYS); also elsewhere on the board

Notes on the sheet:
100-PSoM

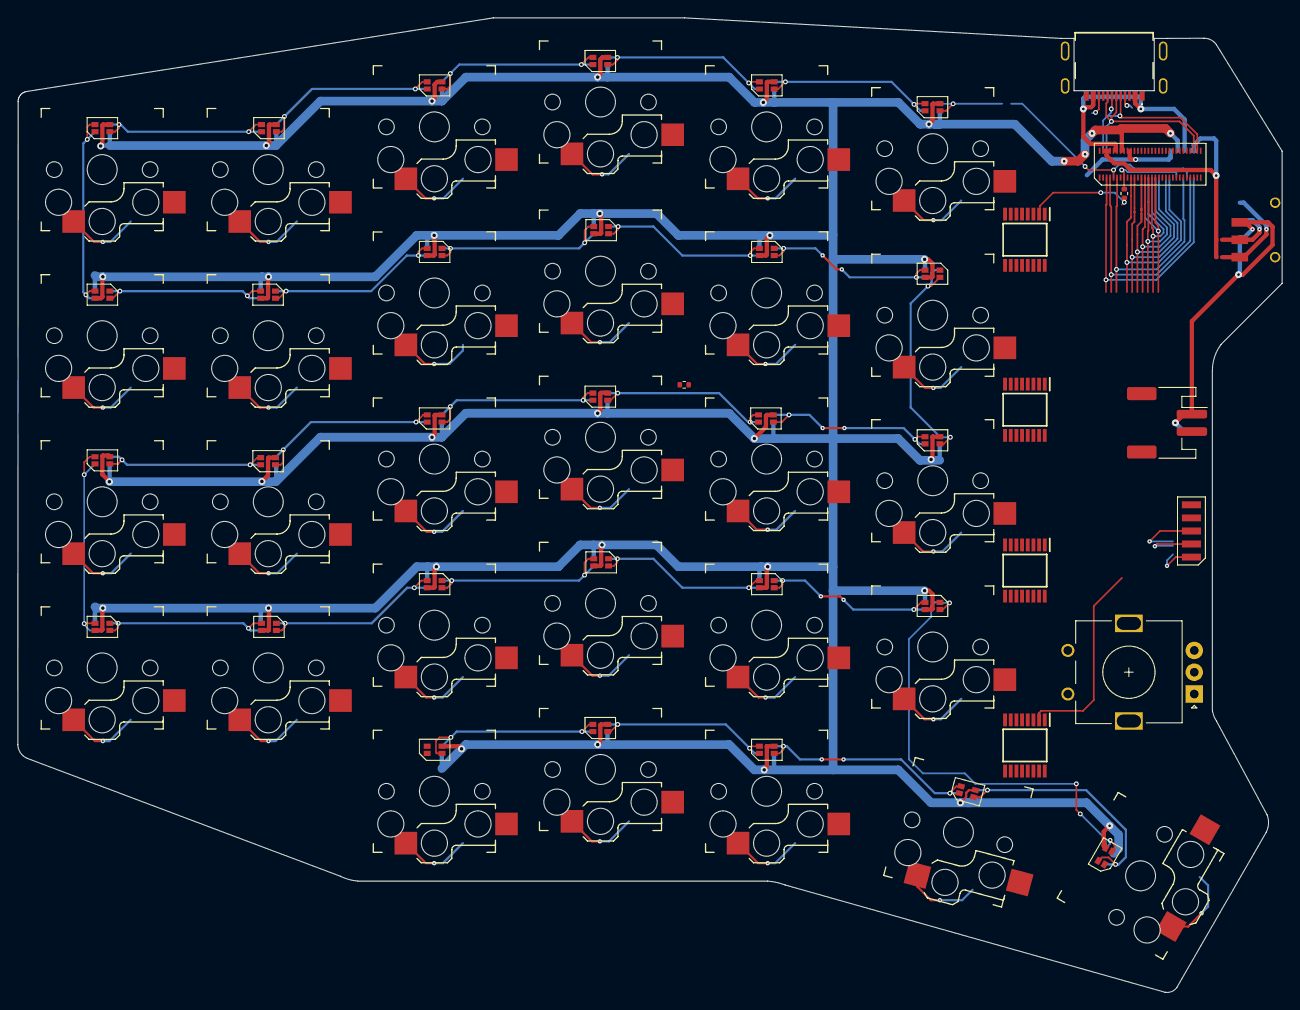
[picture p80: board PMK_Keyboard_HW01.kicad_pcb from above]

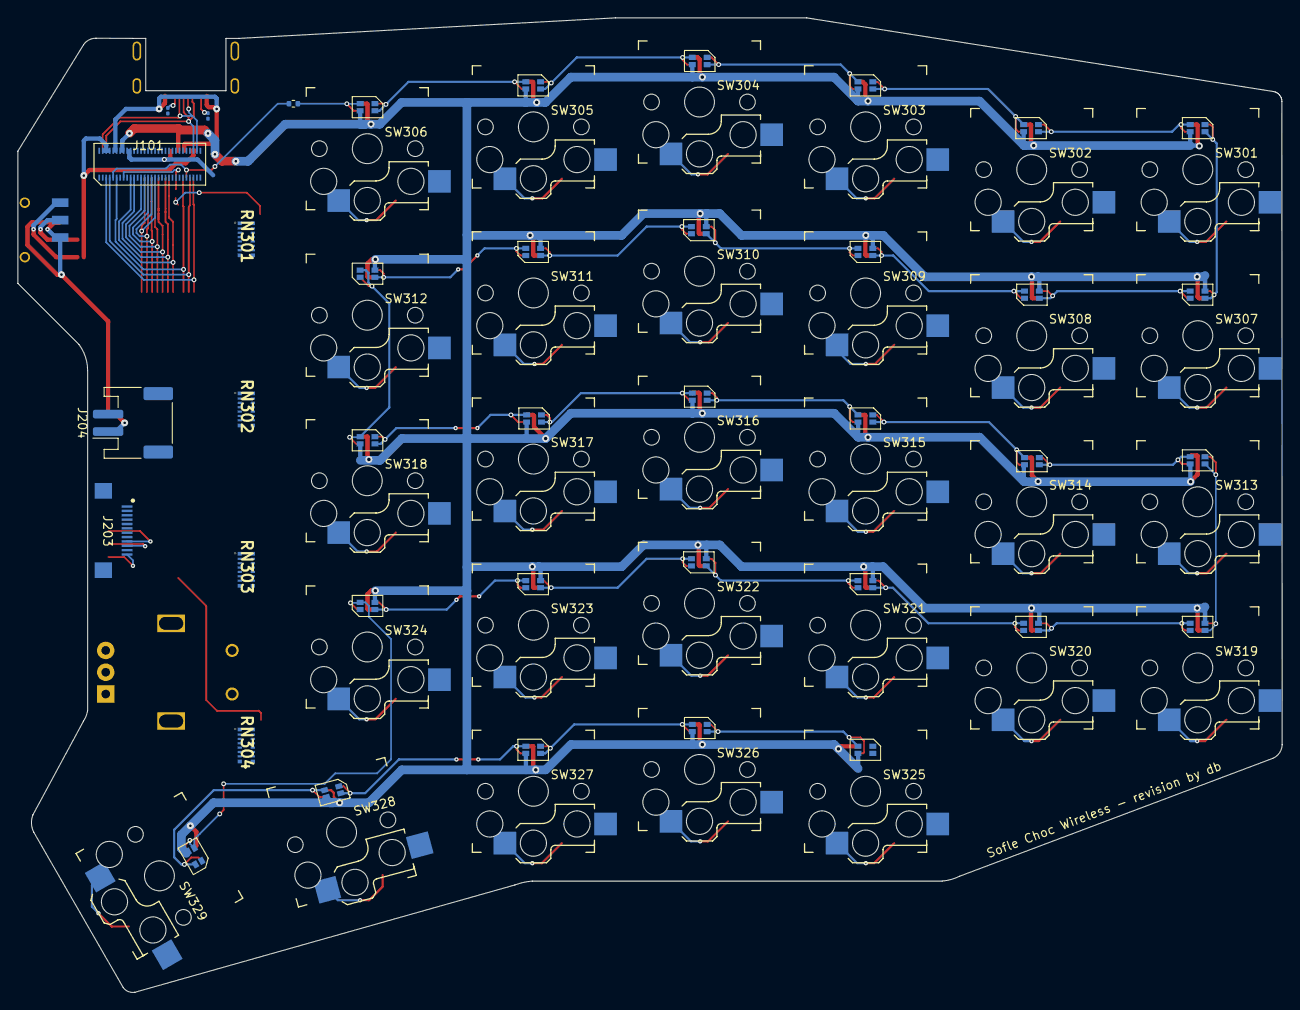
[picture p81: board PMK_Keyboard_HW01.kicad_pcb from below]

Board: 2 copper layers, 145.0 x 111.8 mm, 81 parts (10 on the bottom side), 90 nets.

Other parts of the board:
J203: Cirque; Cirque trackpad

Their connections:
+3V3: J203.12; also elsewhere on the board
/100- PSoM/SCL: J203.9; also elsewhere on the board
/100- PSoM/SDA: J203.10; also elsewhere on the board
/100- PSoM/SPI_CLK: J203.1; also elsewhere on the board
/100- PSoM/SPI_MISO: J203.2; also elsewhere on the board
/100- PSoM/SPI_MOSI: J203.5; also elsewhere on the board
/100- PSoM/SR_CE: J203.3; also elsewhere on the board
GND: J203.11; also elsewhere on the board
